antmicro/jetson-agx-thor-baseboard/SoM_ctrl.kicad_sch

## KiCad design SoM_ctrl.kicad_sch (2025-08-14)

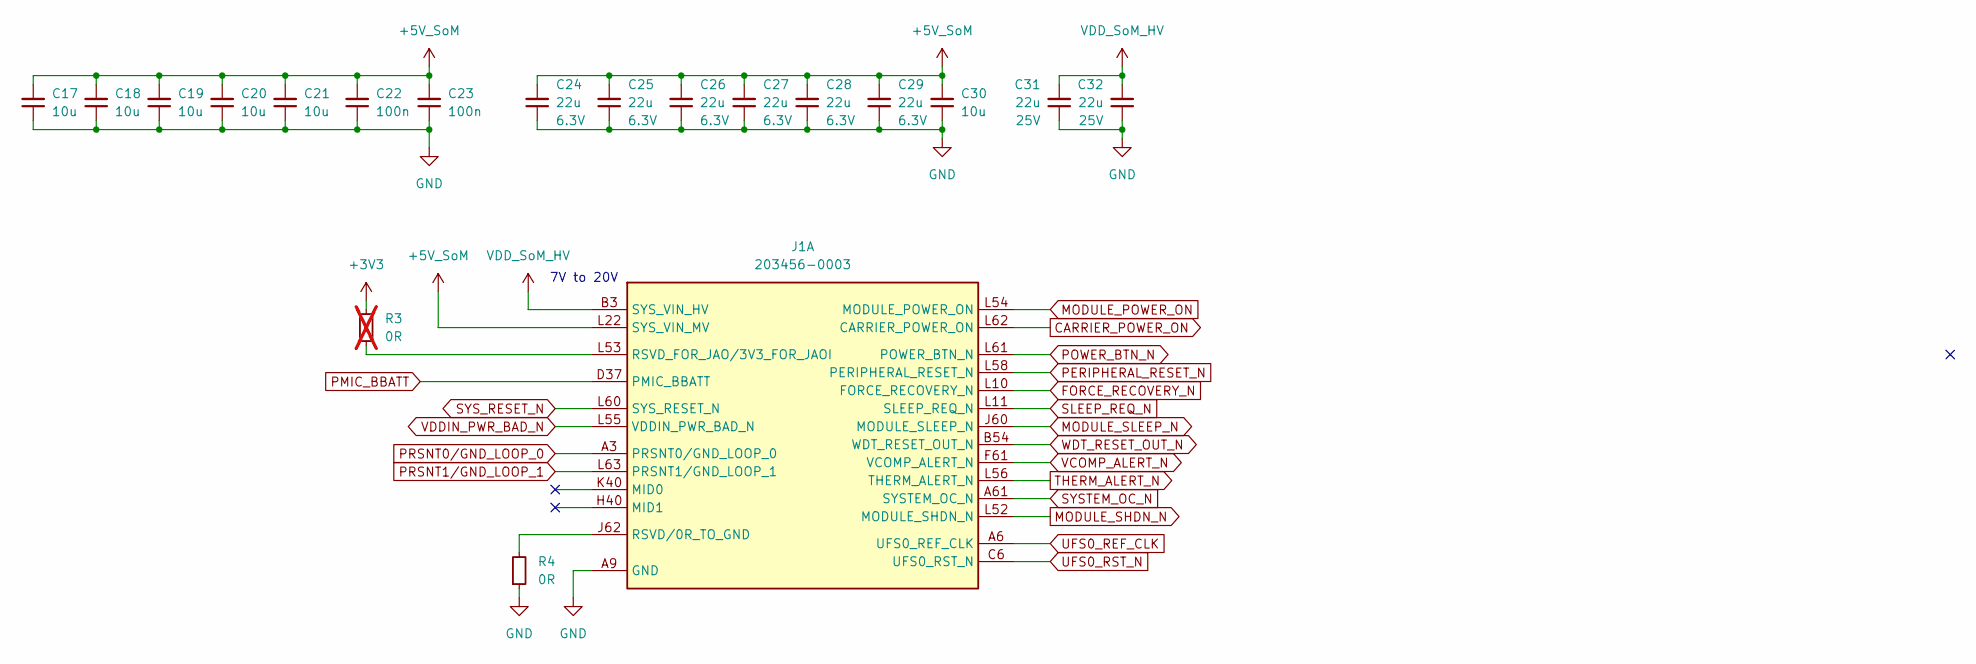
[picture p2: schematic SoM_ctrl.kicad_sch]

Parts:
C17, C18, C19, C20, C21, C30: C_10u_0603; C_0603_1608Metric; MPN GRM188R61A106KE69D
C22, C23: C_100n_16V_X7R_0402; C_0402_1005Metric; Voltage 16V; MPN C0402C104J4RAC7411
C24, C25, C26, C27, C28, C29: C_22u_6.3V_X7R_0805; C_0805_2012Metric; Voltage 6.3V; MPN GRM21BZ70J226ME44L
C31, C32: C_22u_25V_0805; C_0805_2012Metric; Voltage 25V; MPN CL21A226MAYNNNE
J1: Hermaphroditic_Molex_203456-0003_CUSTOM_Jetson_Or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; Conn_Hermaphroditic_Molex_203456-0003_mirrored; MPN 203456-0003
R3: R_0R_0603; R_0603_1608Metric; MPN CR0603-J/-000ELF; not fitted
R4: R_0R_0402; R_0402_1005Metric; MPN ERJ2GE0R00X

Connections:
+3V3: R3.2
+5V_SoM: C17.2, C18.2, C19.2, C20.2, C21.2, C22.2, C23.2, C24.2, C25.2, C26.2, C27.2, C28.2, C29.2, C30.2, J1.L22 (SYS_VIN_MV), J1.L23 (SYS_VIN_MV), J1.L26 (SYS_VIN_MV), J1.L27 (SYS_VIN_MV), J1.L30 (SYS_VIN_MV), J1.L31 (SYS_VIN_MV), J1.L34 (SYS_VIN_MV), J1.L35 (SYS_VIN_MV), J1.L38 (SYS_VIN_MV), J1.L39 (SYS_VIN_MV)
CARRIER_POWER_ON: J1.L62 (CARRIER_POWER_ON)
FORCE_RECOVERY_N: J1.L10 (FORCE_RECOVERY_N)
GND: C17.1, C18.1, C19.1, C20.1, C21.1, C22.1, C23.1, C24.1, C25.1, C26.1, C27.1, C28.1, C29.1, C30.1, C31.1, C32.1, J1.A9 (GND), J1.A12 (GND), J1.A13 (GND), J1.A16 (GND), J1.A17 (GND), J1.A20 (GND), J1.A21 (GND), J1.A24 (GND), J1.A25 (GND), J1.A28 (GND), J1.A29 (GND), J1.A32 (GND), J1.A33 (GND), J1.A36 (GND), J1.A37 (GND), J1.A40 (GND), J1.A43 (GND), J1.A46 (GND), J1.A49 (GND), J1.A52 (GND), J1.A63 (GND), J1.B4 (GND), J1.B7 (GND), J1.B11 (GND), J1.B14 (GND), J1.B15 (GND), J1.B18 (GND), J1.B19 (GND), J1.B22 (GND), J1.B23 (GND), J1.B26 (GND), J1.B27 (GND), J1.B30 (GND), J1.B31 (GND), J1.B34 (GND), J1.B35 (GND), J1.B38 (GND), J1.B39 (GND), J1.B41 (GND), J1.B44 (GND), J1.B47 (GND), J1.B50 (GND), J1.B53 (GND), J1.B57 (GND), J1.C3 (GND), J1.C9 (GND), J1.C12 (GND), J1.C13 (GND), J1.C16 (GND), J1.C17 (GND), J1.C20 (GND), J1.C21 (GND), J1.C24 (GND), J1.C25 (GND), J1.C28 (GND), J1.C29 (GND), J1.C32 (GND), J1.C33 (GND), J1.C36 (GND), J1.C37 (GND), J1.C40 (GND), J1.C43 (GND), J1.C46 (GND), J1.C49 (GND), J1.C52 (GND), J1.C62 (GND), J1.D4 (GND), J1.D7 (GND), J1.D11 (GND), J1.D14 (GND), J1.D15 (GND), J1.D18 (GND), J1.D19 (GND), J1.D22 (GND), J1.D23 (GND), J1.D26 (GND), J1.D27 (GND), J1.D30 (GND), J1.D31 (GND), J1.D34 (GND), J1.D35 (GND), J1.D38 (GND), J1.D39 (GND), J1.D41 (GND), J1.D44 (GND), J1.D47 (GND), J1.D50 (GND), J1.D53 (GND), J1.D57 (GND), J1.D63 (GND), J1.E3 (GND), J1.E9 (GND), J1.E12 (GND), J1.E13 (GND), J1.E16 (GND), J1.E17 (GND), J1.E20 (GND), J1.E21 (GND), J1.E24 (GND), J1.E25 (GND), J1.E28 (GND), J1.E29 (GND), J1.E32 (GND), J1.E33 (GND), J1.E36 (GND), J1.E37 (GND), J1.E40 (GND), J1.E43 (GND), J1.E46 (GND), J1.E49 (GND), J1.E52 (GND), J1.E57 (GND), J1.E62 (GND), J1.F4 (GND), J1.F7 (GND), J1.F11 (GND), J1.F14 (GND), J1.F15 (GND), J1.F18 (GND), J1.F19 (GND), J1.F22 (GND), J1.F23 (GND), J1.F26 (GND), J1.F27 (GND), J1.F30 (GND), J1.F31 (GND), J1.F34 (GND), J1.F35 (GND), J1.F38 (GND), J1.F39 (GND), J1.F41 (GND), J1.F44 (GND), J1.F47 (GND), J1.F50 (GND), J1.F57 (GND), J1.F62 (GND), J1.G3 (GND), J1.G9 (GND), J1.G12 (GND), J1.G13 (GND), J1.G16 (GND), J1.G17 (GND), J1.G20 (GND), J1.G21 (GND), J1.G24 (GND), J1.G25 (GND), J1.G28 (GND), J1.G29 (GND), J1.G32 (GND), J1.G33 (GND), J1.G36 (GND), J1.G37 (GND), J1.G40 (GND), J1.G43 (GND), J1.G46 (GND), J1.G49 (GND), J1.G52 (GND), J1.G57 (GND), J1.G62 (GND), J1.H4 (GND), J1.H7 (GND), J1.H11 (GND), J1.H14 (GND), J1.H15 (GND), J1.H18 (GND), J1.H19 (GND), J1.H22 (GND), J1.H23 (GND), J1.H26 (GND), J1.H27 (GND), J1.H30 (GND), J1.H31 (GND), J1.H34 (GND), J1.H35 (GND), J1.H38 (GND), J1.H39 (GND), J1.H41 (GND), J1.H44 (GND), J1.H47 (GND), J1.H50 (GND), J1.H56 (GND), J1.H63 (GND), J1.J3 (GND), J1.J8 (GND), J1.J12 (GND), J1.J13 (GND), J1.J16 (GND), J1.J17 (GND), J1.J20 (GND), J1.J21 (GND), J1.J24 (GND), J1.J25 (GND), J1.J28 (GND), J1.J29 (GND), J1.J32 (GND), J1.J33 (GND), J1.J36 (GND), J1.J37 (GND), J1.J40 (GND), J1.J43 (GND), J1.J46 (GND), J1.J49 (GND), J1.J56 (GND), J1.K4 (GND), J1.K8 (GND), J1.K11 (GND), J1.K14 (GND), J1.K15 (GND), J1.K18 (GND), J1.K19 (GND), J1.K22 (GND), J1.K23 (GND), J1.K26 (GND), J1.K27 (GND), J1.K30 (GND), J1.K31 (GND), J1.K34 (GND), J1.K35 (GND), J1.K38 (GND), J1.K39 (GND), J1.K41 (GND), J1.K42 (GND), J1.K45 (GND), J1.K48 (GND), J1.K55 (GND), J1.K63 (GND), J1.L3 (GND), J1.L7 (GND), J1.L12 (GND), J1.L13 (GND), J1.L16 (GND), J1.L17 (GND), J1.L20 (GND), J1.L21 (GND), J1.L24 (GND), J1.L25 (GND), J1.L28 (GND), J1.L29 (GND), J1.L32 (GND), J1.L33 (GND), J1.L36 (GND), J1.L37 (GND), J1.L40 (GND), J1.L43 (GND), J1.L46 (GND), R4.1
MODULE_POWER_ON: J1.L54 (MODULE_POWER_ON)
MODULE_SHDN_N: J1.L52 (MODULE_SHDN_N)
MODULE_SLEEP_N: J1.J60 (MODULE_SLEEP_N)
unnamed: J1.J62 (RSVD/0R_TO_GND), R4.2
unnamed: J1.L53 (RSVD_FOR_JAO/3V3_FOR_JAOI), R3.1
PERIPHERAL_RESET_N: J1.L58 (PERIPHERAL_RESET_N)
PMIC_BBATT: J1.D37 (PMIC_BBATT)
POWER_BTN_N: J1.L61 (POWER_BTN_N)
PRSNT0/GND_LOOP_0: J1.A3 (PRSNT0/GND_LOOP_0)
PRSNT1/GND_LOOP_1: J1.L63 (PRSNT1/GND_LOOP_1)
SLEEP_REQ_N: J1.L11 (SLEEP_REQ_N)
SYSTEM_OC_N: J1.A61 (SYSTEM_OC_N)
SYS_RESET_N: J1.L60 (SYS_RESET_N)
THERM_ALERT_N: J1.L56 (THERM_ALERT_N)
UFS0_REF_CLK: J1.A6 (UFS0_REF_CLK)
UFS0_RST_N: J1.C6 (UFS0_RST_N)
VCOMP_ALERT_N: J1.F61 (VCOMP_ALERT_N)
VDDIN_PWR_BAD_N: J1.L55 (VDDIN_PWR_BAD_N)
VDD_SoM_HV: C31.2, C32.2, J1.B3 (SYS_VIN_HV), J1.B63 (SYS_VIN_HV), J1.C1 (SYS_VIN_HV), J1.C2 (SYS_VIN_HV), J1.C63 (SYS_VIN_HV), J1.C64 (SYS_VIN_HV), J1.C65 (SYS_VIN_HV), J1.D1 (SYS_VIN_HV), J1.D2 (SYS_VIN_HV), J1.D3 (SYS_VIN_HV), J1.D64 (SYS_VIN_HV), J1.D65 (SYS_VIN_HV), J1.E1 (SYS_VIN_HV), J1.E2 (SYS_VIN_HV), J1.E63 (SYS_VIN_HV), J1.E64 (SYS_VIN_HV), J1.E65 (SYS_VIN_HV), J1.F1 (SYS_VIN_HV), J1.F2 (SYS_VIN_HV), J1.F3 (SYS_VIN_HV), J1.F63 (SYS_VIN_HV), J1.F64 (SYS_VIN_HV), J1.F65 (SYS_VIN_HV), J1.G1 (SYS_VIN_HV), J1.G2 (SYS_VIN_HV), J1.G63 (SYS_VIN_HV), J1.G64 (SYS_VIN_HV), J1.G65 (SYS_VIN_HV), J1.H1 (SYS_VIN_HV), J1.H2 (SYS_VIN_HV), J1.H3 (SYS_VIN_HV), J1.H64 (SYS_VIN_HV), J1.H65 (SYS_VIN_HV), J1.J1 (SYS_VIN_HV), J1.J2 (SYS_VIN_HV), J1.J63 (SYS_VIN_HV), J1.J64 (SYS_VIN_HV), J1.J65 (SYS_VIN_HV), J1.K3 (SYS_VIN_HV)
WDT_RESET_OUT_N: J1.B54 (WDT_RESET_OUT_N)

Notes on the sheet:
7V to 20V
