antmicro/jetson-agx-thor-baseboard/csi.kicad_sch

## KiCad design csi.kicad_sch (2026-02-19, an earlier design)

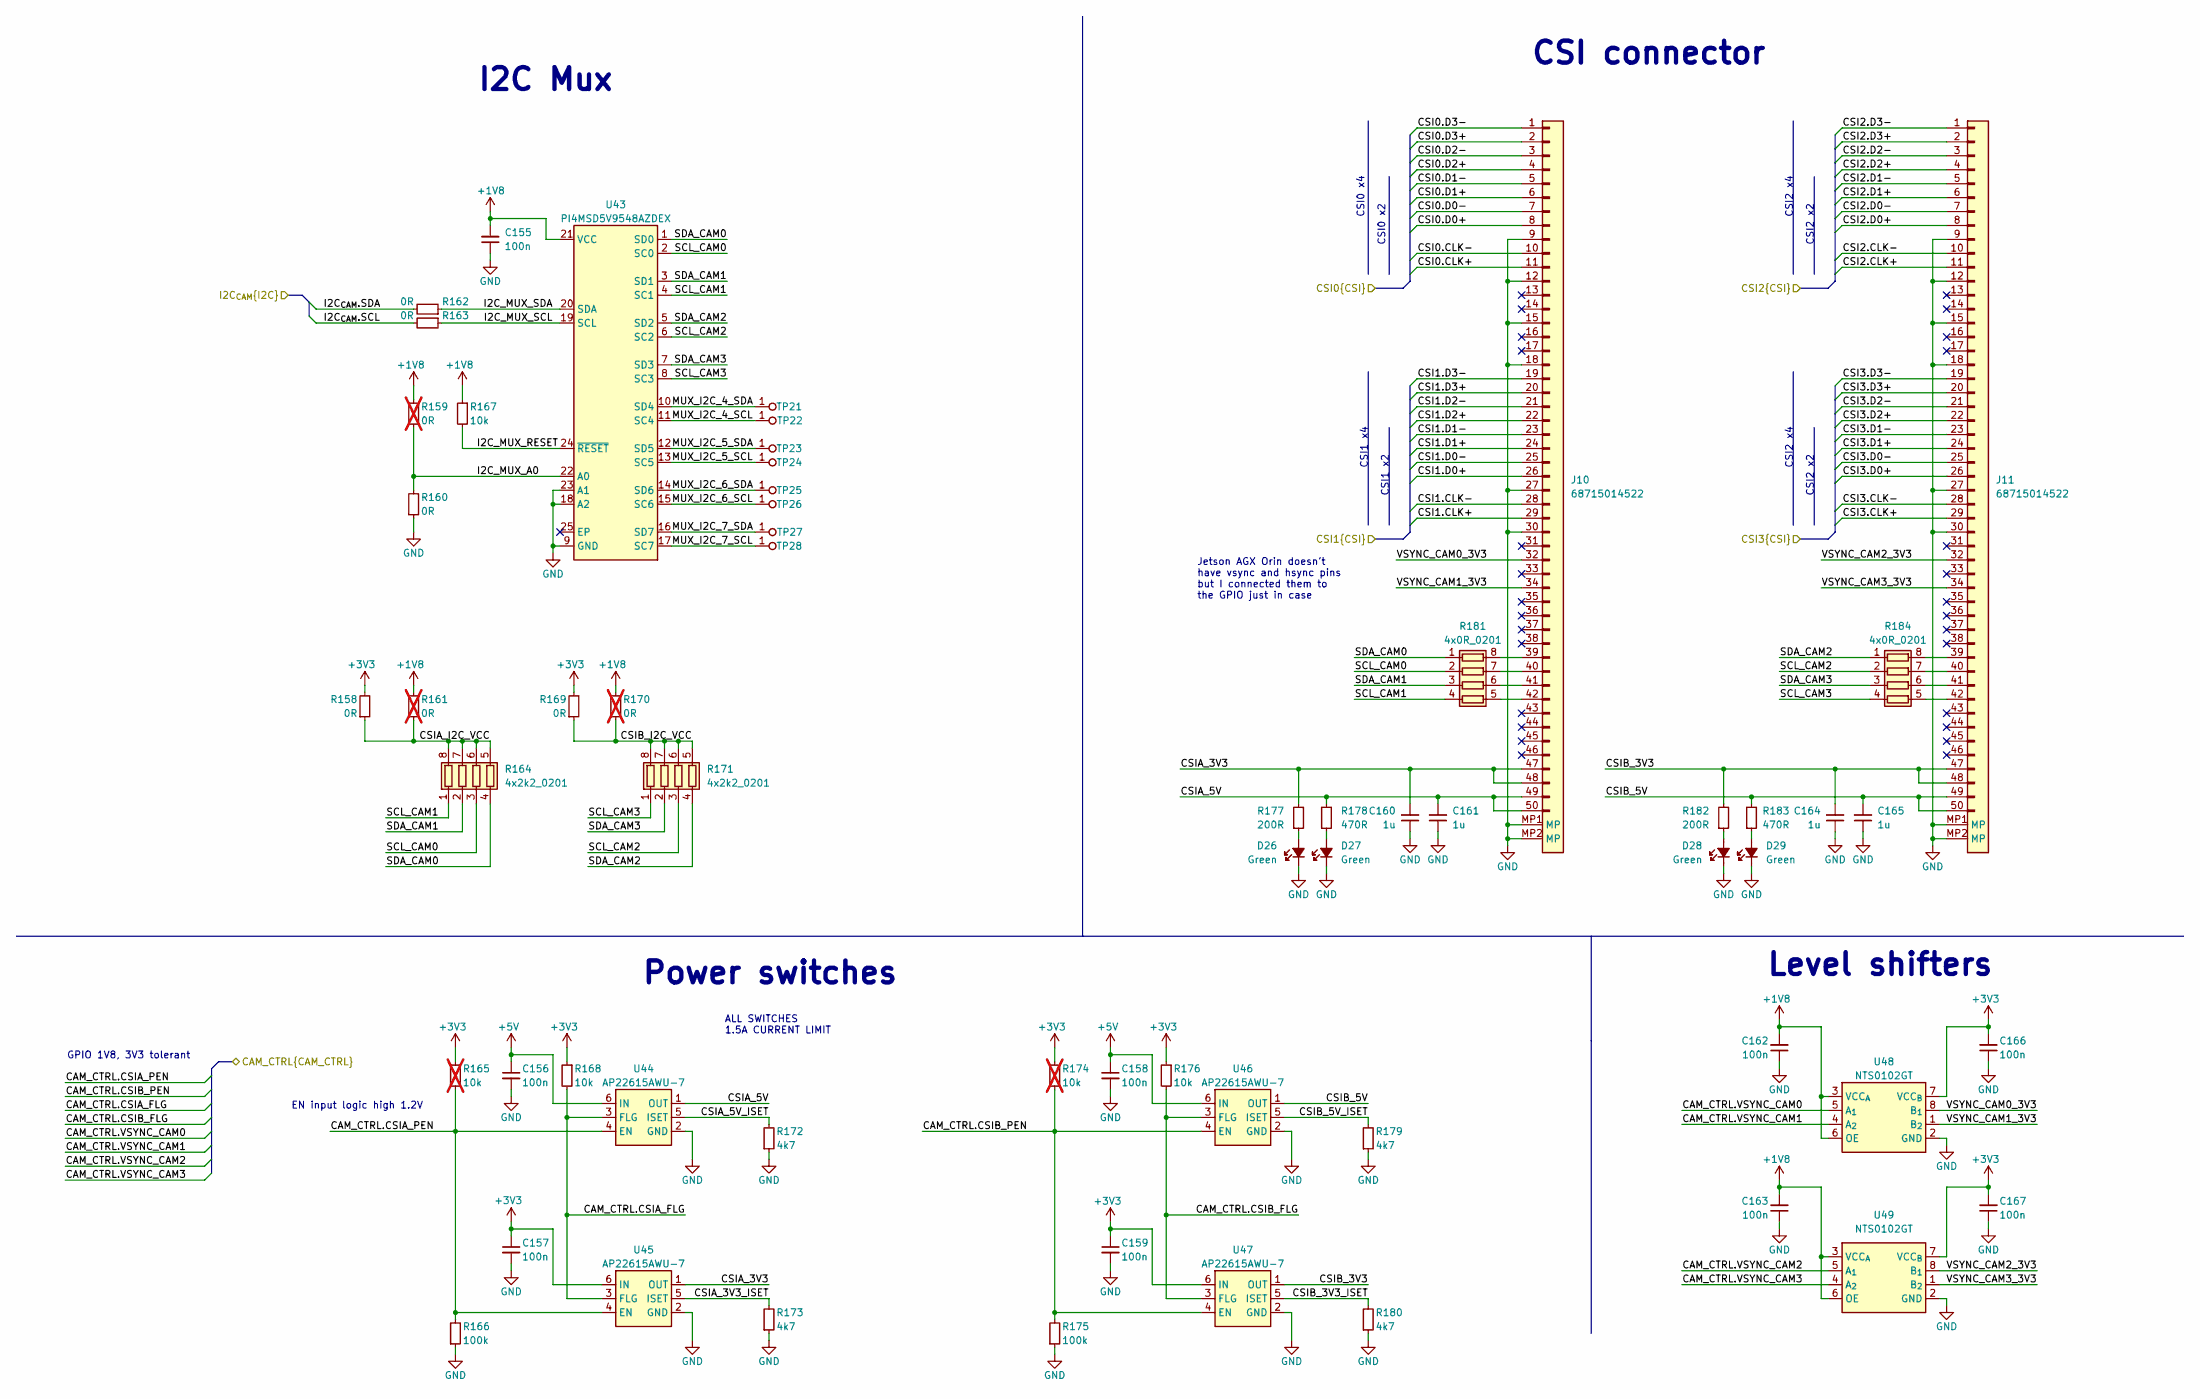
[picture p3: schematic csi.kicad_sch]

Parts:
C155, C156, C157, C158, C159, C162, C163, C166, C167: C_100n_0402; C_0402_1005Metric; Voltage 50V; MPN GRM155R61H104KE14D
C160, C161, C164, C165: C_1u_0402; C_0402_1005Metric; MPN C1005X6S1A105K050BC
D26, D27, D28, D29: LED_G_0603_LTST-C190GKT; LED_0603_1608Metric_G; MPN LTST-C190GKT
J10, J11: Conn_FFC_WE_68715014522; Conn_FFC_WE_68715014x22; MPN 68715014522
R158, R160, R162, R163, R169: R_0R_0402; R_0402_1005Metric; MPN ERJ2GE0R00X
R159, R161, R170: R_0R_0402; R_0402_1005Metric; MPN ERJ2GE0R00X; not fitted
R164, R171: R_4x2k2_0201_array; R_Array_4x0201_Panasonic_EXB18V; MPN EXB-18V222JX
R165, R174: R_10k_0402; R_0402_1005Metric; Tolerance 1%; MPN CR0402-FX-1002GLF; not fitted
R166, R175: R_100k_0402; R_0402_1005Metric; Tolerance 1%; MPN CR0402-FX-1003GLF
R167, R168, R176: R_10k_0402; R_0402_1005Metric; Tolerance 1%; MPN CR0402-FX-1002GLF
R172, R173, R179, R180: R_4k7_0402; R_0402_1005Metric; Tolerance 1%; MPN CR0402-FX-4701GLF
R177, R182: R_200R_0402; R_0402_1005Metric; Tolerance 1%; MPN CR0402-FX-2000GLF
R178, R183: R_470R_0402; R_0402_1005Metric; Tolerance 1%; MPN CR0402-FX-4700GLF
R181, R184: R_4x0R_0201_array; R_Array_4x0201_Panasonic_EXB18V; MPN EXB-18VR000X
TP21, TP22, TP23, TP24, TP25, TP26, TP27, TP28: TP_0.75mm_SMD; TP_SMD_0.75mm
U43: PI4MSD5V9548AZDEX; VQFN-24-1EP_3.8x3.8x1.0mm_P0.5mm; MPN PI4MSD5V9548AZDEX
U44, U45, U46, U47: AP22615A_TSOT26; TSOT23-6; MPN AP22615AWU-7
U48, U49: NTS0102_XSON; XSON-8_1x1.95mm_P0.5mm; MPN NTS0102GT

Connections:
+1V8: C155.2, C162.2, C163.2, R159.2, R161.2, R167.1, R170.2, U43.21 (VCC), U48.3 (VCC_{A}), U48.6 (OE), U49.3 (VCC_{A}), U49.6 (OE)
+3V3: C157.1, C159.1, C166.2, C167.2, R158.2, R165.2, R168.1, R169.2, R174.2, R176.1, U45.6 (IN), U47.6 (IN), U48.7 (VCC_{B}), U49.7 (VCC_{B})
+5V: C156.1, C158.1, U44.6 (IN), U46.6 (IN)
CAM_CTRL.CSIA_FLG: R168.2, U44.3 (FLG), U45.3 (FLG)
CAM_CTRL.CSIA_PEN: R165.1, R166.2, U44.4 (EN), U45.4 (EN)
CAM_CTRL.CSIB_FLG: R176.2, U46.3 (FLG), U47.3 (FLG)
CAM_CTRL.CSIB_PEN: R174.1, R175.2, U46.4 (EN), U47.4 (EN)
CAM_CTRL.VSYNC_CAM0: U48.5 (A_{1})
CAM_CTRL.VSYNC_CAM1: U48.4 (A_{2})
CAM_CTRL.VSYNC_CAM2: U49.5 (A_{1})
CAM_CTRL.VSYNC_CAM3: U49.4 (A_{2})
CSI0.CLK+: J10.11
CSI0.CLK-: J10.10
CSI0.D0+: J10.8
CSI0.D0-: J10.7
CSI0.D1+: J10.6
CSI0.D1-: J10.5
CSI0.D2+: J10.4
CSI0.D2-: J10.3
CSI0.D3+: J10.2
CSI0.D3-: J10.1
CSI1.CLK+: J10.29
CSI1.CLK-: J10.28
CSI1.D0+: J10.26
CSI1.D0-: J10.25
CSI1.D1+: J10.24
CSI1.D1-: J10.23
CSI1.D2+: J10.22
CSI1.D2-: J10.21
CSI1.D3+: J10.20
CSI1.D3-: J10.19
CSI2.CLK+: J11.11
CSI2.CLK-: J11.10
CSI2.D0+: J11.8
CSI2.D0-: J11.7
CSI2.D1+: J11.6
CSI2.D1-: J11.5
CSI2.D2+: J11.4
CSI2.D2-: J11.3
CSI2.D3+: J11.2
CSI2.D3-: J11.1
CSI3.CLK+: J11.29
CSI3.CLK-: J11.28
CSI3.D0+: J11.26
CSI3.D0-: J11.25
CSI3.D1+: J11.24
CSI3.D1-: J11.23
CSI3.D2+: J11.22
CSI3.D2-: J11.21
CSI3.D3+: J11.20
CSI3.D3-: J11.19
CSIA_3V3: C160.2, J10.47, J10.48, R177.2, U45.1 (OUT)
CSIA_3V3_ISET: R173.2, U45.5 (ISET)
CSIA_5V: C161.2, J10.49, J10.50, R178.2, U44.1 (OUT)
CSIA_5V_ISET: R172.2, U44.5 (ISET)
CSIA_I2C_VCC: R158.1, R161.1, R164.5 (R4.2), R164.6 (R3.2), R164.7 (R2.2), R164.8 (R1.2)
CSIB_3V3: C164.2, J11.47, J11.48, R182.2, U47.1 (OUT)
CSIB_3V3_ISET: R180.2, U47.5 (ISET)
CSIB_5V: C165.2, J11.49, J11.50, R183.2, U46.1 (OUT)
CSIB_5V_ISET: R179.2, U46.5 (ISET)
CSIB_I2C_VCC: R169.1, R170.1, R171.5 (R4.2), R171.6 (R3.2), R171.7 (R2.2), R171.8 (R1.2)
GND: C155.1, C156.2, C157.2, C158.2, C159.2, C160.1, C161.1, C162.1, C163.1, C164.1, C165.1, C166.1, C167.1, D26.1 (C), D27.1 (C), D28.1 (C), D29.1 (C), J10.9, J10.12, J10.15, J10.18, J10.27, J10.30, J10.MP1 (MP), J10.MP2 (MP), J11.9, J11.12, J11.15, J11.18, J11.27, J11.30, J11.MP1 (MP), J11.MP2 (MP), R160.1, R166.1, R172.1, R173.1, R175.1, R179.1, R180.1, U43.9 (GND), U43.18 (A2), U43.23 (A1), U44.2 (GND), U45.2 (GND), U46.2 (GND), U47.2 (GND), U48.2 (GND), U49.2 (GND)
I2C_MUX_A0: R159.1, R160.2, U43.22 (A0)
I2C_MUX_RESET: R167.2, U43.24 (~RESET)
I2C_MUX_SCL: R163.1, U43.19 (SCL)
I2C_MUX_SDA: R162.1, U43.20 (SDA)
I2C_{CAM}.SCL: R163.2
I2C_{CAM}.SDA: R162.2
MUX_I2C_4_SCL: TP22.1, U43.11 (SC4)
MUX_I2C_4_SDA: TP21.1, U43.10 (SD4)
MUX_I2C_5_SCL: TP24.1, U43.13 (SC5)
MUX_I2C_5_SDA: TP23.1, U43.12 (SD5)
MUX_I2C_6_SCL: TP26.1, U43.15 (SC6)
MUX_I2C_6_SDA: TP25.1, U43.14 (SD6)
MUX_I2C_7_SCL: TP28.1, U43.17 (SC7)
MUX_I2C_7_SDA: TP27.1, U43.16 (SD7)
unnamed: D26.2 (A), R177.1
unnamed: D27.2 (A), R178.1
unnamed: D28.2 (A), R182.1
unnamed: D29.2 (A), R183.1
unnamed: J10.39, R181.8 (R1.2)
unnamed: J10.40, R181.7 (R2.2)
unnamed: J10.41, R181.6 (R3.2)
unnamed: J10.42, R181.5 (R4.2)
unnamed: J11.39, R184.8 (R1.2)
unnamed: J11.40, R184.7 (R2.2)
unnamed: J11.41, R184.6 (R3.2)
unnamed: J11.42, R184.5 (R4.2)
SCL_CAM0: R164.3 (R3.1), R181.2 (R2.1), U43.2 (SC0)
SCL_CAM1: R164.1 (R1.1), R181.4 (R4.1), U43.4 (SC1)
SCL_CAM2: R171.3 (R3.1), R184.2 (R2.1), U43.6 (SC2)
SCL_CAM3: R171.1 (R1.1), R184.4 (R4.1), U43.8 (SC3)
SDA_CAM0: R164.4 (R4.1), R181.1 (R1.1), U43.1 (SD0)
SDA_CAM1: R164.2 (R2.1), R181.3 (R3.1), U43.3 (SD1)
SDA_CAM2: R171.4 (R4.1), R184.1 (R1.1), U43.5 (SD2)
SDA_CAM3: R171.2 (R2.1), R184.3 (R3.1), U43.7 (SD3)
VSYNC_CAM0_3V3: J10.32, U48.8 (B_{1})
VSYNC_CAM1_3V3: J10.34, U48.1 (B_{2})
VSYNC_CAM2_3V3: J11.32, U49.8 (B_{1})
VSYNC_CAM3_3V3: J11.34, U49.1 (B_{2})

Notes on the sheet:
EN input logic high 1.2V
CSI1 x4
CSI0 x2
CSI0 x4
CSI2 x4
Power switches
Level shifters
GPIO 1V8, 3V3 tolerant
CSI2 x2
ALL SWITCHES 1.5A CURRENT LIMIT
I2C Mux
CSI connector
Jetson AGX Orin doesn't have vsync and hsync pins but I connected them to the GPIO just in case
CSI1 x2
