antmicro/jetson-agx-thor-baseboard/dcdc.kicad_sch

## KiCad design dcdc.kicad_sch (2026-03-19, an earlier design)

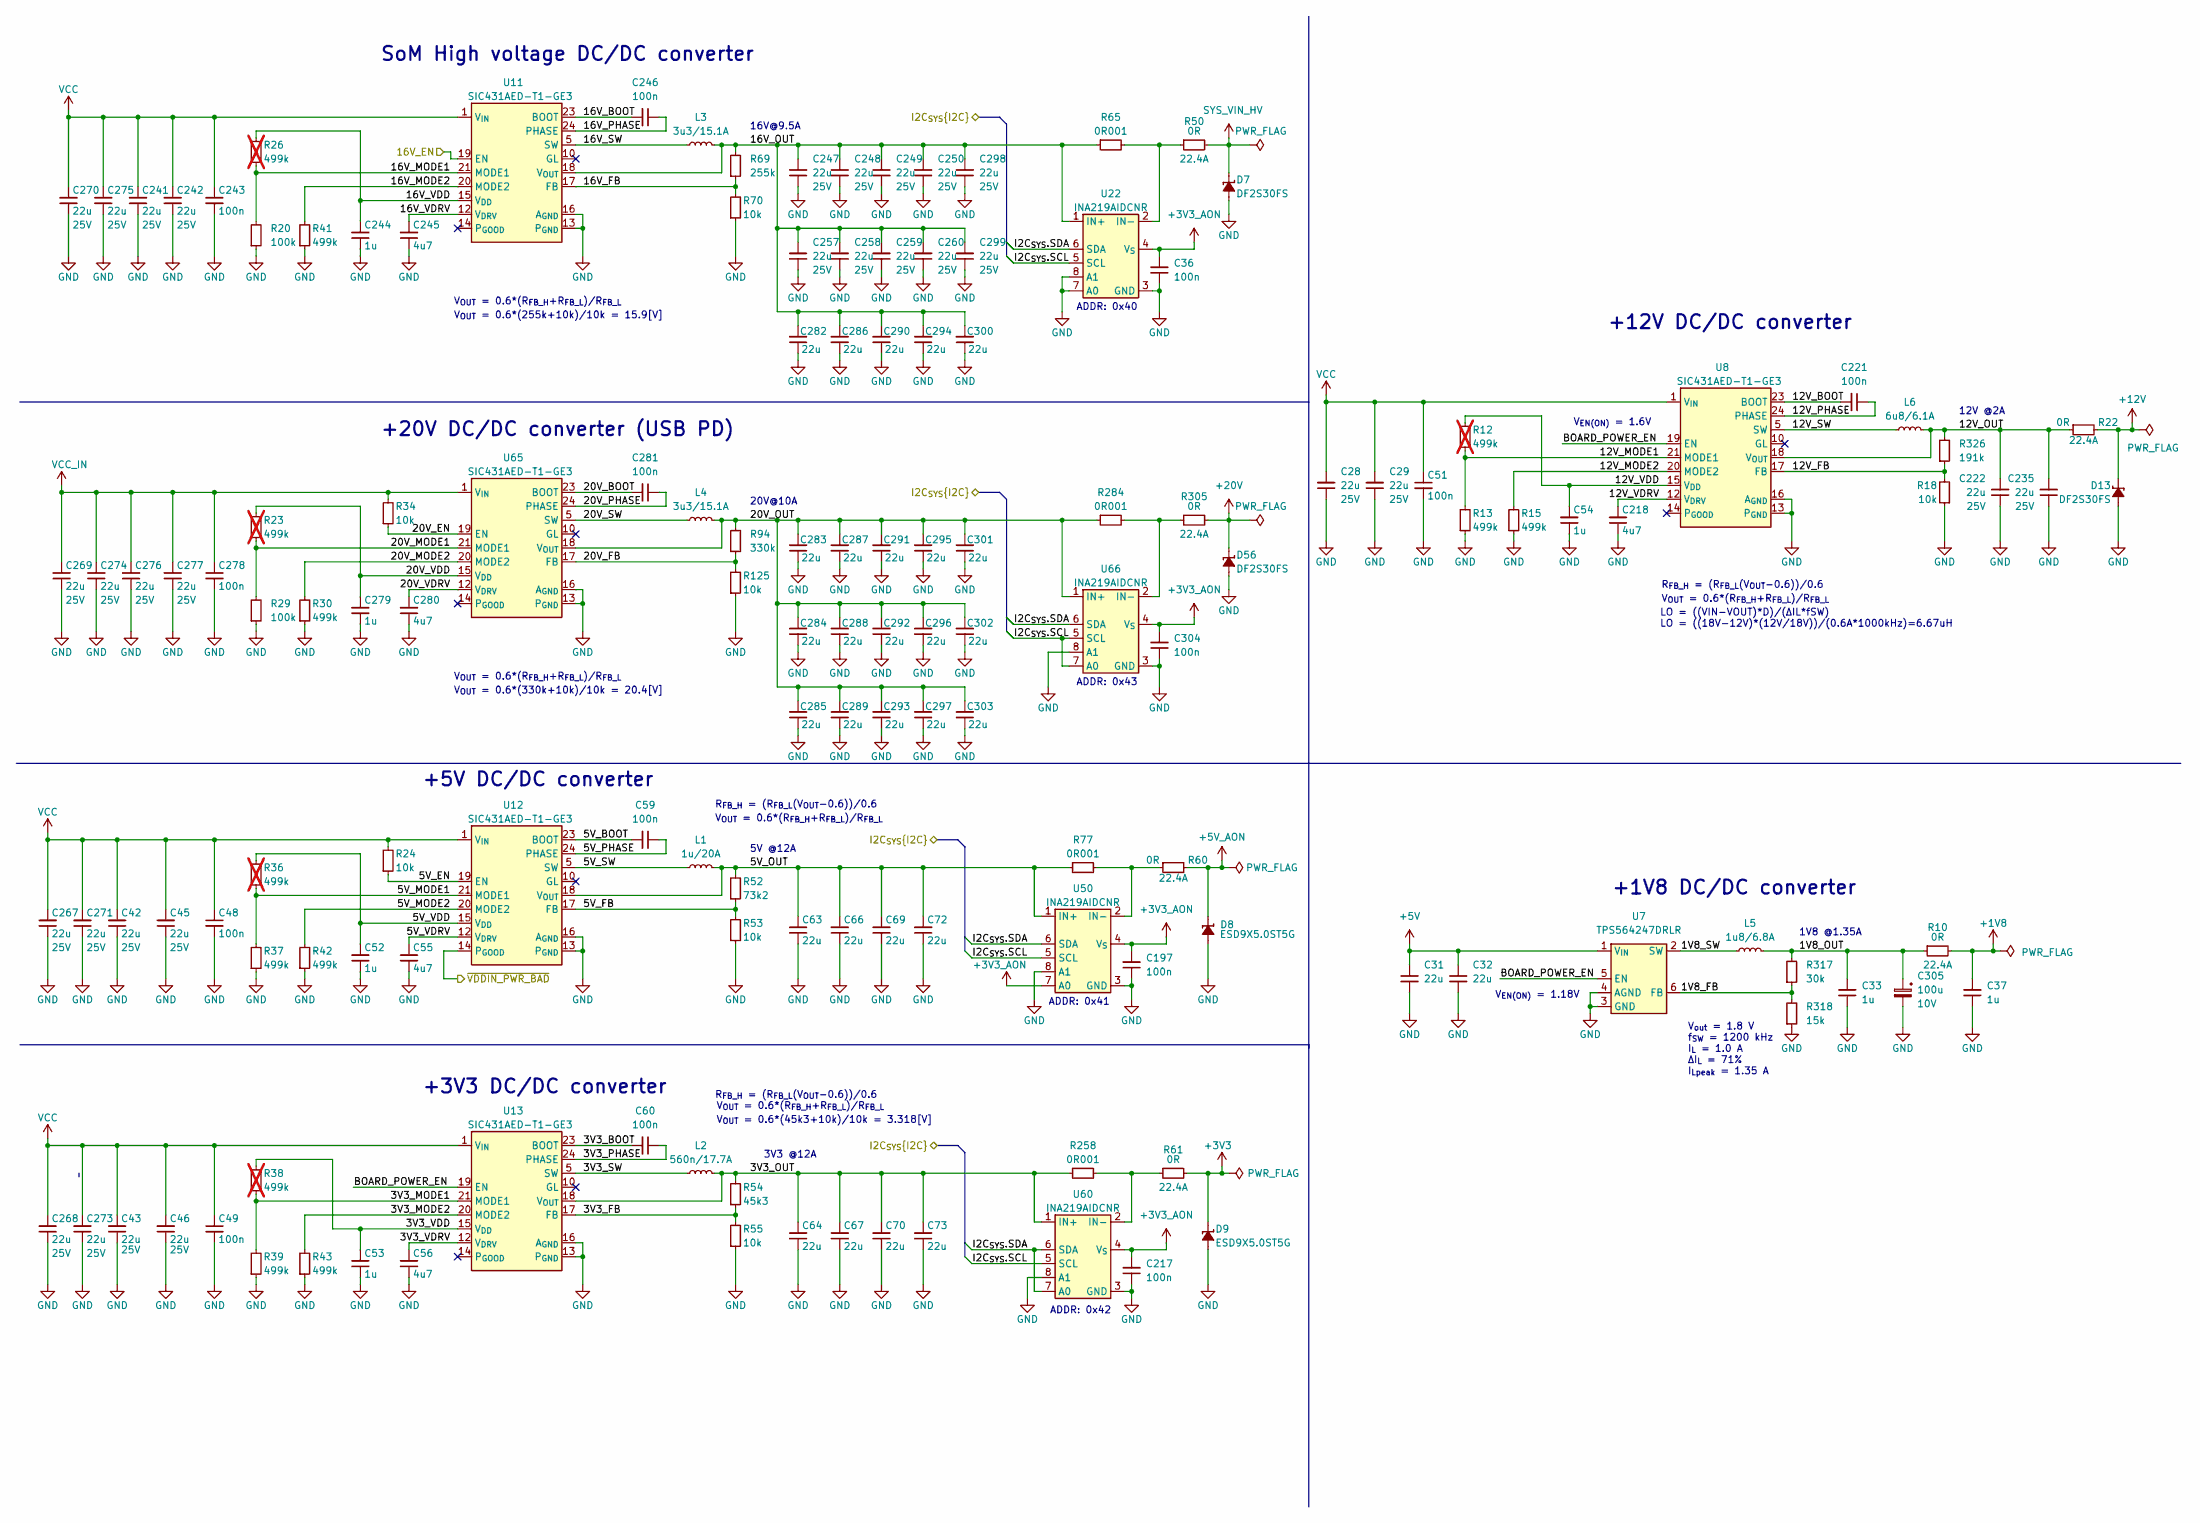
[picture p4: schematic dcdc.kicad_sch]

Parts:
C28, C29, C42, C43, C45, C46, C222, C235, C241, C242, C247, C248, C249, C250, C257, C258, C259, C260, C267, C268, C269, C270, C271, C273, C274, C275, C276, C277, C298, C299: C_22u_25V_0805; C_0805_2012Metric; Voltage 25V; MPN CL21A226MAYNNNE
C31, C32, C63, C64, C66, C67, C69, C70, C72, C73: C_22u_16V_0603; C_0603_1608Metric_EIA; Voltage 16V; MPN CL10A226MO7JZNC
C33, C37, C52, C53, C54, C244, C279: C_1u_0402; C_0402_1005Metric; MPN C1005X6S1A105K050BC
C36, C48, C49, C51, C59, C60, C197, C217, C221, C243, C246, C278, C281, C304: C_100n_0402; C_0402_1005Metric; Voltage 50V; MPN GRM155R61H104KE14D
C55, C56, C218, C245, C280: C_4u7_25V_0402; C_0402_1005Metric; Voltage 25V; MPN GRM155C61E475ME15J
C282, C283, C284, C285, C286, C287, C288, C289, C290, C291, C292, C293, C294, C295, C296, C297, C300, C301, C302, C303: C_22u_1206_35V; C_1206_3216Metric; Voltage 35V; MPN 3216X5R1V226M160AC
C305: C_Pol_100u_10V_KEMET-T520-B; C_Pol_EIA-B; Voltage 10V; MPN T520B107M010ATE070
D7, D13, D56: DF2S30FS_SOD; SOD-923; MPN DF2S30FS
D8, D9: ESD9X5.0ST5G; SOD-923; MPN ESD9X5.0ST5G
L1: L_1u_20A_Bourns-SRP6050CA; L_Bourns-SRP6050CA; MPN SRP6050CA-1R0M
L2: L_560n_17.7A_Bourns-SRP5030CA; L_Bourns-SRP5030CA; MPN SRP5030CA-R56M
L3, L4: L_3u3_15.1A_Coilcraft-XAL7070; L_Coilcraft-XAL7070; MPN XAL7070-332MEB
L5: L_1u8_6.8A_WE-MAPI-4020; L_WE-MAPI-4020; MPN 74438356018
L6: L_6u8_6.1A_MPS-MPL-AL5050; L_MPS-MPL-AL5050; MPN MPL-AL5050-6R8
R10, R22, R50, R60, R61, R305: R_0R_22.4A_0603; R_0603_1608Metric; Tolerance template_tolerance; MPN PMR03EZPJ000
R12, R23, R26, R36, R38: R_499k_0402; R_0402_1005Metric; Tolerance 1%; MPN CR0402-FX-4993GLF; not fitted
R13, R15, R30, R37, R39, R41, R42, R43: R_499k_0402; R_0402_1005Metric; Tolerance 1%; MPN CR0402-FX-4993GLF
R18, R24, R34, R53, R55, R70, R125: R_10k_0402; R_0402_1005Metric; Tolerance 1%; MPN CR0402-FX-1002GLF
R20, R29: R_100k_0402; R_0402_1005Metric; Tolerance 1%; MPN CR0402-FX-1003GLF
R52: R_73k2_0402; R_0402_1005Metric; Tolerance 1%; MPN CR0402-FX-7322GLF
R54: R_45k3_0402; R_0402_1005Metric; Tolerance 1%; MPN CR0402-FX-4532GLF
R65, R77, R258, R284: R_0R001_0805; R_0805_2012Metric; Tolerance 1%; MPN MSMA0805R0010FSM
R69: R_255k_0402; R_0402_1005Metric; Tolerance 1%; MPN CR0402-FX-2553GLF
R94: R_330k_0402; R_0402_1005Metric; Tolerance 1%; MPN CR0402-FX-3303GLF
R317: R_30k_0402; R_0402_1005Metric; Tolerance 1%; MPN CR0402-FX-3002GLF
R318: R_15k_0402; R_0402_1005Metric; Tolerance 1%; MPN CR0402-FX-1502GLF
R326: R_191k_0402; R_0402_1005Metric; Tolerance 1%; MPN CR0402-FX-1913GLF
U7: TPS564247DRLR; SOT-563; MPN TPS564247DRLR
U8, U11, U12, U13, U65: SIC431AED-T1-GE3; MLP44-24L_4x4x0.75mm; MPN SIC431AED-T1-GE3
U22, U50, U60, U66: INA219AIDCNR; SOT-23-8; MPN INA219AIDCNR

Connections:
1V8_FB: R317.1, R318.2, U7.6 (FB)
1V8_OUT: C33.2, C305.1, L5.2, R10.1, R317.2
1V8_SW: L5.1, U7.2 (SW)
3V3_BOOT: C60.2, U13.23 (BOOT)
3V3_FB: R54.1, R55.2, U13.17 (FB)
3V3_MODE1: R38.1, R39.2, U13.21 (MODE1)
3V3_MODE2: R43.2, U13.20 (MODE2)
3V3_OUT: C64.2, C67.2, C70.2, C73.2, L2.2, R54.2, R258.1, U13.18 (V_{OUT}), U60.1 (IN+)
3V3_PHASE: C60.1, U13.24 (PHASE)
3V3_SW: L2.1, U13.5 (SW), U13.6 (SW), U13.7 (SW), U13.8 (SW), U13.9 (SW)
3V3_VDD: C53.2, R38.2, U13.15 (V_{DD})
3V3_VDRV: C56.2, U13.12 (V_{DRV})
5V_BOOT: C59.2, U12.23 (BOOT)
5V_EN: R24.1, U12.19 (EN)
5V_FB: R52.1, R53.2, U12.17 (FB)
5V_MODE1: R36.1, R37.2, U12.21 (MODE1)
5V_MODE2: R42.2, U12.20 (MODE2)
5V_OUT: C63.2, C66.2, C69.2, C72.2, L1.2, R52.2, R77.1, U12.18 (V_{OUT}), U50.1 (IN+)
5V_PHASE: C59.1, U12.24 (PHASE)
5V_SW: L1.1, U12.5 (SW), U12.6 (SW), U12.7 (SW), U12.8 (SW), U12.9 (SW)
5V_VDD: C52.2, R36.2, U12.15 (V_{DD})
5V_VDRV: C55.2, U12.12 (V_{DRV})
12V_BOOT: C221.2, U8.23 (BOOT)
12V_FB: R18.2, R326.1, U8.17 (FB)
12V_MODE1: R12.1, R13.2, U8.21 (MODE1)
12V_MODE2: R15.2, U8.20 (MODE2)
12V_OUT: C222.2, C235.2, L6.2, R22.1, R326.2, U8.18 (V_{OUT})
12V_PHASE: C221.1, U8.24 (PHASE)
12V_SW: L6.1, U8.5 (SW), U8.6 (SW), U8.7 (SW), U8.8 (SW), U8.9 (SW)
12V_VDD: C54.2, R12.2, U8.15 (V_{DD})
12V_VDRV: C218.2, U8.12 (V_{DRV})
16V_BOOT: C246.2, U11.23 (BOOT)
16V_EN: U11.19 (EN)
16V_FB: R69.1, R70.2, U11.17 (FB)
16V_MODE1: R20.2, R26.1, U11.21 (MODE1)
16V_MODE2: R41.2, U11.20 (MODE2)
16V_OUT: C247.2, C248.2, C249.2, C250.2, C257.2, C258.2, C259.2, C260.2, C282.2, C286.2, C290.2, C294.2, C298.2, C299.2, C300.2, L3.2, R65.1, R69.2, U11.18 (V_{OUT}), U22.1 (IN+)
16V_PHASE: C246.1, U11.24 (PHASE)
16V_SW: L3.1, U11.5 (SW), U11.6 (SW), U11.7 (SW), U11.8 (SW), U11.9 (SW)
16V_VDD: C244.2, R26.2, U11.15 (V_{DD})
16V_VDRV: C245.2, U11.12 (V_{DRV})
20V_BOOT: C281.2, U65.23 (BOOT)
20V_EN: R34.1, U65.19 (EN)
20V_FB: R94.1, R125.2, U65.17 (FB)
20V_MODE1: R23.1, R29.2, U65.21 (MODE1)
20V_MODE2: R30.2, U65.20 (MODE2)
20V_OUT: C283.2, C284.2, C285.2, C287.2, C288.2, C289.2, C291.2, C292.2, C293.2, C295.2, C296.2, C297.2, C301.2, C302.2, C303.2, L4.2, R94.2, R284.1, U65.18 (V_{OUT}), U66.1 (IN+)
20V_PHASE: C281.1, U65.24 (PHASE)
20V_SW: L4.1, U65.5 (SW), U65.6 (SW), U65.7 (SW), U65.8 (SW), U65.9 (SW)
20V_VDD: C279.2, R23.2, U65.15 (V_{DD})
20V_VDRV: C280.2, U65.12 (V_{DRV})
+1V8: C37.2, R10.2
+3V3: D9.1 (C), R61.2
+3V3_AON: C36.2, C197.2, C217.2, C304.2, U22.4 (V_{S}), U50.4 (V_{S}), U50.7 (A0), U60.4 (V_{S}), U66.4 (V_{S})
+5V: C31.2, C32.2, U7.1 (V_{IN})
+5V_AON: D8.1 (C), R60.2
+12V: D13.1 (C), R22.2
+20V: D56.1 (C), R305.2
BOARD_POWER_EN: U7.5 (EN), U8.19 (EN), U13.19 (EN)
GND: C28.1, C29.1, C31.1, C32.1, C33.1, C36.1, C37.1, C42.1, C43.1, C45.1, C46.1, C48.2, C49.2, C51.2, C52.1, C53.1, C54.1, C55.1, C56.1, C63.1, C64.1, C66.1, C67.1, C69.1, C70.1, C72.1, C73.1, C197.1, C217.1, C218.1, C222.1, C235.1, C241.1, C242.1, C243.2, C244.1, C245.1, C247.1, C248.1, C249.1, C250.1, C257.1, C258.1, C259.1, C260.1, C267.1, C268.1, C269.1, C270.1, C271.1, C273.1, C274.1, C275.1, C276.1, C277.1, C278.2, C279.1, C280.1, C282.1, C283.1, C284.1, C285.1, C286.1, C287.1, C288.1, C289.1, C290.1, C291.1, C292.1, C293.1, C294.1, C295.1, C296.1, C297.1, C298.1, C299.1, C300.1, C301.1, C302.1, C303.1, C304.1, C305.2, D7.2 (A), D8.2 (A), D9.2 (A), D13.2 (A), D56.2 (A), R13.1, R15.1, R18.1, R20.1, R29.1, R30.1, R37.1, R39.1, R41.1, R42.1, R43.1, R53.1, R55.1, R70.1, R125.1, R318.1, U7.3 (GND), U7.4 (AGND), U8.3 (P_{GND}), U8.4 (P_{GND}), U8.13 (P_{GND}), U8.16 (A_{GND}), U8.25 (A_{GND}), U8.27 (P_{GND}), U11.3 (P_{GND}), U11.4 (P_{GND}), U11.13 (P_{GND}), U11.16 (A_{GND}), U11.25 (A_{GND}), U11.27 (P_{GND}), U12.3 (P_{GND}), U12.4 (P_{GND}), U12.13 (P_{GND}), U12.16 (A_{GND}), U12.25 (A_{GND}), U12.27 (P_{GND}), U13.3 (P_{GND}), U13.4 (P_{GND}), U13.13 (P_{GND}), U13.16 (A_{GND}), U13.25 (A_{GND}), U13.27 (P_{GND}), U22.3 (GND), U22.7 (A0), U22.8 (A1), U50.3 (GND), U50.8 (A1), U60.3 (GND), U60.8 (A1), U65.3 (P_{GND}), U65.4 (P_{GND}), U65.13 (P_{GND}), U65.16 (A_{GND}), U65.25 (A_{GND}), U65.27 (P_{GND}), U66.3 (GND), U66.8 (A1)
I2C_{SYS}.SCL: U22.5 (SCL), U50.5 (SCL), U60.5 (SCL), U66.5 (SCL), U66.7 (A0)
I2C_{SYS}.SDA: U22.6 (SDA), U50.6 (SDA), U60.6 (SDA), U60.7 (A0), U66.6 (SDA)
unnamed: R50.1, R65.2, U22.2 (IN-)
unnamed: R60.1, R77.2, U50.2 (IN-)
unnamed: R61.1, R258.2, U60.2 (IN-)
unnamed: R284.2, R305.1, U66.2 (IN-)
unnamed: U8.10 (GL), U8.11 (GL), U8.28 (GL)
unnamed: U11.10 (GL), U11.11 (GL), U11.28 (GL)
unnamed: U12.10 (GL), U12.11 (GL), U12.28 (GL)
unnamed: U13.10 (GL), U13.11 (GL), U13.28 (GL)
unnamed: U65.10 (GL), U65.11 (GL), U65.28 (GL)
SYS_VIN_HV: D7.1 (C), R50.2
VCC: C28.2, C29.2, C42.2, C43.2, C45.2, C46.2, C48.1, C49.1, C51.1, C241.2, C242.2, C243.1, C267.2, C268.2, C270.2, C271.2, C273.2, C275.2, R24.2, U8.1 (V_{IN}), U8.2 (V_{IN}), U8.22 (V_{IN}), U8.26 (V_{IN}), U11.1 (V_{IN}), U11.2 (V_{IN}), U11.22 (V_{IN}), U11.26 (V_{IN}), U12.1 (V_{IN}), U12.2 (V_{IN}), U12.22 (V_{IN}), U12.26 (V_{IN}), U13.1 (V_{IN}), U13.2 (V_{IN}), U13.22 (V_{IN}), U13.26 (V_{IN})
VCC_IN: C269.2, C274.2, C276.2, C277.2, C278.1, R34.2, U65.1 (V_{IN}), U65.2 (V_{IN}), U65.22 (V_{IN}), U65.26 (V_{IN})
~VDDIN_PWR_BAD: U12.14 (P_{GOOD})

Notes on the sheet:
ADDR: 0x43
V_{OUT} = 0.6*(330k+10k)/10k = 20.4[V]
V_{EN(ON)} = 1.18V
+5V DC/DC converter
R_{FB_H} = (R_{FB_L}(V_{OUT}-0.6))/0.6
V_{OUT} = 0.6*(R_{FB_H}+R_{FB_L})/R_{FB_L}
ADDR: 0x41
+3V3 DC/DC converter
SoM High voltage DC/DC converter
1V8 @1.35A
V_{EN(ON)} = 1.6V
V_{OUT} = 0.6*(255k+10k)/10k = 15.9[V]
ADDR: 0x40
12V @2A
V_{OUT} = 0.6*(45k3+10k)/10k = 3.318[V]
ADDR: 0x42
3V3 @12A
V_{out} = 1.8 V f_{SW} = 1200 kHz I_{L} = 1.0 A ΔI_{L} = 71% I_{Lpeak} = 1.35 A
20V@10A
5V @12A
LO = ((VIN-VOUT)*D)/(ΔIL*fSW) LO = ((18V-12V)*(12V/18V))/(0.6A*1000kHz)=6.67uH
+20V DC/DC converter (USB PD)
16V@9.5A
+1V8 DC/DC converter
+12V DC/DC converter
