antmicro/jetson-agx-thor-baseboard/expansion_connector.kicad_sch

## KiCad design expansion_connector.kicad_sch (2026-03-19, an earlier design)

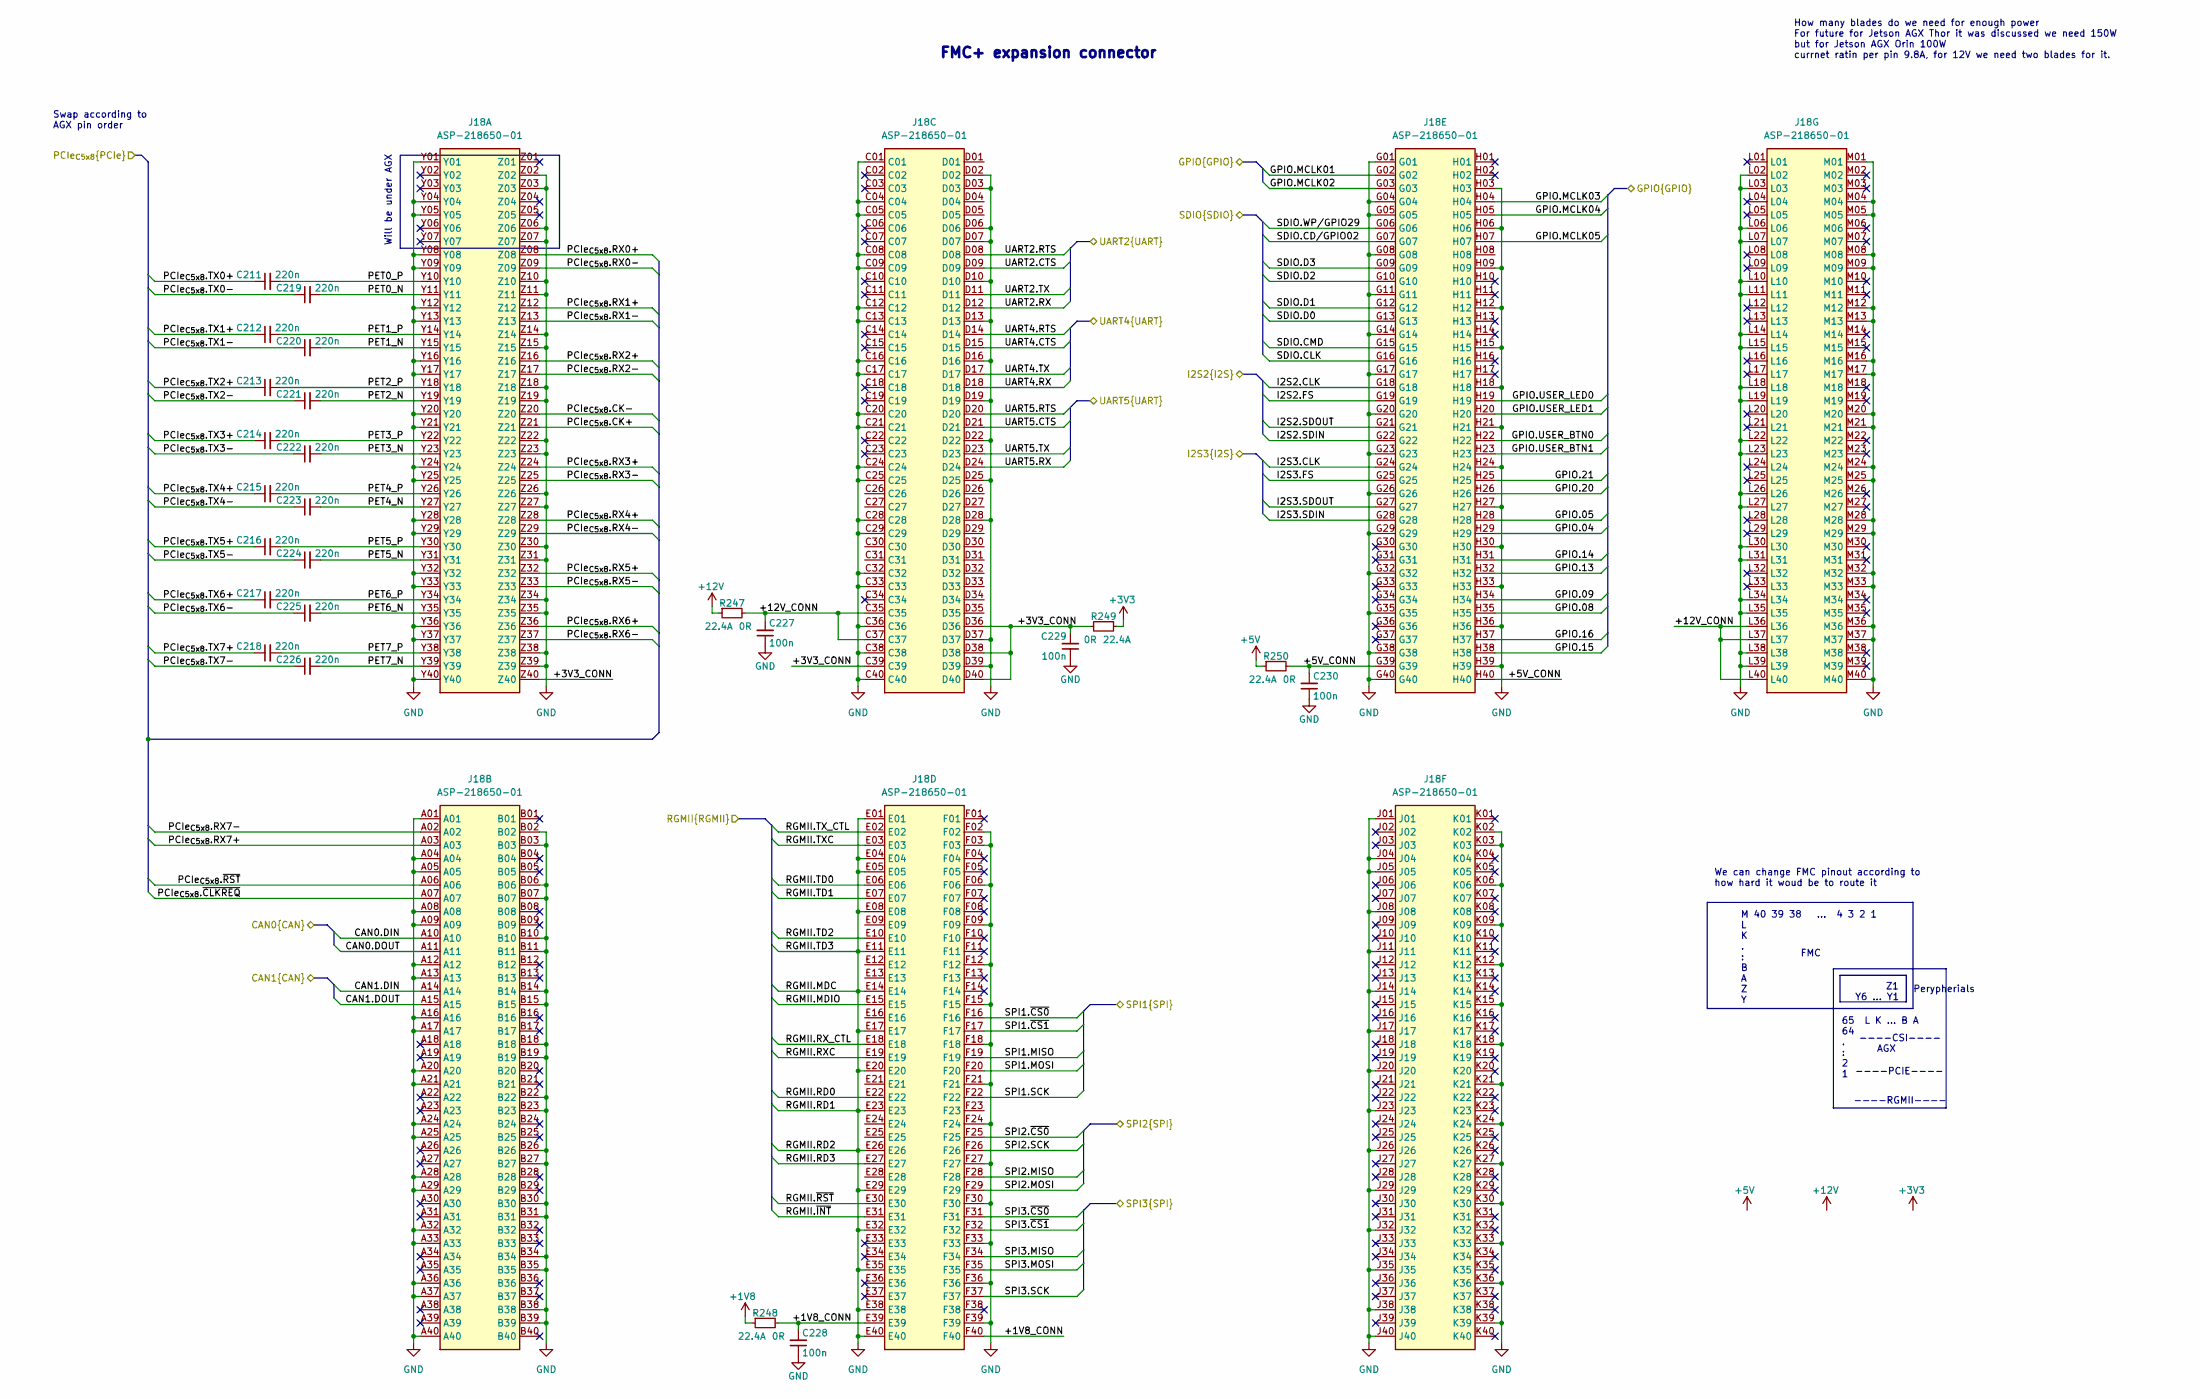
[picture p5: schematic expansion_connector.kicad_sch]

Parts:
C211, C212, C213, C214, C215, C216, C217, C218, C219, C220, C221, C222, C223, C224, C225, C226: C_220n_6V3_X7R_0402; C_0402_1005Metric; Voltage 6.3V; MPN C0402C224M9RACTU
C227, C228, C229, C230: C_100n_50V_X8L_0402; C_0402_1005Metric; Voltage 50V; MPN GCM155L8EH104KE07D
J18: ASP-218650-01_mounting_holes; MPN ASP-218650-01
R247, R248, R249, R250: R_0R_22.4A_0603; R_0603_1608Metric; Tolerance template_tolerance; MPN PMR03EZPJ000

Connections:
+1V8: R248.1
+1V8_CONN: C228.2, J18.E39, J18.F40, R248.2
+3V3: R249.1
+3V3_CONN: C229.2, J18.C39, J18.D36, J18.D38, J18.D40, J18.Z40, R249.2
+5V: R250.1
+5V_CONN: C230.2, J18.G39, J18.H40, R250.2
+12V: R247.1
+12V_CONN: C227.2, J18.C35, J18.C37, J18.L36, J18.L37, J18.L40, R247.2
CAN0.DIN: J18.A10
CAN0.DOUT: J18.A11
CAN1.DIN: J18.A14
CAN1.DOUT: J18.A15
GND: C227.1, C228.1, C229.1, C230.1, J18.A01, J18.A04, J18.A05, J18.A08, J18.A09, J18.A12, J18.A13, J18.A16, J18.A17, J18.A20, J18.A21, J18.A24, J18.A25, J18.A28, J18.A29, J18.A32, J18.A33, J18.A36, J18.A37, J18.A40, J18.B02, J18.B03, J18.B06, J18.B07, J18.B10, J18.B11, J18.B14, J18.B15, J18.B18, J18.B19, J18.B22, J18.B23, J18.B26, J18.B27, J18.B30, J18.B31, J18.B34, J18.B35, J18.B38, J18.B39, J18.C01, J18.C04, J18.C05, J18.C08, J18.C09, J18.C12, J18.C13, J18.C16, J18.C17, J18.C20, J18.C21, J18.C24, J18.C25, J18.C28, J18.C29, J18.C32, J18.C33, J18.C36, J18.C38, J18.C40, J18.D02, J18.D03, J18.D06, J18.D07, J18.D10, J18.D13, J18.D16, J18.D19, J18.D22, J18.D25, J18.D28, J18.D37, J18.D39, J18.E01, J18.E04, J18.E05, J18.E08, J18.E11, J18.E14, J18.E17, J18.E20, J18.E23, J18.E26, J18.E29, J18.E32, J18.E35, J18.E38, J18.E40, J18.F02, J18.F03, J18.F06, J18.F09, J18.F12, J18.F15, J18.F18, J18.F21, J18.F24, J18.F27, J18.F30, J18.F33, J18.F36, J18.F39, J18.G01, J18.G04, J18.G05, J18.G08, J18.G11, J18.G14, J18.G17, J18.G20, J18.G23, J18.G26, J18.G29, J18.G32, J18.G35, J18.G38, J18.G40, J18.H03, J18.H06, J18.H09, J18.H12, J18.H15, J18.H18, J18.H21, J18.H24, J18.H27, J18.H30, J18.H33, J18.H36, J18.H39, J18.J01, J18.J04, J18.J05, J18.J08, J18.J11, J18.J14, J18.J17, J18.J20, J18.J23, J18.J26, J18.J29, J18.J32, J18.J35, J18.J38, J18.J40, J18.K02, J18.K03, J18.K06, J18.K09, J18.K12, J18.K15, J18.K18, J18.K21, J18.K24, J18.K27, J18.K30, J18.K33, J18.K36, J18.K39, J18.L02, J18.L03, J18.L06, J18.L07, J18.L10, J18.L11, J18.L14, J18.L15, J18.L18, J18.L19, J18.L22, J18.L23, J18.L26, J18.L27, J18.L30, J18.L31, J18.L34, J18.L35, J18.L38, J18.L39, J18.M01, J18.M04, J18.M05, J18.M08, J18.M09, J18.M12, J18.M13, J18.M16, J18.M17, J18.M20, J18.M21, J18.M24, J18.M25, J18.M28, J18.M29, J18.M32, J18.M33, J18.M36, J18.M37, J18.M40, J18.Y01, J18.Y04, J18.Y05, J18.Y08, J18.Y09, J18.Y12, J18.Y13, J18.Y16, J18.Y17, J18.Y20, J18.Y21, J18.Y24, J18.Y25, J18.Y28, J18.Y29, J18.Y32, J18.Y33, J18.Y36, J18.Y37, J18.Y40, J18.Z02, J18.Z03, J18.Z06, J18.Z07, J18.Z10, J18.Z11, J18.Z14, J18.Z15, J18.Z18, J18.Z19, J18.Z22, J18.Z23, J18.Z26, J18.Z27, J18.Z30, J18.Z31, J18.Z34, J18.Z35, J18.Z38, J18.Z39
GPIO.04: J18.H29
GPIO.05: J18.H28
GPIO.08: J18.H35
GPIO.09: J18.H34
GPIO.13: J18.H32
GPIO.14: J18.H31
GPIO.15: J18.H38
GPIO.16: J18.H37
GPIO.20: J18.H26
GPIO.21: J18.H25
GPIO.MCLK01: J18.G02
GPIO.MCLK02: J18.G03
GPIO.MCLK03: J18.H04
GPIO.MCLK04: J18.H05
GPIO.MCLK05: J18.H07
GPIO.USER_BTN0: J18.H22
GPIO.USER_BTN1: J18.H23
GPIO.USER_LED0: J18.H19
GPIO.USER_LED1: J18.H20
I2S2.CLK: J18.G18
I2S2.FS: J18.G19
I2S2.SDIN: J18.G22
I2S2.SDOUT: J18.G21
I2S3.CLK: J18.G24
I2S3.FS: J18.G25
I2S3.SDIN: J18.G28
I2S3.SDOUT: J18.G27
PCIe_{C5x8}.CK+: J18.Z21
PCIe_{C5x8}.CK-: J18.Z20
PCIe_{C5x8}.RX0+: J18.Z08
PCIe_{C5x8}.RX0-: J18.Z09
PCIe_{C5x8}.RX1+: J18.Z12
PCIe_{C5x8}.RX1-: J18.Z13
PCIe_{C5x8}.RX2+: J18.Z16
PCIe_{C5x8}.RX2-: J18.Z17
PCIe_{C5x8}.RX3+: J18.Z24
PCIe_{C5x8}.RX3-: J18.Z25
PCIe_{C5x8}.RX4+: J18.Z28
PCIe_{C5x8}.RX4-: J18.Z29
PCIe_{C5x8}.RX5+: J18.Z32
PCIe_{C5x8}.RX5-: J18.Z33
PCIe_{C5x8}.RX6+: J18.Z36
PCIe_{C5x8}.RX6-: J18.Z37
PCIe_{C5x8}.RX7+: J18.A03
PCIe_{C5x8}.RX7-: J18.A02
PCIe_{C5x8}.TX0+: C211.1
PCIe_{C5x8}.TX0-: C219.1
PCIe_{C5x8}.TX1+: C212.1
PCIe_{C5x8}.TX1-: C220.1
PCIe_{C5x8}.TX2+: C213.1
PCIe_{C5x8}.TX2-: C221.1
PCIe_{C5x8}.TX3+: C214.1
PCIe_{C5x8}.TX3-: C222.1
PCIe_{C5x8}.TX4+: C215.1
PCIe_{C5x8}.TX4-: C223.1
PCIe_{C5x8}.TX5+: C216.1
PCIe_{C5x8}.TX5-: C224.1
PCIe_{C5x8}.TX6+: C217.1
PCIe_{C5x8}.TX6-: C225.1
PCIe_{C5x8}.TX7+: C218.1
PCIe_{C5x8}.TX7-: C226.1
PCIe_{C5x8}.~CLKREQ: J18.A07
PCIe_{C5x8}.~RST: J18.A06
PET0_N: C219.2, J18.Y11
PET0_P: C211.2, J18.Y10
PET1_N: C220.2, J18.Y15
PET1_P: C212.2, J18.Y14
PET2_N: C221.2, J18.Y19
PET2_P: C213.2, J18.Y18
PET3_N: C222.2, J18.Y23
PET3_P: C214.2, J18.Y22
PET4_N: C223.2, J18.Y27
PET4_P: C215.2, J18.Y26
PET5_N: C224.2, J18.Y31
PET5_P: C216.2, J18.Y30
PET6_N: C225.2, J18.Y35
PET6_P: C217.2, J18.Y34
PET7_N: C226.2, J18.Y39
PET7_P: C218.2, J18.Y38
RGMII.MDIO: J18.E15
RGMII.RD0: J18.E22
RGMII.RD3: J18.E27
RGMII.RXC: J18.E19
RGMII.RX_CTL: J18.E18
RGMII.TD0: J18.E06
RGMII.TD1: J18.E07
RGMII.TD2: J18.E10
RGMII.TXC: J18.E03
RGMII.TX_CTL: J18.E02
RGMII.~INT: J18.E31
RGMII.~RST: J18.E30
SDIO.CD/GPIO02: J18.G07
SDIO.CLK: J18.G16
SDIO.CMD: J18.G15
SDIO.D0: J18.G13
SDIO.D1: J18.G12
SDIO.D2: J18.G10
SDIO.D3: J18.G09
SDIO.WP/GPIO29: J18.G06
SPI1.MISO: J18.F19
SPI1.MOSI: J18.F20
SPI1.SCK: J18.F22
SPI1.~CS0: J18.F16
SPI1.~CS1: J18.F17
SPI2.MISO: J18.F28
SPI2.MOSI: J18.F29
SPI2.SCK: J18.F26
SPI2.~CS0: J18.F25
SPI3.MISO: J18.F34
SPI3.MOSI: J18.F35
SPI3.SCK: J18.F37
SPI3.~CS0: J18.F31
SPI3.~CS1: J18.F32
UART2.CTS: J18.D09
UART2.RTS: J18.D08
UART2.RX: J18.D12
UART2.TX: J18.D11
UART4.CTS: J18.D15
UART4.RTS: J18.D14
UART4.RX: J18.D18
UART4.TX: J18.D17
UART5.CTS: J18.D21
UART5.RTS: J18.D20
UART5.RX: J18.D24
UART5.TX: J18.D23

Notes on the sheet:
Will be under AGX
----PCIE----
AGX
65 L K ... B A 64 . : 2 1
FMC
----RGMII----
Z1 Y6 ... Y1
FMC+ expansion connector
We can change FMC pinout according to how hard it woud be to route it
How many blades do we need for enough power For future for Jetson AGX Thor it was discussed we need 150W but for Jetson AGX Orin 100W currnet ratin per pin 9.8A, for 12V we need two blades for it.
Perypherials
----CSI----
Swap according to AGX pin order
M 40 39 38 ... 4 3 2 1 L K . : B A Z Y
