antmicro/jetson-agx-thor-baseboard/jetson-agx-thor-baseboard.kicad_sch

## KiCad design jetson-agx-thor-baseboard.kicad_sch (2026-03-19, an earlier design)

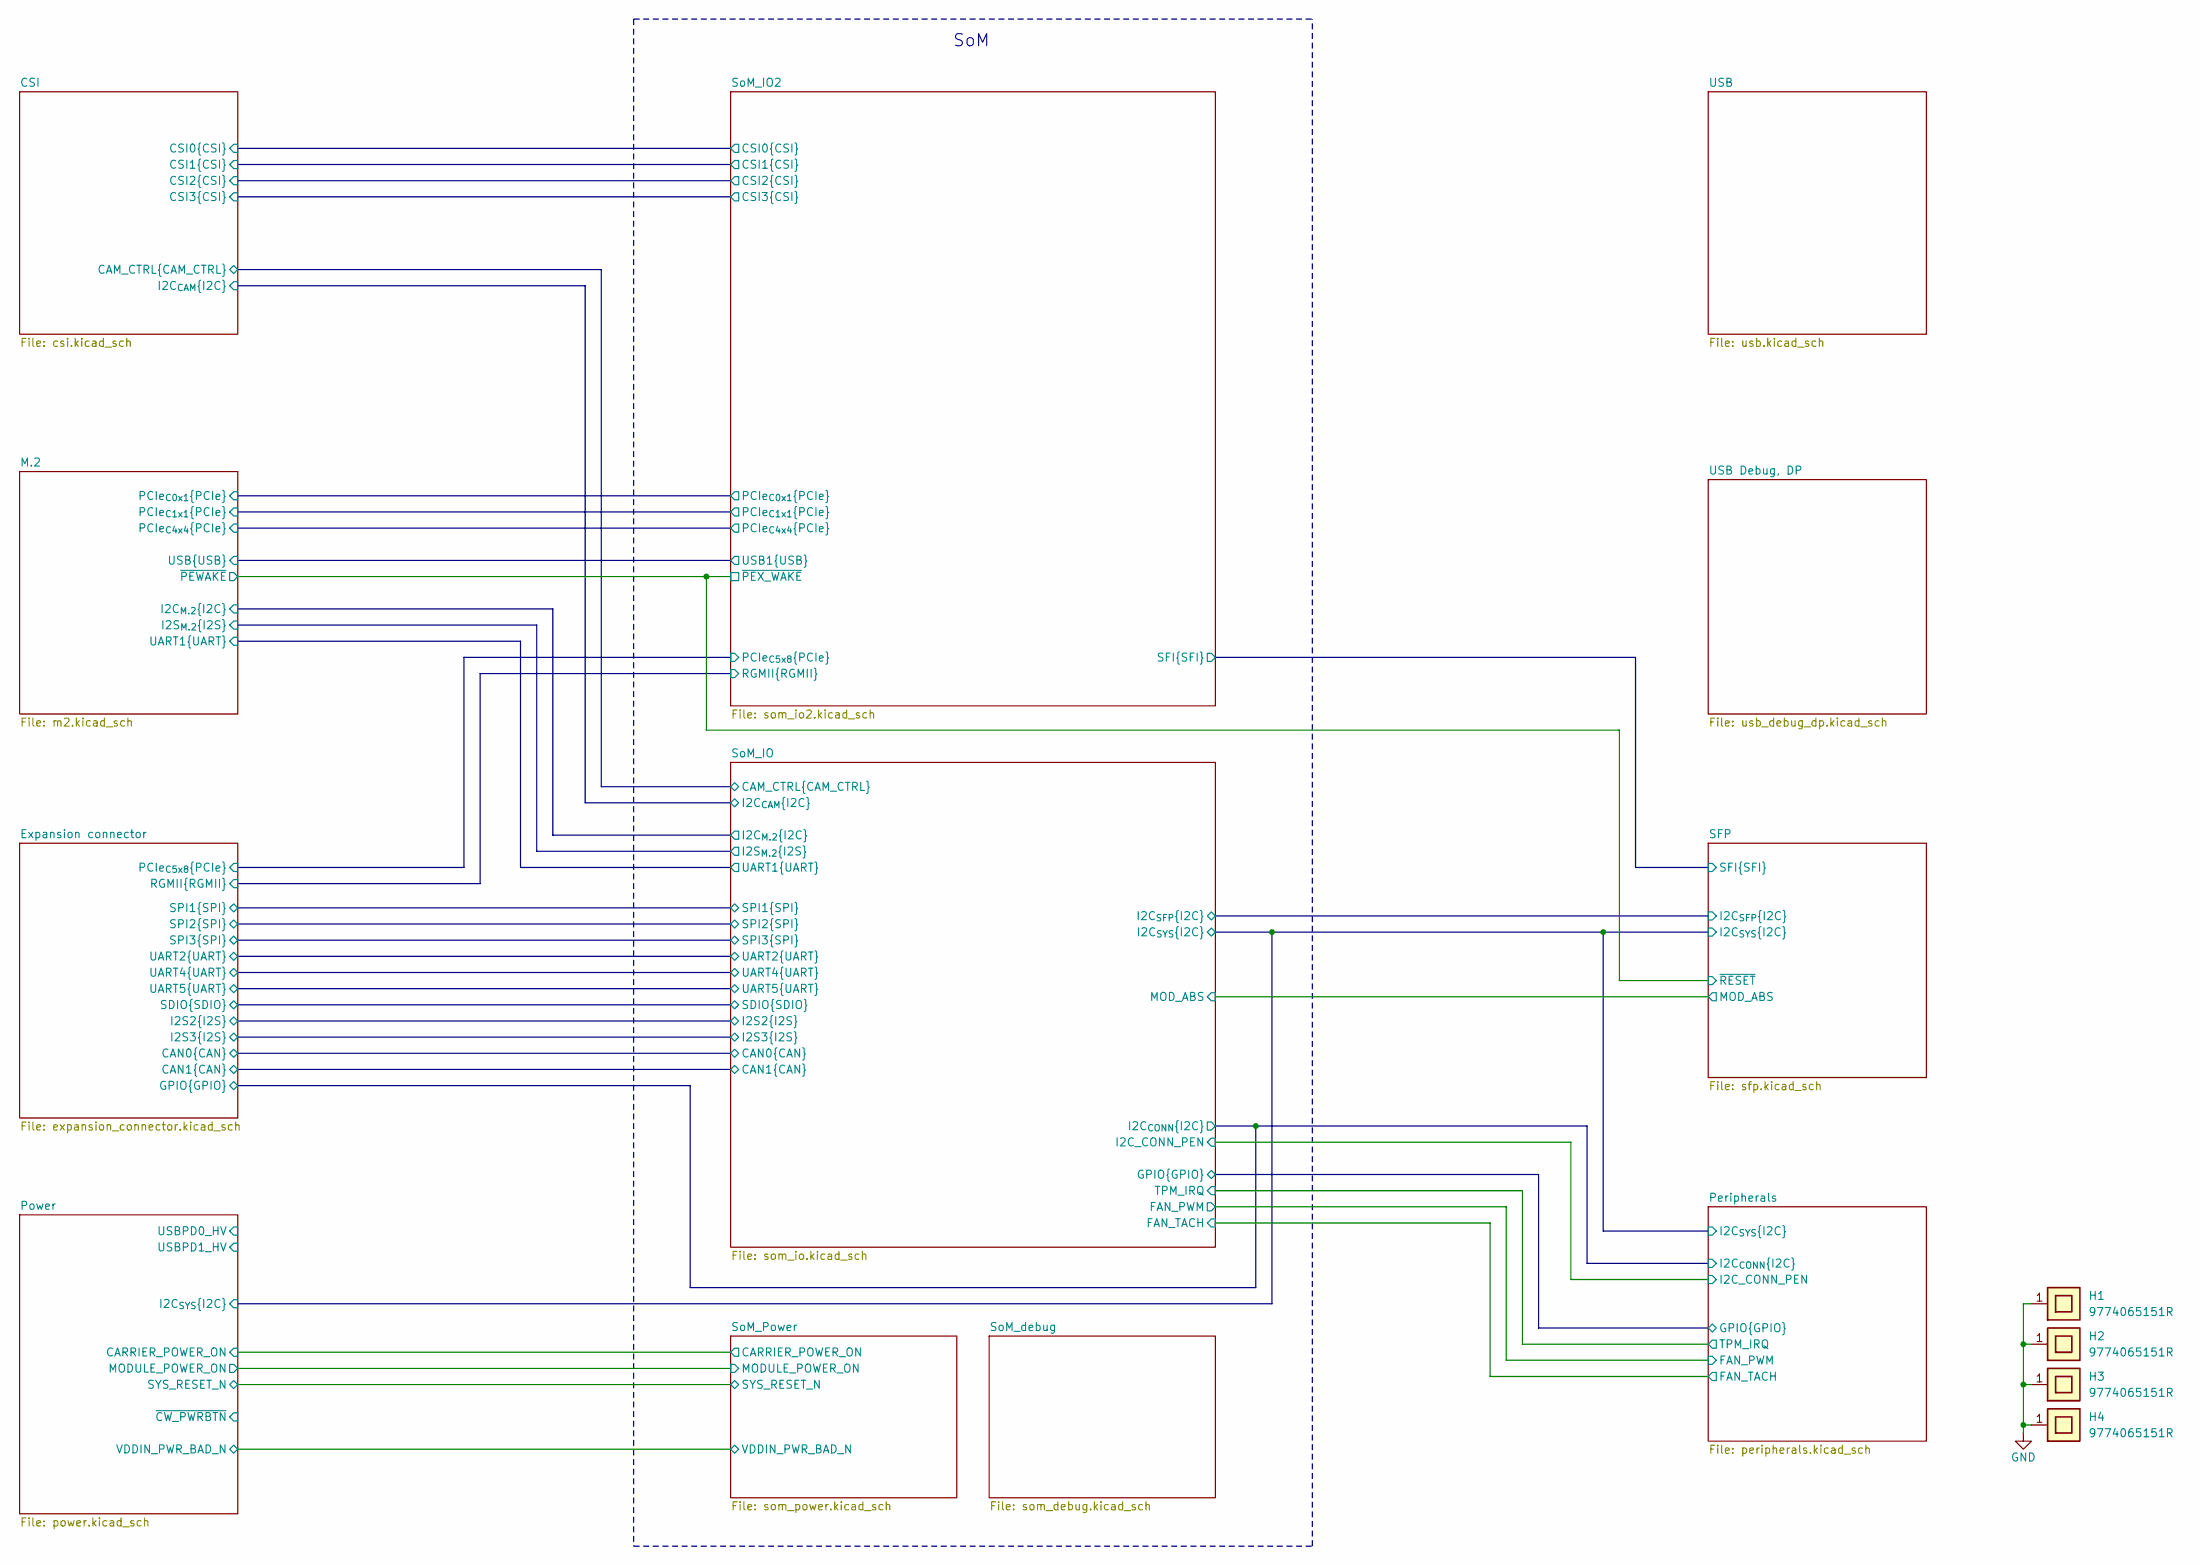
[picture p6: schematic jetson-agx-thor-baseboard.kicad_sch]

Parts:
H1, H2, H3, H4: Spacer_Drill3.7mm_H6.5mm_9774065151R; MPN 9774065151R

Connections:
GND: H1.1, H2.1, H3.1, H4.1

Notes on the sheet:
SoM
