antmicro/jetson-agx-thor-baseboard/m2.kicad_sch

## KiCad design m2.kicad_sch (2026-02-19, an earlier design)

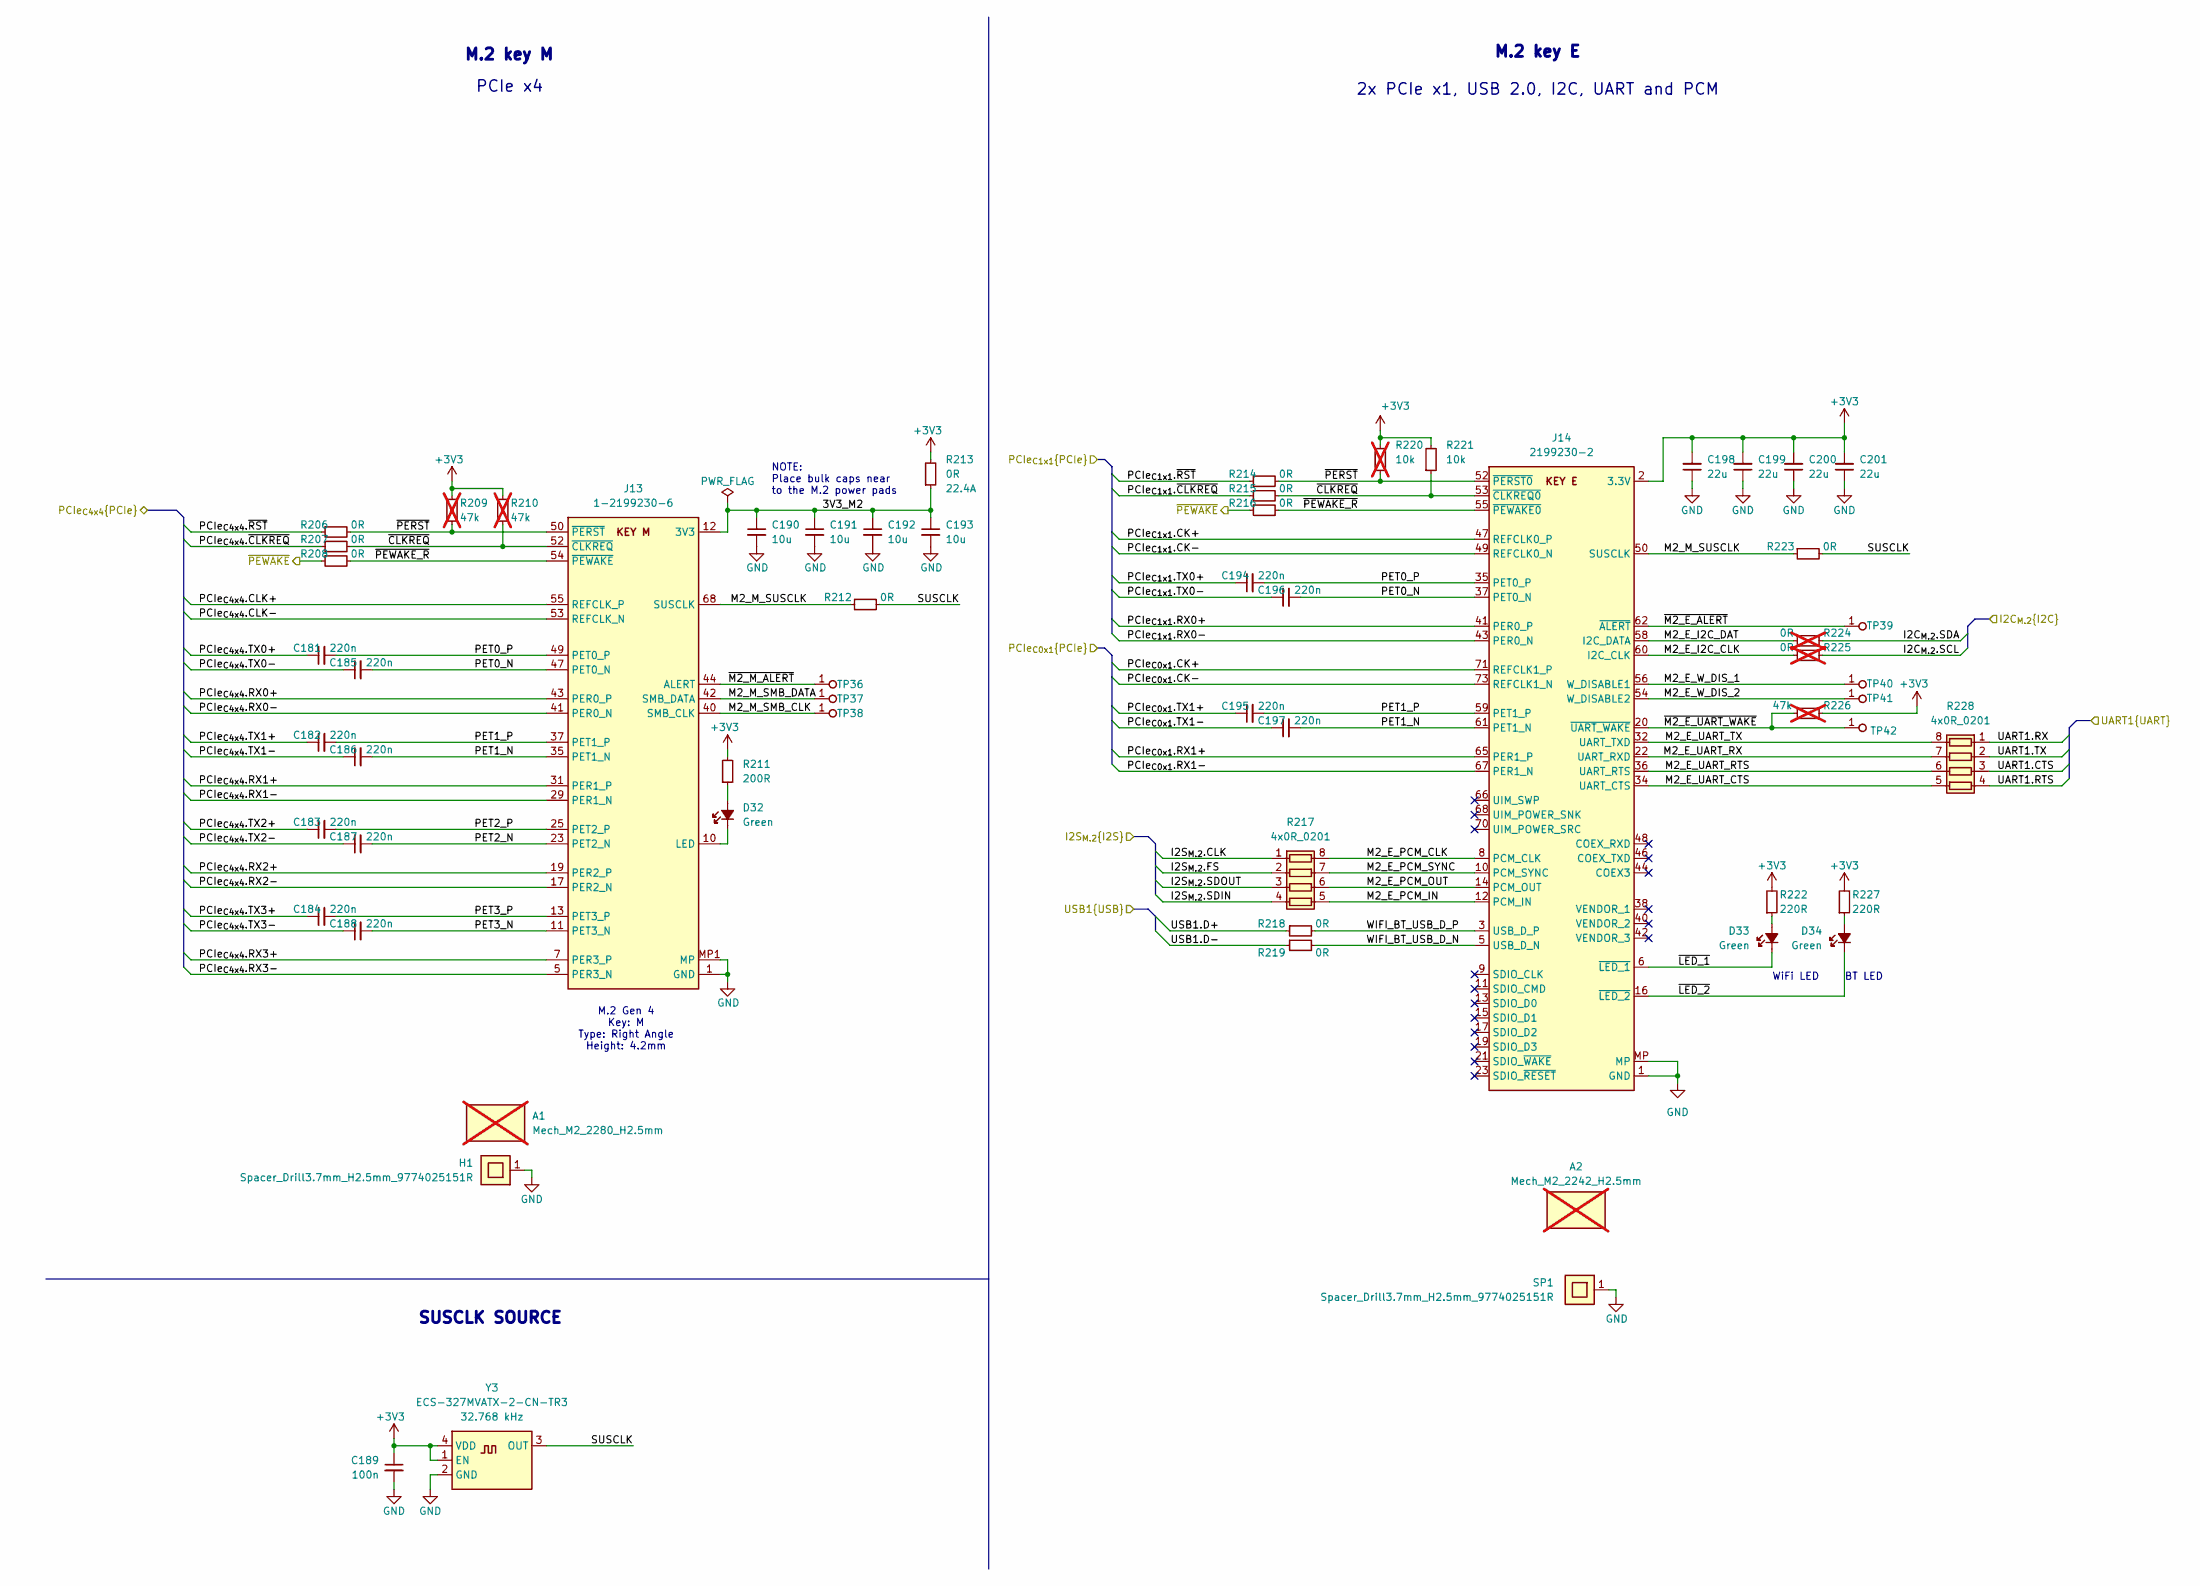
[picture p7: schematic m2.kicad_sch]

Parts:
A1: Mech_M2_2280_H2.5mm; not fitted
A2: Mech_M2_2242_H2.5mm; not fitted
C181, C182, C183, C184, C185, C186, C187, C188, C194, C195, C196, C197: C_220n_6V3_X7R_0402; C_0402_1005Metric; Voltage 6.3V; MPN C0402C224M9RACTU
C189: C_100n_0402; C_0402_1005Metric; Voltage 50V; MPN GRM155R61H104KE14D
C190, C191, C192, C193: C_10u_0603; C_0603_1608Metric; MPN GRM188R61A106KE69D
C198, C199, C200, C201: C_22u_16V_0603; C_0603_1608Metric; Voltage 16V; MPN CL10A226MO7JZNC
D32, D33, D34: LED_G_0603_LTST-C190GKT; LED_0603_1608Metric_G; MPN LTST-C190GKT
H1: Spacer_Drill3.7mm_H2.5mm_9774025151R; MPN 9774025151R
J13: Bus_M.2_1-2199230-6; Bus_M.2_Socket_Key_M_TE_1-2199230-6; MPN 1-2199230-6
J14: Bus_M.2_2199230-2; Bus_M.2_Socket_Key_E_TE_2199230-6; MPN 2199230-2
R206, R207, R208, R212, R214, R215, R216, R218, R219, R223: R_0R_0402; R_0402_1005Metric; MPN ERJ2GE0R00X
R209, R210, R226: R_47k_0402; R_0402_1005Metric; Tolerance 1%; MPN CR0402-FX-4702GLF; not fitted
R211: R_200R_0402; R_0402_1005Metric; Tolerance 1%; MPN CR0402-FX-2000GLF
R213: R_0R_22.4A_0603; R_0603_1608Metric; Tolerance template_tolerance; MPN PMR03EZPJ000
R217, R228: R_4x0R_0201_array; R_Array_4x0201_Panasonic_EXB18V; MPN EXB-18VR000X
R220: R_10k_0402; R_0402_1005Metric; Tolerance 1%; MPN CR0402-FX-1002GLF; not fitted
R221: R_10k_0402; R_0402_1005Metric; Tolerance 1%; MPN CR0402-FX-1002GLF
R222, R227: R_220R_0402; R_0402_1005Metric; Tolerance 1%; MPN CR0402-FX-2200GLF
R224, R225: R_0R_0402; R_0402_1005Metric; MPN ERJ2GE0R00X; not fitted
SP1: Spacer_Drill3.7mm_H2.5mm_9774025151R; MPN 9774025151R
TP36, TP37, TP38, TP39, TP40, TP41, TP42: TP_0.75mm_SMD; TP_SMD_0.75mm
Y3: Oscillator_32.768kHz_ECS_2520MV; Oscillator_SMD_ECS_2520MV_2.5x2mm; MPN ECS-327MVATX-2-CN-TR3

Connections:
3V3_M2: C190.1, C191.1, C192.1, C193.1, J13.2 (3V3), J13.4 (3V3), J13.12 (3V3), J13.14 (3V3), J13.16 (3V3), J13.18 (3V3), J13.70 (3V3), J13.72 (3V3), J13.74 (3V3), R213.1
+3V3: C189.1, C198.2, C199.2, C200.2, C201.2, J14.2 (3.3V), J14.4 (3.3V), J14.72 (3.3V), J14.74 (3.3V), R209.1, R210.1, R211.2, R213.2, R220.2, R221.2, R222.2, R226.2, R227.2, Y3.1 (EN), Y3.4 (VDD)
GND: C189.2, C190.2, C191.2, C192.2, C193.2, C198.1, C199.1, C200.1, C201.1, H1.1, J13.1 (GND), J13.3 (GND), J13.9 (GND), J13.15 (GND), J13.21 (GND), J13.27 (GND), J13.33 (GND), J13.39 (GND), J13.45 (GND), J13.51 (GND), J13.57 (GND), J13.71 (GND), J13.73 (GND), J13.75 (GND), J13.MP1 (MP), J13.MP2 (MP), J14.1 (GND), J14.7 (GND), J14.18 (GND), J14.33 (GND), J14.39 (GND), J14.45 (GND), J14.51 (GND), J14.57 (GND), J14.63 (GND), J14.69 (GND), J14.75 (GND), J14.MP, SP1.1, Y3.2 (GND)
I2C_{M.2}.SCL: R225.2
I2C_{M.2}.SDA: R224.2
I2S_{M.2}.CLK: R217.1 (R1.1)
I2S_{M.2}.FS: R217.2 (R2.1)
I2S_{M.2}.SDIN: R217.4 (R4.1)
I2S_{M.2}.SDOUT: R217.3 (R3.1)
M2_E_I2C_CLK: J14.60 (I2C_CLK), R225.1
M2_E_I2C_DAT: J14.58 (I2C_DATA), R224.1
M2_E_PCM_CLK: J14.8 (PCM_CLK), R217.8 (R1.2)
M2_E_PCM_IN: J14.12 (PCM_IN), R217.5 (R4.2)
M2_E_PCM_OUT: J14.14 (PCM_OUT), R217.6 (R3.2)
M2_E_PCM_SYNC: J14.10 (PCM_SYNC), R217.7 (R2.2)
M2_E_UART_CTS: J14.34 (UART_CTS), R228.5 (R4.2)
M2_E_UART_RTS: J14.36 (UART_RTS), R228.6 (R3.2)
M2_E_UART_RX: J14.22 (UART_RXD), R228.7 (R2.2)
M2_E_UART_TX: J14.32 (UART_TXD), R228.8 (R1.2)
M2_E_W_DIS_1: J14.56 (W_DISABLE1), TP40.1
M2_E_W_DIS_2: J14.54 (W_DISABLE2), TP41.1
M2_M_SMB_CLK: J13.40 (SMB_CLK), TP38.1
M2_M_SMB_DATA: J13.42 (SMB_DATA), TP37.1
M2_M_SUSCLK: J13.68 (SUSCLK), J14.50 (SUSCLK), R212.1, R223.1
unnamed: D32.1 (C), J13.10 (LED)
unnamed: D32.2 (A), R211.1
unnamed: D33.2 (A), R222.1
unnamed: D34.2 (A), R227.1
PCIe_{C0x1}.CK+: J14.71 (REFCLK1_P)
PCIe_{C0x1}.CK-: J14.73 (REFCLK1_N)
PCIe_{C0x1}.RX1+: J14.65 (PER1_P)
PCIe_{C0x1}.RX1-: J14.67 (PER1_N)
PCIe_{C0x1}.TX1+: C195.1
PCIe_{C0x1}.TX1-: C197.1
PCIe_{C1x1}.CK+: J14.47 (REFCLK0_P)
PCIe_{C1x1}.CK-: J14.49 (REFCLK0_N)
PCIe_{C1x1}.RX0+: J14.41 (PER0_P)
PCIe_{C1x1}.RX0-: J14.43 (PER0_N)
PCIe_{C1x1}.TX0+: C194.1
PCIe_{C1x1}.TX0-: C196.1
PCIe_{C1x1}.~CLKREQ: R215.1
PCIe_{C1x1}.~RST: R214.1
PCIe_{C4x4}.CLK+: J13.55 (REFCLK_P)
PCIe_{C4x4}.CLK-: J13.53 (REFCLK_N)
PCIe_{C4x4}.RX0+: J13.43 (PER0_P)
PCIe_{C4x4}.RX0-: J13.41 (PER0_N)
PCIe_{C4x4}.RX1+: J13.31 (PER1_P)
PCIe_{C4x4}.RX1-: J13.29 (PER1_N)
PCIe_{C4x4}.RX2+: J13.19 (PER2_P)
PCIe_{C4x4}.RX2-: J13.17 (PER2_N)
PCIe_{C4x4}.RX3+: J13.7 (PER3_P)
PCIe_{C4x4}.RX3-: J13.5 (PER3_N)
PCIe_{C4x4}.TX0+: C181.1
PCIe_{C4x4}.TX0-: C185.1
PCIe_{C4x4}.TX1+: C182.1
PCIe_{C4x4}.TX1-: C186.1
PCIe_{C4x4}.TX2+: C183.1
PCIe_{C4x4}.TX2-: C187.1
PCIe_{C4x4}.TX3+: C184.1
PCIe_{C4x4}.TX3-: C188.1
PCIe_{C4x4}.~CLKREQ: R207.1
PCIe_{C4x4}.~RST: R206.1
PET0_N: C185.2, C196.2, J13.47 (PET0_N), J14.37 (PET0_N)
PET0_P: C181.2, C194.2, J13.49 (PET0_P), J14.35 (PET0_P)
PET1_N: C186.2, C197.2, J13.35 (PET1_N), J14.61 (PET1_N)
PET1_P: C182.2, C195.2, J13.37 (PET1_P), J14.59 (PET1_P)
PET2_N: C187.2, J13.23 (PET2_N)
PET2_P: C183.2, J13.25 (PET2_P)
PET3_N: C188.2, J13.11 (PET3_N)
PET3_P: C184.2, J13.13 (PET3_P)
SUSCLK: R212.2, R223.2, Y3.3 (OUT)
UART1.CTS: R228.3 (R3.1)
UART1.RTS: R228.4 (R4.1)
UART1.RX: R228.1 (R1.1)
UART1.TX: R228.2 (R2.1)
USB1.D+: R218.1
USB1.D-: R219.1
WIFI_BT_USB_D_N: J14.5 (USB_D_N), R219.2
WIFI_BT_USB_D_P: J14.3 (USB_D_P), R218.2
~CLKREQ: J13.52 (~CLKREQ), J14.53 (~CLKREQ0), R207.2, R210.2, R215.2, R221.1
~LED_1: D33.1 (C), J14.6 (~LED_1)
~LED_2: D34.1 (C), J14.16 (~LED_2)
~M2_E_ALERT: J14.62 (~ALERT), TP39.1
~M2_E_UART_WAKE: J14.20 (~UART_WAKE), R226.1, TP42.1
~M2_M_ALERT: J13.44 (ALERT), TP36.1
~PERST: J13.50 (~PERST), J14.52 (~PERST0), R206.2, R209.2, R214.2, R220.1
~PEWAKE_R: J13.54 (~PEWAKE), J14.55 (~PEWAKE0), R208.2, R216.2
~PEWAKE: R208.1, R216.1

Notes on the sheet:
M.2 key E
M.2 key M
NOTE: Place bulk caps near to the M.2 power pads
2x PCIe x1, USB 2.0, I2C, UART and PCM
SUSCLK SOURCE
M.2 Gen 4 Key: M Type: Right Angle Height: 4.2mm
WiFi LED
BT LED
PCIe x4
