antmicro/jetson-agx-thor-baseboard/peripherals.kicad_sch

## KiCad design peripherals.kicad_sch (2026-03-19, an earlier design)

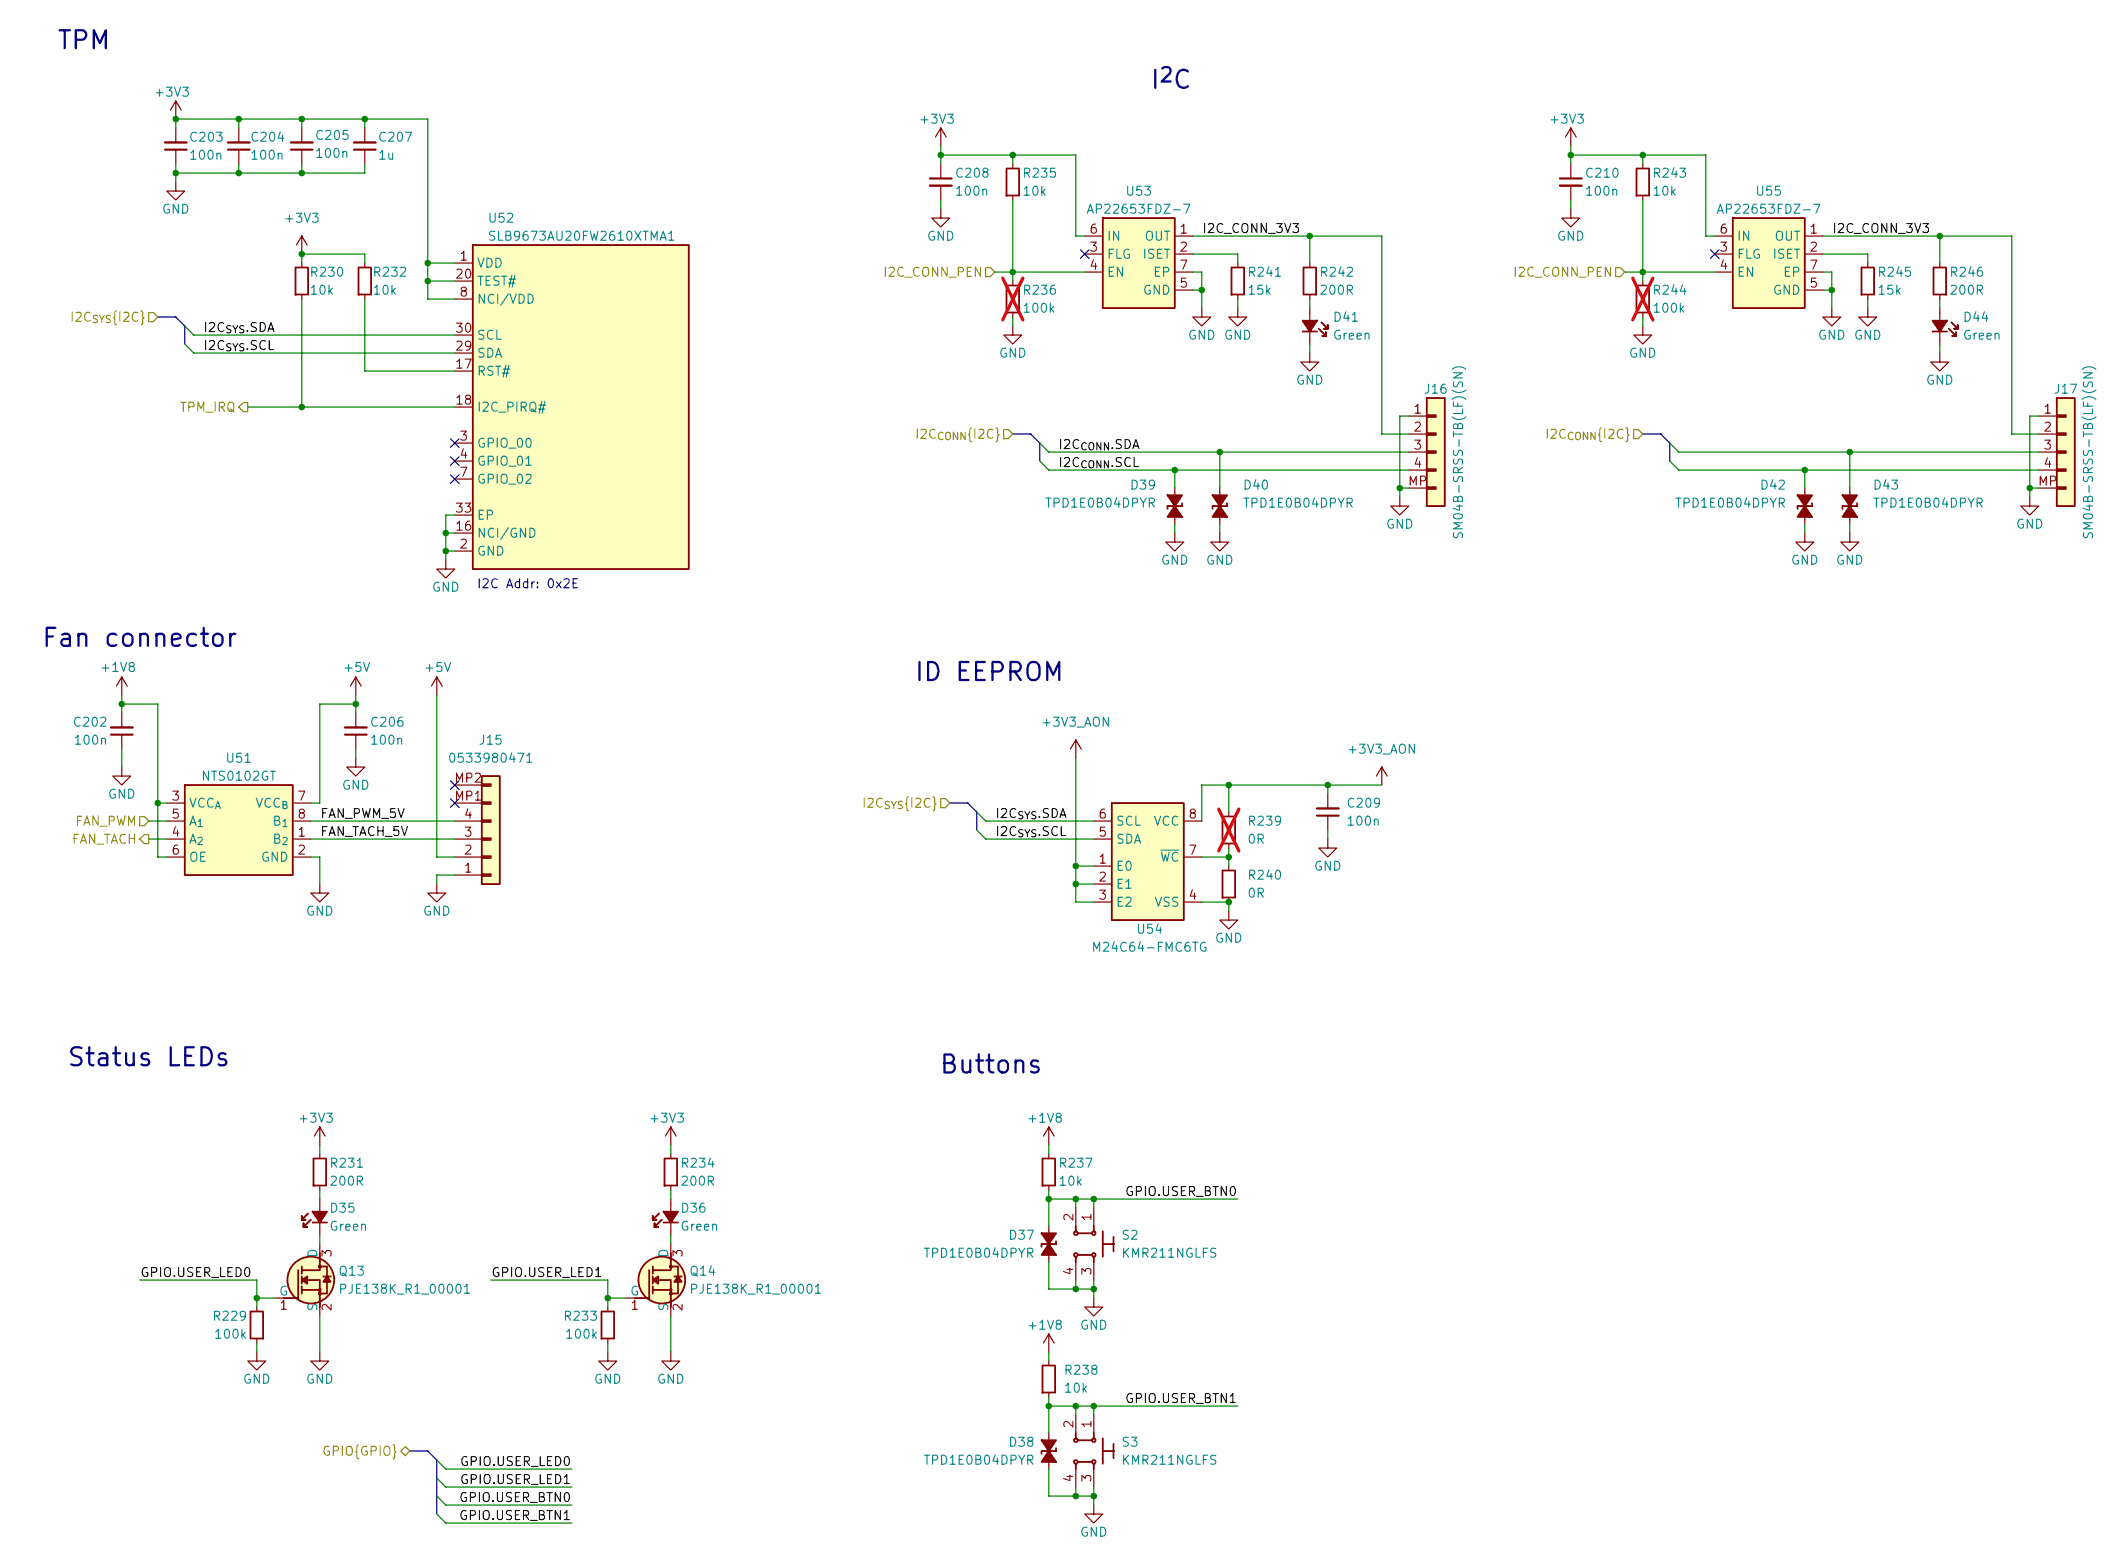
[picture p8: schematic peripherals.kicad_sch]

Parts:
C202, C206, C208, C209, C210: C_100n_0402; C_0402_1005Metric; Voltage 50V; MPN GRM155R61H104KE14D
C203, C204, C205: C_100n_16V_X7R_0402; C_0402_1005Metric; Voltage 16V; MPN C0402C104J4RAC7411
C207: C_1u_16V_0402; C_0402_1005Metric; Voltage 16V; MPN C0402C105M4PACTU
D35, D36, D41, D44: LED_G_0603_LTST-C190GKT; LED_0603_1608Metric_G; MPN LTST-C190GKT
D37, D38, D39, D40, D42, D43: TPD1E0B04_XDFN-2; XDFN-2_1x0.60mm; MPN TPD1E0B04DPYR
J15: Molex_PicoBlade_1x4_0533980471; Conn_Molex_PicoBlade_1x4_0533980471; MPN 0533980471
J16, J17: JST_SH_1x4_SM04B-SRSS-TB-LF-SN; Conn_JST_SH_1x4_SM04B-SRSS-TB-LF-SN; MPN SM04B-SRSS-TB(LF)(SN)
Q13, Q14: PJE138K; SOT-523; MPN PJE138K_R1_00001
R229, R233: R_100k_0402; R_0402_1005Metric; Tolerance 1%; MPN CR0402-FX-1003GLF
R230, R232, R235, R237, R238, R243: R_10k_0402; R_0402_1005Metric; Tolerance 1%; MPN CR0402-FX-1002GLF
R231, R234, R242, R246: R_200R_0402; R_0402_1005Metric; Tolerance 1%; MPN CR0402-FX-2000GLF
R236, R244: R_100k_0402; R_0402_1005Metric; Tolerance 1%; MPN CR0402-FX-1003GLF; not fitted
R239: R_0R_0402; R_0402_1005Metric; MPN ERJ2GE0R00X; not fitted
R240: R_0R_0402; R_0402_1005Metric; MPN ERJ2GE0R00X
R241, R245: R_15k_0402; R_0402_1005Metric; Tolerance 1%; MPN CR0402-FX-1502GLF
S2, S3: SW_KMR211NGLFS_SMD; MPN KMR211NGLFS
U51: NTS0102_XSON; XSON-8_1x1.95mm_P0.5mm; MPN NTS0102GT
U52: SLB9673AU20FW2610XTMA1; QFN-32-1EP_5x5mm; MPN SLB9673AU20FW2610XTMA1
U53, U55: AP22653_DFN; DFN-6-1EP_2x2mm_P0.65mm_EP1x1.6mm; MPN AP22653FDZ-7
U54: M24C64-F_DFN8; DFN-8-1EP_3x2mm_P0.5mm_EP1.36x1.46mm; MPN M24C64-FMC6TG

Connections:
+1V8: C202.2, R237.2, R238.2, U51.3 (VCC_{A}), U51.6 (OE)
+3V3: C203.2, C204.2, C205.2, C207.2, C208.1, C210.1, R230.2, R231.2, R232.2, R234.2, R235.2, R243.2, U52.1 (VDD), U52.8 (NCI/VDD), U52.14 (VDD), U52.20 (TEST#), U52.22 (VDD), U53.6 (IN), U55.6 (IN)
+3V3_AON: C209.2, R239.2, U54.1 (E0), U54.2 (E1), U54.3 (E2), U54.8 (VCC)
+5V: C206.2, J15.2, U51.7 (VCC_{B})
FAN_PWM: U51.5 (A_{1})
FAN_PWM_5V: J15.4, U51.8 (B_{1})
FAN_TACH: U51.4 (A_{2})
FAN_TACH_5V: J15.3, U51.1 (B_{2})
GND: C202.1, C203.1, C204.1, C205.1, C206.1, C207.1, C208.2, C209.1, C210.2, D37.1 (C), D38.1 (C), D39.1 (C), D40.1 (C), D41.1 (C), D42.1 (C), D43.1 (C), D44.1 (C), J15.1, J16.1, J16.MP, J17.1, J17.MP, Q13.2 (S), Q14.2 (S), R229.1, R233.1, R236.1, R240.1, R241.1, R244.1, R245.1, S2.3, S2.4, S3.3, S3.4, U51.2 (GND), U52.2 (GND), U52.9 (GND), U52.16 (NCI/GND), U52.23 (GND), U52.32 (GND), U52.33 (EP), U53.5 (GND), U53.7 (EP), U54.4 (VSS), U54.9 (VSS), U55.5 (GND), U55.7 (EP)
GPIO.USER_BTN0: D37.2 (A), R237.1, S2.1, S2.2
GPIO.USER_BTN1: D38.2 (A), R238.1, S3.1, S3.2
GPIO.USER_LED0: Q13.1 (G), R229.2
GPIO.USER_LED1: Q14.1 (G), R233.2
I2C_CONN_3V3: J16.2, J17.2, R242.2, R246.2, U53.1 (OUT), U55.1 (OUT)
I2C_CONN_PEN: R235.1, R236.2, R243.1, R244.2, U53.4 (EN), U55.4 (EN)
I2C_{CONN}.SCL: D39.2 (A), J16.4
I2C_{CONN}.SDA: D40.2 (A), J16.3
I2C_{SYS}.SCL: U52.29 (SDA), U54.5 (SDA)
I2C_{SYS}.SDA: U52.30 (SCL), U54.6 (SCL)
unnamed: D35.1 (C), Q13.3 (D)
unnamed: D35.2 (A), R231.1
unnamed: D36.1 (C), Q14.3 (D)
unnamed: D36.2 (A), R234.1
unnamed: D41.2 (A), R242.1
unnamed: D42.2 (A), J17.4
unnamed: D43.2 (A), J17.3
unnamed: D44.2 (A), R246.1
unnamed: R232.1, U52.17 (RST#)
unnamed: R239.1, R240.2, U54.7 (~WC)
unnamed: R241.2, U53.2 (ISET)
unnamed: R245.2, U55.2 (ISET)
TPM_IRQ: R230.1, U52.18 (I2C_PIRQ#)

Notes on the sheet:
Buttons
I2C Addr: 0x2E
Fan connector
ID EEPROM
I^{2}C
TPM
Status LEDs
