antmicro/jetson-agx-thor-baseboard/power.kicad_sch

## KiCad design power.kicad_sch (2026-03-19, an earlier design)

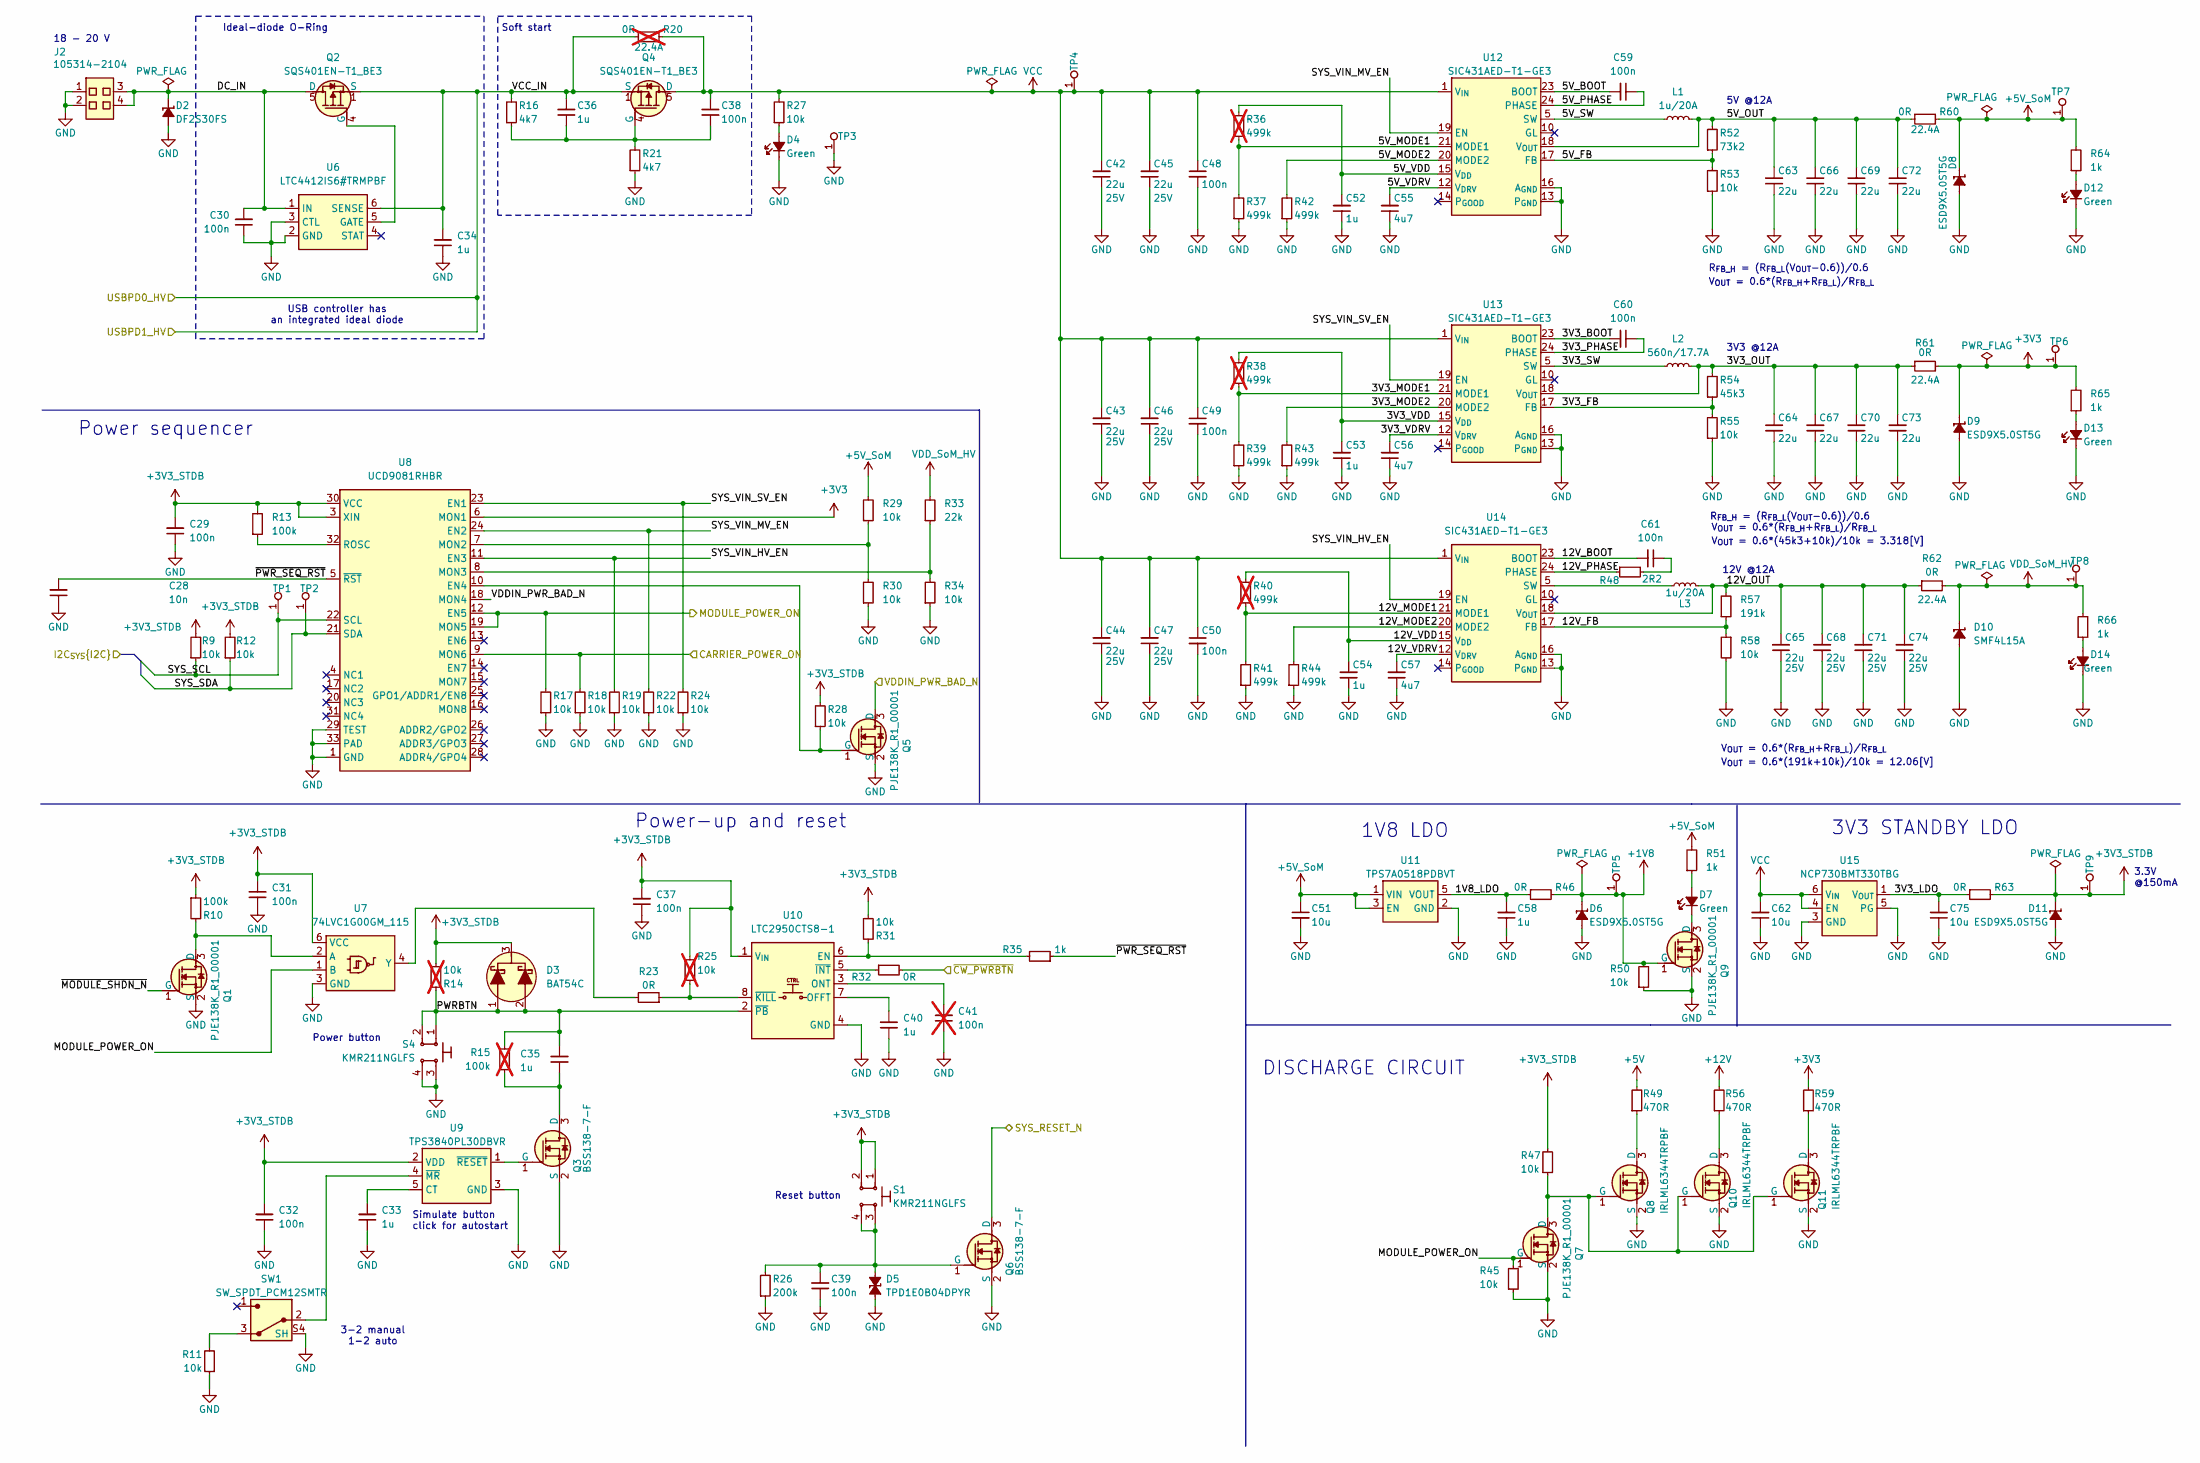
[picture p9: schematic power.kicad_sch]

Parts:
C28: C_10n_0603; C_0603_1608Metric; MPN 06031C103JAT2A
C29, C61: C_100n_16V_X7R_0402; C_0402_1005Metric; Voltage 16V; MPN C0402C104J4RAC7411
C30: C_100n_50V_X8L_0402; C_0402_1005Metric; Voltage 50V; MPN GCM155L8EH104KE07D
C31, C32, C37, C38, C39, C48, C49, C50, C59, C60: C_100n_0402; C_0402_1005Metric; Voltage 50V; MPN GRM155R61H104KE14D
C33, C34, C35, C36: C_1u_25V_0402; C_0402_1005Metric; Voltage 25V; MPN GRM155R61E105KE11J
C40, C52, C53, C54, C58: C_1u_0402; C_0402_1005Metric; MPN C1005X6S1A105K050BC
C41: C_100n_0402; C_0402_1005Metric; Voltage 50V; MPN GRM155R61H104KE14D; not fitted
C42, C43, C44, C45, C46, C47, C65, C68, C71, C74: C_22u_25V_0805; C_0805_2012Metric; Voltage 25V; MPN CL21A226MAYNNNE
C51, C75: C_10u_0402; C_0402_1005Metric; MPN CC0402MRX5R5BB106
C55, C56, C57: C_4u7_25V_0402; C_0402_1005Metric; Voltage 25V; MPN GRM155C61E475ME15J
C62: C_10u_25V_0603; C_0603_1608Metric; Voltage 25V; MPN C1608X5R1E106M080AC
C63, C64, C66, C67, C69, C70, C72, C73: C_22u_16V_0603; C_0603_1608Metric_EIA; Voltage 16V; MPN CL10A226MO7JZNC
D2: DF2S30FS_SOD; SOD-923; MPN DF2S30FS
D3: BAT54C; SOT-23-3; MPN BAT54C
D4, D7, D12, D13, D14: LED_G_0603_LTST-C190GKT; LED_0603_1608Metric_G; MPN LTST-C190GKT
D5: TPD1E0B04_XDFN-2; XDFN-2_1x0.60mm; MPN TPD1E0B04DPYR
D6, D8, D9, D11: ESD9X5.0ST5G; SOD-923; MPN ESD9X5.0ST5G
D10: SMF4L15A; SOD-123FL; MPN SMF4L15A
J2: Molex_Nano-Fit_2x2_105314-2104_Horizontal; Conn_Molex_Nano-Fit_2x2_105314-2104_Horizontal; MPN 105314-2104
L1, L3: L_1u_20A_Bourns-SRP6050CA; L_Bourns-SRP6050CA; MPN SRP6050CA-1R0M
L2: L_560n_17.7A_Bourns-SRP5030CA; L_Bourns-SRP5030CA; MPN SRP5030CA-R56M
Q1, Q5, Q7, Q9: PJE138K; SOT-523; MPN PJE138K_R1_00001
Q2, Q4: SQS401EN-T1_BE3; Vishay_PowerPAK_1212-8_Single; MPN SQS401EN-T1_BE3
Q3, Q6: BSS138-7-F; SOT-23-3; MPN BSS138-7-F
Q8, Q10, Q11: IRLML6344TRPBF; SOT-23-3; MPN IRLML6344TRPBF
R9, R10, R11, R12, R17, R18, R19, R22, R24, R27, R28, R29, R30, R31, R34, R45, R47, R50, R53, R55, R58: R_10k_0402; R_0402_1005Metric; Tolerance 1%; MPN CR0402-FX-1002GLF
R13: R_100k_0402; R_0402_1005Metric; Tolerance 1%; MPN CR0402-FX-1003GLF
R14, R25: R_10k_0402; R_0402_1005Metric; Tolerance 1%; MPN CR0402-FX-1002GLF; not fitted
R15: R_100k_0402; R_0402_1005Metric; Tolerance 1%; MPN CR0402-FX-1003GLF; not fitted
R16, R21: R_4k7_0402; R_0402_1005Metric; Tolerance 1%; MPN CR0402-FX-4701GLF
R20: R_0R_22.4A_0603; R_0603_1608Metric; Tolerance template_tolerance; MPN PMR03EZPJ000; not fitted
R23, R32: R_0R_0402; R_0402_1005Metric; MPN ERJ2GE0R00X
R26: R_200k_0402; R_0402_1005Metric; Tolerance 1%; MPN CR0402-FX-2003GLF
R33: R_22k_0402; R_0402_1005Metric; Tolerance 1%; MPN CR0402-FX-2202GLF
R35, R51, R64, R65, R66: R_1k_0402; R_0402_1005Metric; Tolerance 1%; MPN CR0402-FX-1001GLF
R36, R38, R40: R_499k_0402; R_0402_1005Metric; Tolerance 1%; MPN CR0402-FX-4993GLF; not fitted
R37, R39, R41, R42, R43, R44: R_499k_0402; R_0402_1005Metric; Tolerance 1%; MPN CR0402-FX-4993GLF
R46, R63: R_0R_0603; R_0603_1608Metric; MPN CR0603-J/-000ELF
R48: R_2R2_0402; R_0402_1005Metric; Tolerance 1%; MPN CR0402-FX-2R20GLF
R49, R56, R59: R_470R_0402; R_0402_1005Metric; Tolerance 1%; MPN CR0402-FX-4700GLF
R52: R_73k2_0402; R_0402_1005Metric; Tolerance 1%; MPN CR0402-FX-7322GLF
R54: R_45k3_0402; R_0402_1005Metric; Tolerance 1%; MPN CR0402-FX-4532GLF
R57: R_191k_0402; R_0402_1005Metric; Tolerance 1%; MPN CR0402-FX-1913GLF
R60, R61, R62: R_0R_22.4A_0603; R_0603_1608Metric; Tolerance template_tolerance; MPN PMR03EZPJ000
S1, S4: SW_KMR211NGLFS_SMD; MPN KMR211NGLFS
SW1: SW_SPDT_PCM12SMTR; PCM12SMTR; MPN PCM12SMTR
TP1, TP2, TP3, TP4, TP5, TP6, TP7, TP8, TP9: TP_0.75mm_SMD; TP_SMD_0.75mm
U6: LTC4412IS6; SOT-23-6; MPN LTC4412IS6#TRMPBF
U7: 74LVC1G00GM_115; XSON-6_1x1.45mm_P0.5mm; MPN 74LVC1G00GM_115
U8: UCD9081; HVQFN-32-1EP_5x5mm_P0.5mm_EP3.6x3.6mm; MPN UCD9081RHBR
U9: TPS3840PL30DBVR; SOT-23-5; MPN TPS3840PL30DBVR
U10: LTC2950CTS8-1; SOT-23-8; MPN LTC2950CTS8-1
U11: TPS7A0518P_SOT23-5; SOT-23-5; MPN TPS7A0518PDBVT
U12, U13, U14: SIC431AED-T1-GE3; MLP44-24L_4x4x0.75mm; MPN SIC431AED-T1-GE3
U15: NCP730BMT330_WSON; WSON-6-1EP_2x2mm_P0.65mm; MPN NCP730BMT330TBG

Connections:
1V8_LDO: C58.2, R46.1, U11.5 (VOUT)
3V3_BOOT: C60.2, U13.23 (BOOT)
3V3_FB: R54.1, R55.2, U13.17 (FB)
3V3_LDO: C75.2, R63.1, U15.1 (V_{OUT})
3V3_MODE1: R38.1, R39.2, U13.21 (MODE1)
3V3_MODE2: R43.2, U13.20 (MODE2)
3V3_OUT: C64.2, C67.2, C70.2, C73.2, L2.2, R54.2, R61.1, U13.18 (V_{OUT})
3V3_PHASE: C60.1, U13.24 (PHASE)
3V3_SW: L2.1, U13.5 (SW), U13.6 (SW), U13.7 (SW), U13.8 (SW), U13.9 (SW)
3V3_VDD: C53.2, R38.2, U13.15 (V_{DD})
3V3_VDRV: C56.2, U13.12 (V_{DRV})
5V_BOOT: C59.2, U12.23 (BOOT)
5V_FB: R52.1, R53.2, U12.17 (FB)
5V_MODE1: R36.1, R37.2, U12.21 (MODE1)
5V_MODE2: R42.2, U12.20 (MODE2)
5V_OUT: C63.2, C66.2, C69.2, C72.2, L1.2, R52.2, R60.1, U12.18 (V_{OUT})
5V_PHASE: C59.1, U12.24 (PHASE)
5V_SW: L1.1, U12.5 (SW), U12.6 (SW), U12.7 (SW), U12.8 (SW), U12.9 (SW)
5V_VDD: C52.2, R36.2, U12.15 (V_{DD})
5V_VDRV: C55.2, U12.12 (V_{DRV})
12V_BOOT: C61.2, U14.23 (BOOT)
12V_FB: R57.1, R58.1, U14.17 (FB)
12V_MODE1: R40.1, R41.2, U14.21 (MODE1)
12V_MODE2: R44.2, U14.20 (MODE2)
12V_OUT: C65.2, C68.2, C71.2, C74.2, L3.2, R57.2, R62.1, U14.18 (V_{OUT})
12V_PHASE: R48.1, U14.24 (PHASE)
12V_VDD: C54.2, R40.2, U14.15 (V_{DD})
12V_VDRV: C57.2, U14.12 (V_{DRV})
+1V8: D6.1 (C), Q9.1 (G), R46.2, R50.2, TP5.1
+3V3: D9.1 (C), R59.2, R61.2, R65.2, TP6.1, U8.6 (MON1)
+3V3_STDB: C29.2, C31.2, C32.2, C37.2, D3.3, D11.1 (C), R9.2, R10.1, R12.2, R13.2, R14.1, R25.2, R28.2, R31.1, R47.2, R63.2, S1.1, S1.2, TP9.1, U7.6 (VCC), U8.3 (XIN), U8.30 (VCC), U9.2 (VDD), U10.1 (V_{IN})
+5V: R49.2
+5V_SoM: C51.1, D8.1 (C), R29.2, R51.2, R60.2, R64.2, TP7.1, U11.1 (VIN), U11.3 (EN)
+12V: R56.2
CARRIER_POWER_ON: R18.2, U8.9 (MON6)
DC_IN: C30.2, D2.1 (C), J2.3, J2.4, Q2.5 (D), U6.1 (IN)
GND: C28.1, C29.1, C30.1, C31.1, C32.1, C33.1, C34.1, C37.1, C39.1, C40.1, C41.1, C42.1, C43.1, C44.1, C45.1, C46.1, C47.1, C48.2, C49.2, C50.2, C51.2, C52.1, C53.1, C54.1, C55.1, C56.1, C57.1, C58.1, C62.1, C63.1, C64.1, C65.1, C66.1, C67.1, C68.1, C69.1, C70.1, C71.1, C72.1, C73.1, C74.1, C75.1, D2.2 (A), D4.1 (C), D5.1 (C), D6.2 (A), D8.2 (A), D9.2 (A), D10.2 (A), D11.2 (A), D12.1 (C), D13.1 (C), D14.1 (C), J2.1, J2.2, Q1.2 (S), Q3.2 (S), Q5.2 (S), Q6.2 (S), Q7.2 (S), Q8.2 (S), Q9.2 (S), Q10.2 (S), Q11.2 (S), R11.1, R17.1, R18.1, R19.1, R21.1, R22.1, R24.1, R26.1, R30.1, R34.1, R37.1, R39.1, R41.1, R42.1, R43.1, R44.1, R45.1, R50.1, R53.1, R55.1, R58.2, S4.3, S4.4, SW1.S1 (SH), SW1.S2 (SH), SW1.S3 (SH), SW1.S4 (SH), TP3.1, U6.2 (GND), U6.3 (CTL), U7.3 (GND), U8.1 (GND), U8.29 (TEST), U8.33 (PAD), U9.3 (GND), U10.4 (GND), U11.2 (GND), U12.3 (P_{GND}), U12.4 (P_{GND}), U12.13 (P_{GND}), U12.16 (A_{GND}), U12.25 (A_{GND}), U12.27 (P_{GND}), U13.3 (P_{GND}), U13.4 (P_{GND}), U13.13 (P_{GND}), U13.16 (A_{GND}), U13.25 (A_{GND}), U13.27 (P_{GND}), U14.3 (P_{GND}), U14.4 (P_{GND}), U14.13 (P_{GND}), U14.16 (A_{GND}), U14.25 (A_{GND}), U14.27 (P_{GND}), U15.3 (GND), U15.5 (PG), U15.7 (GND)
MODULE_POWER_ON: Q7.1 (G), R17.2, R45.2, U7.1 (B), U8.12 (EN5), U8.19 (MON5)
unnamed: C33.2, U9.5 (CT)
unnamed: C35.1, Q3.3 (D), R15.1
unnamed: C36.1, C38.1, Q4.4 (G), R16.1, R21.2
unnamed: C39.2, D5.2 (A), Q6.1 (G), R26.2, S1.3, S1.4
unnamed: C40.2, U10.7 (OFFT)
unnamed: C41.2, U10.3 (ONT)
unnamed: C61.1, R48.2
unnamed: D4.2 (A), R27.1
unnamed: D7.1 (C), Q9.3 (D)
unnamed: D7.2 (A), R51.1
unnamed: D12.2 (A), R64.1
unnamed: D13.2 (A), R65.1
unnamed: D14.2 (A), R66.1
unnamed: L3.1, U14.5 (SW), U14.6 (SW), U14.7 (SW), U14.8 (SW), U14.9 (SW)
unnamed: Q1.3 (D), R10.2, U7.2 (A)
unnamed: Q2.4 (G), U6.5 (GATE)
unnamed: Q3.1 (G), U9.1 (~RESET)
unnamed: Q5.1 (G), R28.1, U8.10 (EN4)
unnamed: Q8.3 (D), R49.1
unnamed: Q7.3 (D), Q8.1 (G), Q10.1 (G), Q11.1 (G), R47.1
unnamed: Q10.3 (D), R56.1
unnamed: Q11.3 (D), R59.1
unnamed: R11.2, SW1.3
unnamed: R13.1, U8.32 (ROSC)
unnamed: R23.1, R25.1, U10.8 (~KILL)
unnamed: R23.2, U7.4 (Y)
unnamed: R29.1, R30.2, U8.7 (MON2)
unnamed: R31.2, R35.2, U10.6 (EN)
unnamed: R32.1, U10.5 (~INT)
unnamed: R33.1, R34.2, U8.8 (MON3)
unnamed: SW1.2, U9.4 (~MR)
unnamed: U12.10 (GL), U12.11 (GL), U12.28 (GL)
unnamed: U13.10 (GL), U13.11 (GL), U13.28 (GL)
unnamed: U14.10 (GL), U14.11 (GL), U14.28 (GL)
PWRBTN: C35.2, D3.1, D3.2, R14.2, R15.2, S4.1, S4.2, U10.2 (~PB)
SYS_RESET_N: Q6.3 (D)
SYS_SCL: R9.1, TP1.1, U8.22 (SCL)
SYS_SDA: R12.1, TP2.1, U8.21 (SDA)
SYS_VIN_HV_EN: R19.2, U8.11 (EN3), U14.19 (EN)
SYS_VIN_MV_EN: R22.2, U8.24 (EN2), U12.19 (EN)
SYS_VIN_SV_EN: R24.2, U8.23 (EN1), U13.19 (EN)
USBPD0_HV: C34.2, C36.2, Q2.1 (S), Q2.2 (S), Q2.3 (S), Q4.1 (S), Q4.2 (S), Q4.3 (S), R16.2, R20.1, U6.6 (SENSE)
VCC: C38.2, C42.2, C43.2, C44.2, C45.2, C46.2, C47.2, C48.1, C49.1, C50.1, C62.2, Q4.5 (D), R20.2, R27.2, TP4.1, U12.1 (V_{IN}), U12.2 (V_{IN}), U12.22 (V_{IN}), U12.26 (V_{IN}), U13.1 (V_{IN}), U13.2 (V_{IN}), U13.22 (V_{IN}), U13.26 (V_{IN}), U14.1 (V_{IN}), U14.2 (V_{IN}), U14.22 (V_{IN}), U14.26 (V_{IN}), U15.4 (EN), U15.6 (V_{IN})
VDDIN_PWR_BAD_N: Q5.3 (D), U8.18 (MON4)
VDD_SoM_HV: D10.1 (C), R33.2, R62.2, R66.2, TP8.1
~CW_PWRBTN: R32.2
~MODULE_SHDN_N: Q1.1 (G)
~PWR_SEQ_RST: C28.2, R35.1, U8.5 (~RST)

Notes on the sheet:
Power-up and reset
Power sequencer
3.3V @150mA
Power button
Simulate button click for autostart
3-2 manual 1-2 auto
3V3 STANDBY LDO
DISCHARGE CIRCUIT
R_{FB_H} = (R_{FB_L}(V_{OUT}-0.6))/0.6
V_{OUT} = 0.6*(R_{FB_H}+R_{FB_L})/R_{FB_L}
V_{OUT} = 0.6*(45k3+10k)/10k = 3.318[V]
12V @12A
Soft start
Ideal-diode O-Ring
3V3 @12A
USB controller has an integrated ideal diode
1V8 LDO
18 - 20 V
Reset button
5V @12A
V_{OUT} = 0.6*(191k+10k)/10k = 12.06[V]
