antmicro/jetson-agx-thor-baseboard/recovery_usb.kicad_sch

## KiCad design recovery_usb.kicad_sch (2026-03-19, an earlier design)

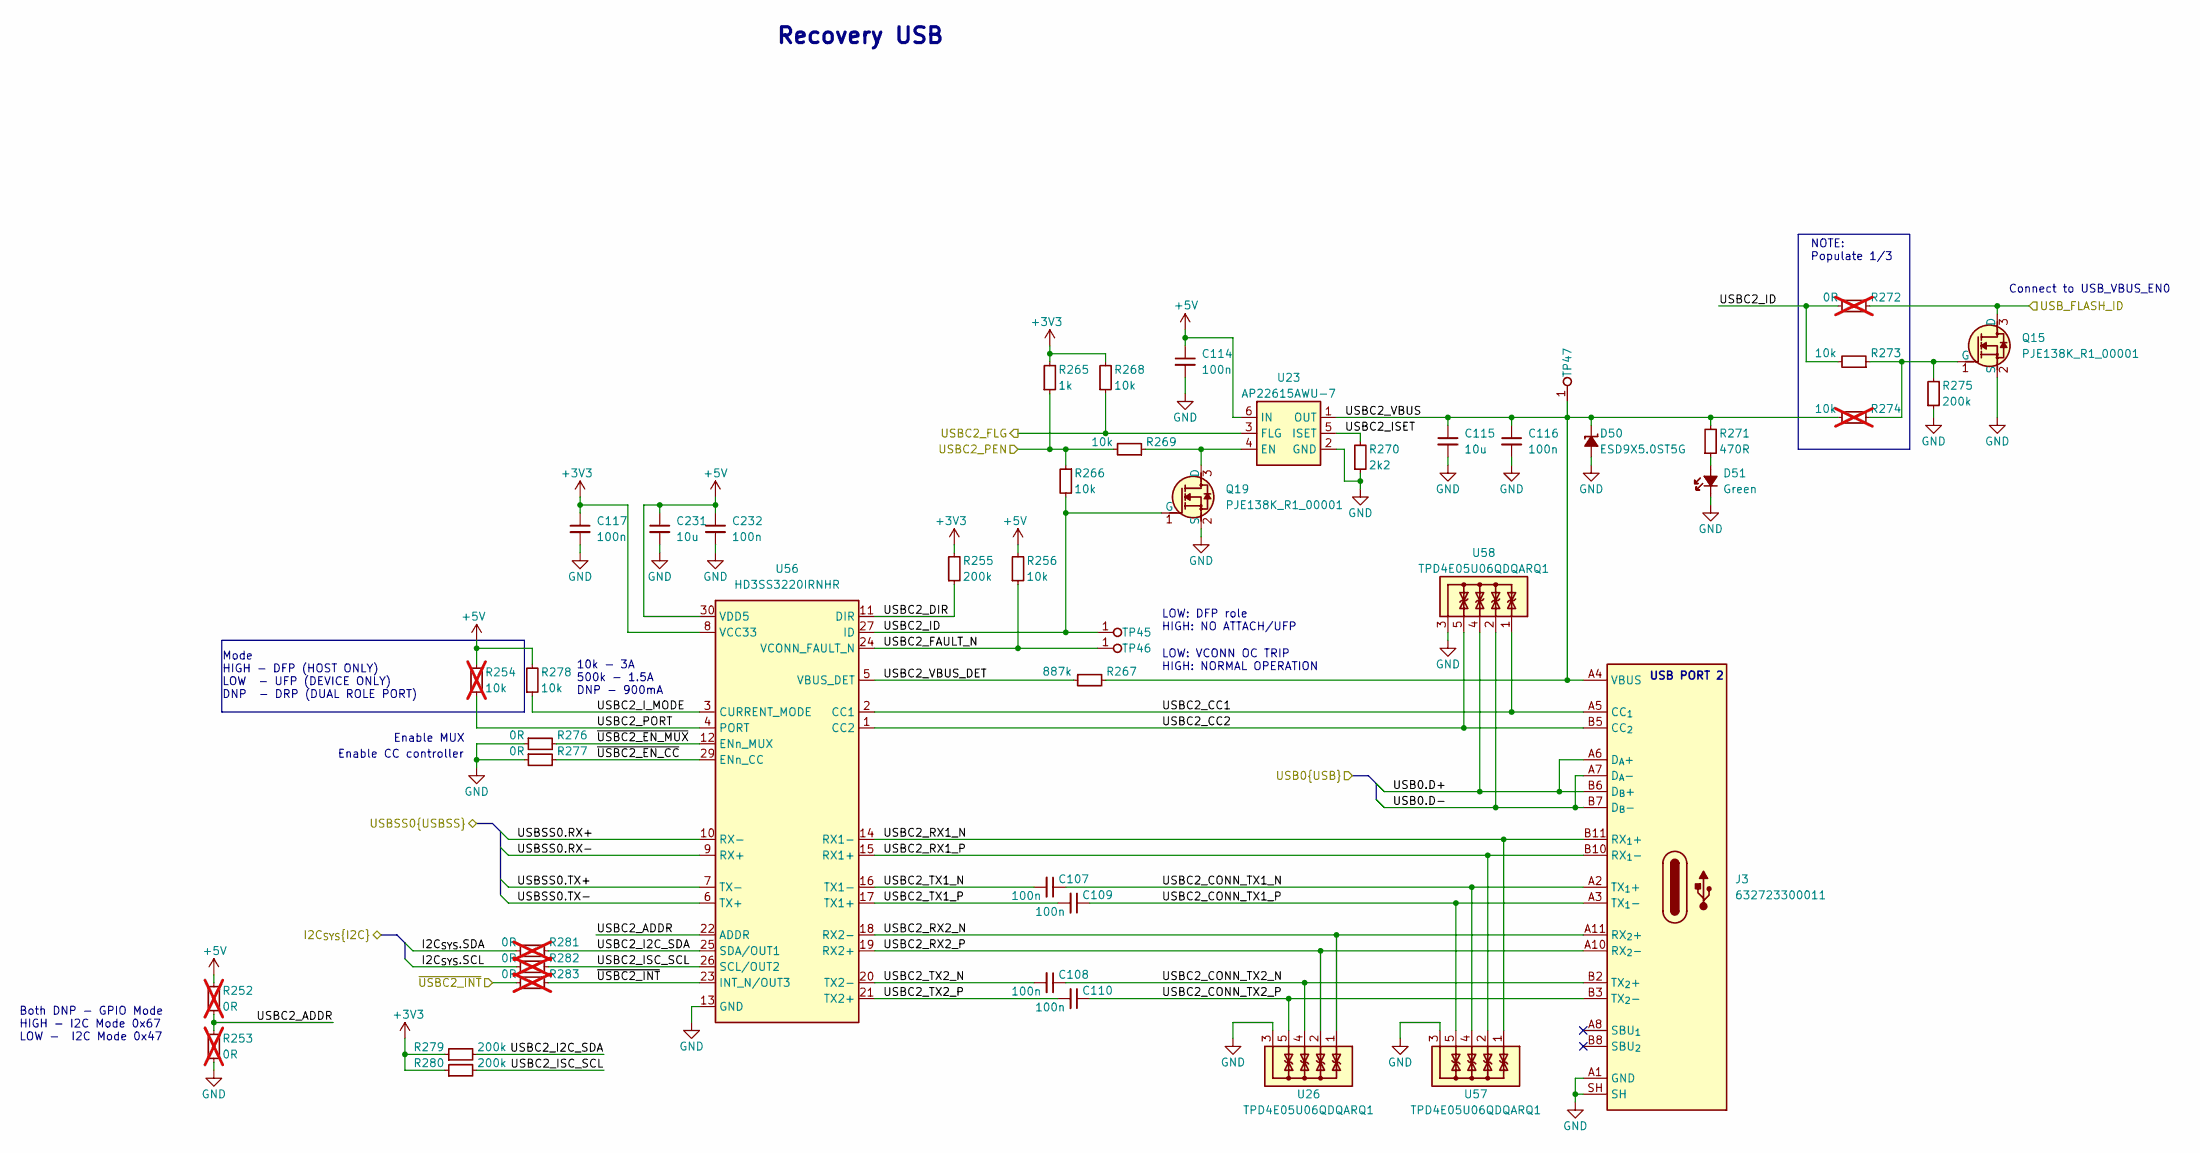
[picture p10: schematic recovery_usb.kicad_sch]

Parts:
C107, C108, C109, C110, C114, C116, C117, C232: C_100n_0402; C_0402_1005Metric; Voltage 50V; MPN GRM155R61H104KE14D
C115, C231: C_10u_0603; C_0603_1608Metric; MPN GRM188R61A106KE69D
D50: ESD9X5.0ST5G; SOD-923; MPN ESD9X5.0ST5G
D51: LED_G_0603_LTST-C190GKT; LED_0603_1608Metric_G; MPN LTST-C190GKT
J3: USB-C_WE_632723300011; USB-C_Receptacle_WE_632723300011; MPN 632723300011
Q15, Q19: PJE138K; SOT-523; MPN PJE138K_R1_00001
R252, R253, R272, R281, R282, R283: R_0R_0402; R_0402_1005Metric; MPN ERJ2GE0R00X; not fitted
R254, R274: R_10k_0402; R_0402_1005Metric; Tolerance 1%; MPN CR0402-FX-1002GLF; not fitted
R255, R275, R279, R280: R_200k_0402; R_0402_1005Metric; Tolerance 1%; MPN CR0402-FX-2003GLF
R256, R266, R268, R269, R273, R278: R_10k_0402; R_0402_1005Metric; Tolerance 1%; MPN CR0402-FX-1002GLF
R265: R_1k_0402; R_0402_1005Metric; Tolerance 1%; MPN CR0402-FX-1001GLF
R267: R_887k_0402; R_0402_1005Metric; Tolerance 1%; MPN ERJ-2RKF8873X
R270: R_2k2_0402; R_0402_1005Metric; Tolerance 1%; MPN CR0402-FX-2201GLF
R271: R_470R_0402; R_0402_1005Metric; Tolerance 1%; MPN CR0402-FX-4700GLF
R276, R277: R_0R_0402; R_0402_1005Metric; MPN ERJ2GE0R00X
TP45, TP46, TP47: TP_0.75mm_SMD; TP_SMD_0.75mm
U23: AP22615A_TSOT26; TSOT23-6; MPN AP22615AWU-7
U26, U57, U58: TPD4E05U06QDQARQ1; USON-10_2.5x1mm_P0.5mm; MPN TPD4E05U06QDQARQ1
U56: HD3SS3220IRNHR; WQFN-30-1EP_4.6x2.6mm_P0.4mm; MPN HD3SS3220IRNHR

Connections:
+3V3: C117.1, R255.2, R265.2, R268.2, R279.1, R280.1, U56.8 (VCC33)
+5V: C114.1, C231.1, C232.1, R252.2, R254.1, R256.2, R278.2, U23.6 (IN), U56.30 (VDD5)
GND: C114.2, C115.2, C116.2, C117.2, C231.2, C232.2, D50.2 (A), D51.1 (C), J3.A1 (GND), J3.A12 (GND), J3.B1 (GND), J3.B12 (GND), J3.SH, Q15.2 (S), Q19.2 (S), R253.1, R270.1, R275.1, R276.1, R277.1, U23.2 (GND), U26.3, U26.8, U56.13 (GND), U56.28 (GND), U56.31 (GND), U57.3, U57.8, U58.3, U58.8
I2C_{SYS}.SCL: R282.1
I2C_{SYS}.SDA: R281.1
unnamed: D51.2 (A), R271.1
unnamed: Q15.1 (G), R273.1, R274.1, R275.2
unnamed: Q19.3 (D), R269.1, U23.4 (EN)
USB0.D+: J3.A6 (D_{A}+), J3.B6 (D_{B}+), U58.4, U58.7
USB0.D-: J3.A7 (D_{A}-), J3.B7 (D_{B}-), U58.2, U58.9
USBC2_ADDR: R252.1, R253.2, U56.22 (ADDR)
USBC2_CC1: J3.A5 (CC_{1}), U56.2 (CC1), U58.1, U58.10
USBC2_CC2: J3.B5 (CC_{2}), U56.1 (CC2), U58.5, U58.6
USBC2_CONN_TX1_N: C107.1, J3.A2 (TX_{1}+), U57.4, U57.7
USBC2_CONN_TX1_P: C109.1, J3.A3 (TX_{1}-), U57.5, U57.6
USBC2_CONN_TX2_N: C108.1, J3.B2 (TX_{2}+), U26.4, U26.7
USBC2_CONN_TX2_P: C110.1, J3.B3 (TX_{2}-), U26.5, U26.6
USBC2_DIR: R255.1, U56.11 (DIR)
USBC2_FAULT_N: R256.1, TP46.1, U56.24 (VCONN_FAULT_N)
USBC2_FLG: R268.1, U23.3 (FLG)
USBC2_I2C_SDA: R279.2, R281.2, U56.25 (SDA/OUT1)
USBC2_ID: Q19.1 (G), R266.2, R272.1, R273.2, TP45.1, U56.27 (ID)
USBC2_ISC_SCL: R280.2, R282.2, U56.26 (SCL/OUT2)
USBC2_ISET: R270.2, U23.5 (ISET)
USBC2_I_MODE: R278.1, U56.3 (CURRENT_MODE)
USBC2_PEN: R265.1, R266.1, R269.2
USBC2_PORT: R254.2, U56.4 (PORT)
USBC2_RX1_N: J3.B11 (RX_{1}+), U56.14 (RX1-), U57.1, U57.10
USBC2_RX1_P: J3.B10 (RX_{1}-), U56.15 (RX1+), U57.2, U57.9
USBC2_RX2_N: J3.A11 (RX_{2}+), U26.1, U26.10, U56.18 (RX2-)
USBC2_RX2_P: J3.A10 (RX_{2}-), U26.2, U26.9, U56.19 (RX2+)
USBC2_TX1_N: C107.2, U56.16 (TX1-)
USBC2_TX1_P: C109.2, U56.17 (TX1+)
USBC2_TX2_N: C108.2, U56.20 (TX2-)
USBC2_TX2_P: C110.2, U56.21 (TX2+)
USBC2_VBUS: C115.1, C116.1, D50.1 (C), J3.A4 (VBUS), J3.A9 (VBUS), J3.B4 (VBUS), J3.B9 (VBUS), R267.2, R271.2, R274.2, TP47.1, U23.1 (OUT)
USBC2_VBUS_DET: R267.1, U56.5 (VBUS_DET)
USBSS0.RX+: U56.10 (RX-)
USBSS0.RX-: U56.9 (RX+)
USBSS0.TX+: U56.7 (TX-)
USBSS0.TX-: U56.6 (TX+)
USB_FLASH_ID: Q15.3 (D), R272.2
~USBC2_EN_CC: R277.2, U56.29 (ENn_CC)
~USBC2_EN_MUX: R276.2, U56.12 (ENn_MUX)
~USBC2_INT: R283.1, R283.2, U56.23 (INT_N/OUT3)

Notes on the sheet:
NOTE: Populate 1/3
Connect to USB_VBUS_EN0
Enable MUX
LOW: DFP role HIGH: NO ATTACH/UFP
10k - 3A 500k - 1.5A DNP - 900mA
LOW: VCONN OC TRIP HIGH: NORMAL OPERATION
Both DNP - GPIO Mode HIGH - I2C Mode 0x67 LOW - I2C Mode 0x47
USB PORT 2
Recovery USB
Mode HIGH - DFP (HOST ONLY) LOW - UFP (DEVICE ONLY) DNP - DRP (DUAL ROLE PORT)
Enable CC controller
