antmicro/jetson-agx-thor-baseboard/sfp.kicad_sch

## KiCad design sfp.kicad_sch (2026-02-19, an earlier design)

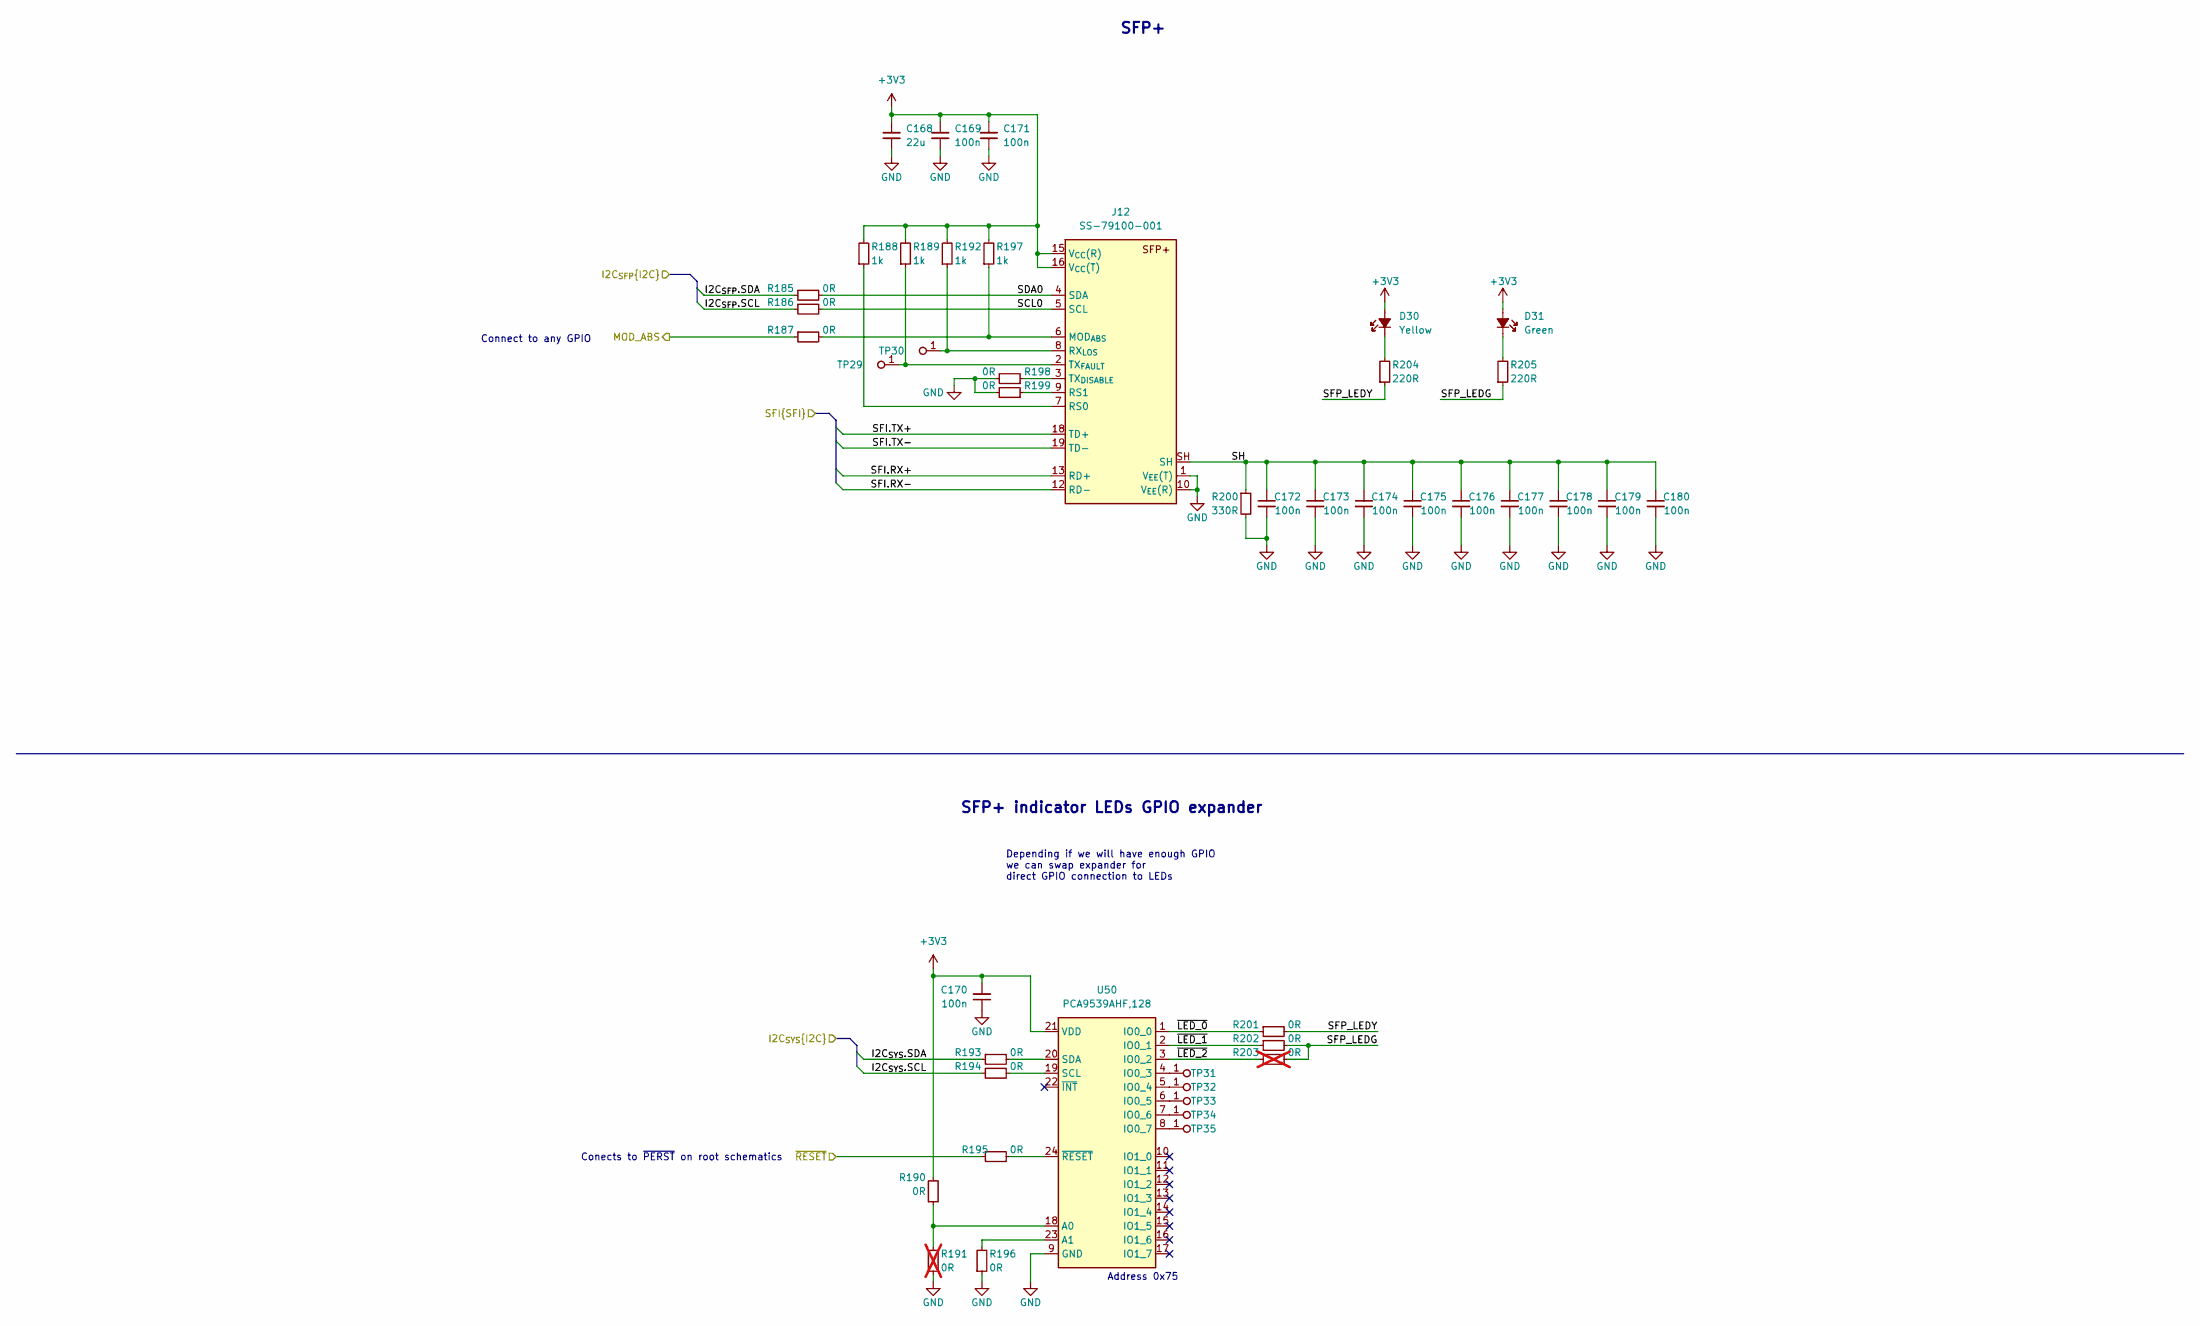
[picture p11: schematic sfp.kicad_sch]

Parts:
C168: C_22u_16V_0603; C_0603_1608Metric; Voltage 16V; MPN CL10A226MO7JZNC
C169, C170, C171, C172, C173, C174, C175, C176, C177, C178, C179, C180: C_100n_0402; C_0402_1005Metric; Voltage 50V; MPN GRM155R61H104KE14D
D30: LED_Y_0603_LTST-C191KSKT; LED_0603_1608Metric_Y; MPN LTST-C191KSKT
D31: LED_G_0603_LTST-C190GKT; LED_0603_1608Metric_G; MPN LTST-C190GKT
J12: Bel-Fuse_SFP+_1x20_SS-79100-001; Conn_Bel-Fuse_SFP+_1x20_SS-79100-001; MPN SS-79100-001
R185, R186, R187, R190, R193, R194, R195, R196, R198, R199, R201, R202: R_0R_0402; R_0402_1005Metric; MPN ERJ2GE0R00X
R188, R189, R192, R197: R_1k_0402; R_0402_1005Metric; Tolerance 1%; MPN CR0402-FX-1001GLF
R191, R203: R_0R_0402; R_0402_1005Metric; MPN ERJ2GE0R00X; not fitted
R200: R_330R_0402; R_0402_1005Metric; Tolerance 1%; MPN CR0402-FX-3300GLF
R204, R205: R_220R_0402; R_0402_1005Metric; Tolerance 1%; MPN CR0402-FX-2200GLF
TP29, TP30, TP31, TP32, TP33, TP34, TP35: TP_0.75mm_SMD; TP_SMD_0.75mm
U50: PCA9539AHF; QFN-24-1EP_4x4mm_P0.5_EP2.1x2.1mm; MPN PCA9539AHF,128

Connections:
+3V3: C168.2, C169.2, C170.2, C171.2, D30.2 (A), D31.2 (A), J12.15 (V_{CC}(R)), J12.16 (V_{CC}(T)), R188.2, R189.2, R190.2, R192.2, R197.2, U50.21 (VDD)
GND: C168.1, C169.1, C170.1, C171.1, C172.2, C173.2, C174.2, C175.2, C176.2, C177.2, C178.2, C179.2, C180.2, J12.1 (V_{EE}(T)), J12.10 (V_{EE}(R)), J12.11 (V_{EE}(R)), J12.14 (V_{EE}(R)), J12.17 (V_{EE}(T)), J12.20 (V_{EE}(T)), R191.1, R196.1, R198.2, R199.2, R200.2, U50.9 (GND), U50.25 (GND)
I2C_{SFP}.SCL: R186.1
I2C_{SFP}.SDA: R185.1
I2C_{SYS}.SCL: R194.1
I2C_{SYS}.SDA: R193.1
MOD_ABS: R187.1
unnamed: D30.1 (C), R204.2
unnamed: D31.1 (C), R205.2
unnamed: J12.2 (TX_{FAULT}), R189.1, TP29.1
unnamed: J12.3 (TX_{DISABLE}), R198.1
unnamed: J12.6 (MOD_{ABS}), R187.2, R197.1
unnamed: J12.7 (RS0), R188.1
unnamed: J12.8 (RX_{LOS}), R192.1, TP30.1
unnamed: J12.9 (RS1), R199.1
unnamed: R190.1, R191.2, U50.18 (A0)
unnamed: R193.2, U50.20 (SDA)
unnamed: R194.2, U50.19 (SCL)
unnamed: R195.2, U50.24 (~RESET)
unnamed: R196.2, U50.23 (A1)
unnamed: TP31.1, U50.4 (IO0_3)
unnamed: TP32.1, U50.5 (IO0_4)
unnamed: TP33.1, U50.6 (IO0_5)
unnamed: TP34.1, U50.7 (IO0_6)
unnamed: TP35.1, U50.8 (IO0_7)
SCL0: J12.5 (SCL), R186.2
SDA0: J12.4 (SDA), R185.2
SFI.RX+: J12.13 (RD+)
SFI.RX-: J12.12 (RD-)
SFI.TX+: J12.18 (TD+)
SFI.TX-: J12.19 (TD-)
SFP_LEDG: R202.2, R203.2, R205.1
SFP_LEDY: R201.2, R204.1
SH: C172.1, C173.1, C174.1, C175.1, C176.1, C177.1, C178.1, C179.1, C180.1, J12.SH, R200.1
~LED_0: R201.1, U50.1 (IO0_0)
~LED_1: R202.1, U50.2 (IO0_1)
~LED_2: R203.1, U50.3 (IO0_2)
~RESET: R195.1

Notes on the sheet:
SFP+
SFP+ indicator LEDs GPIO expander
Connect to any GPIO
Conects to ~{PERST} on root schematics
Depending if we will have enough GPIO we can swap expander for direct GPIO connection to LEDs
Address 0x75
