antmicro/jetson-agx-thor-baseboard/som_io2.kicad_sch

## KiCad design som_io2.kicad_sch (2026-03-19, an earlier design)

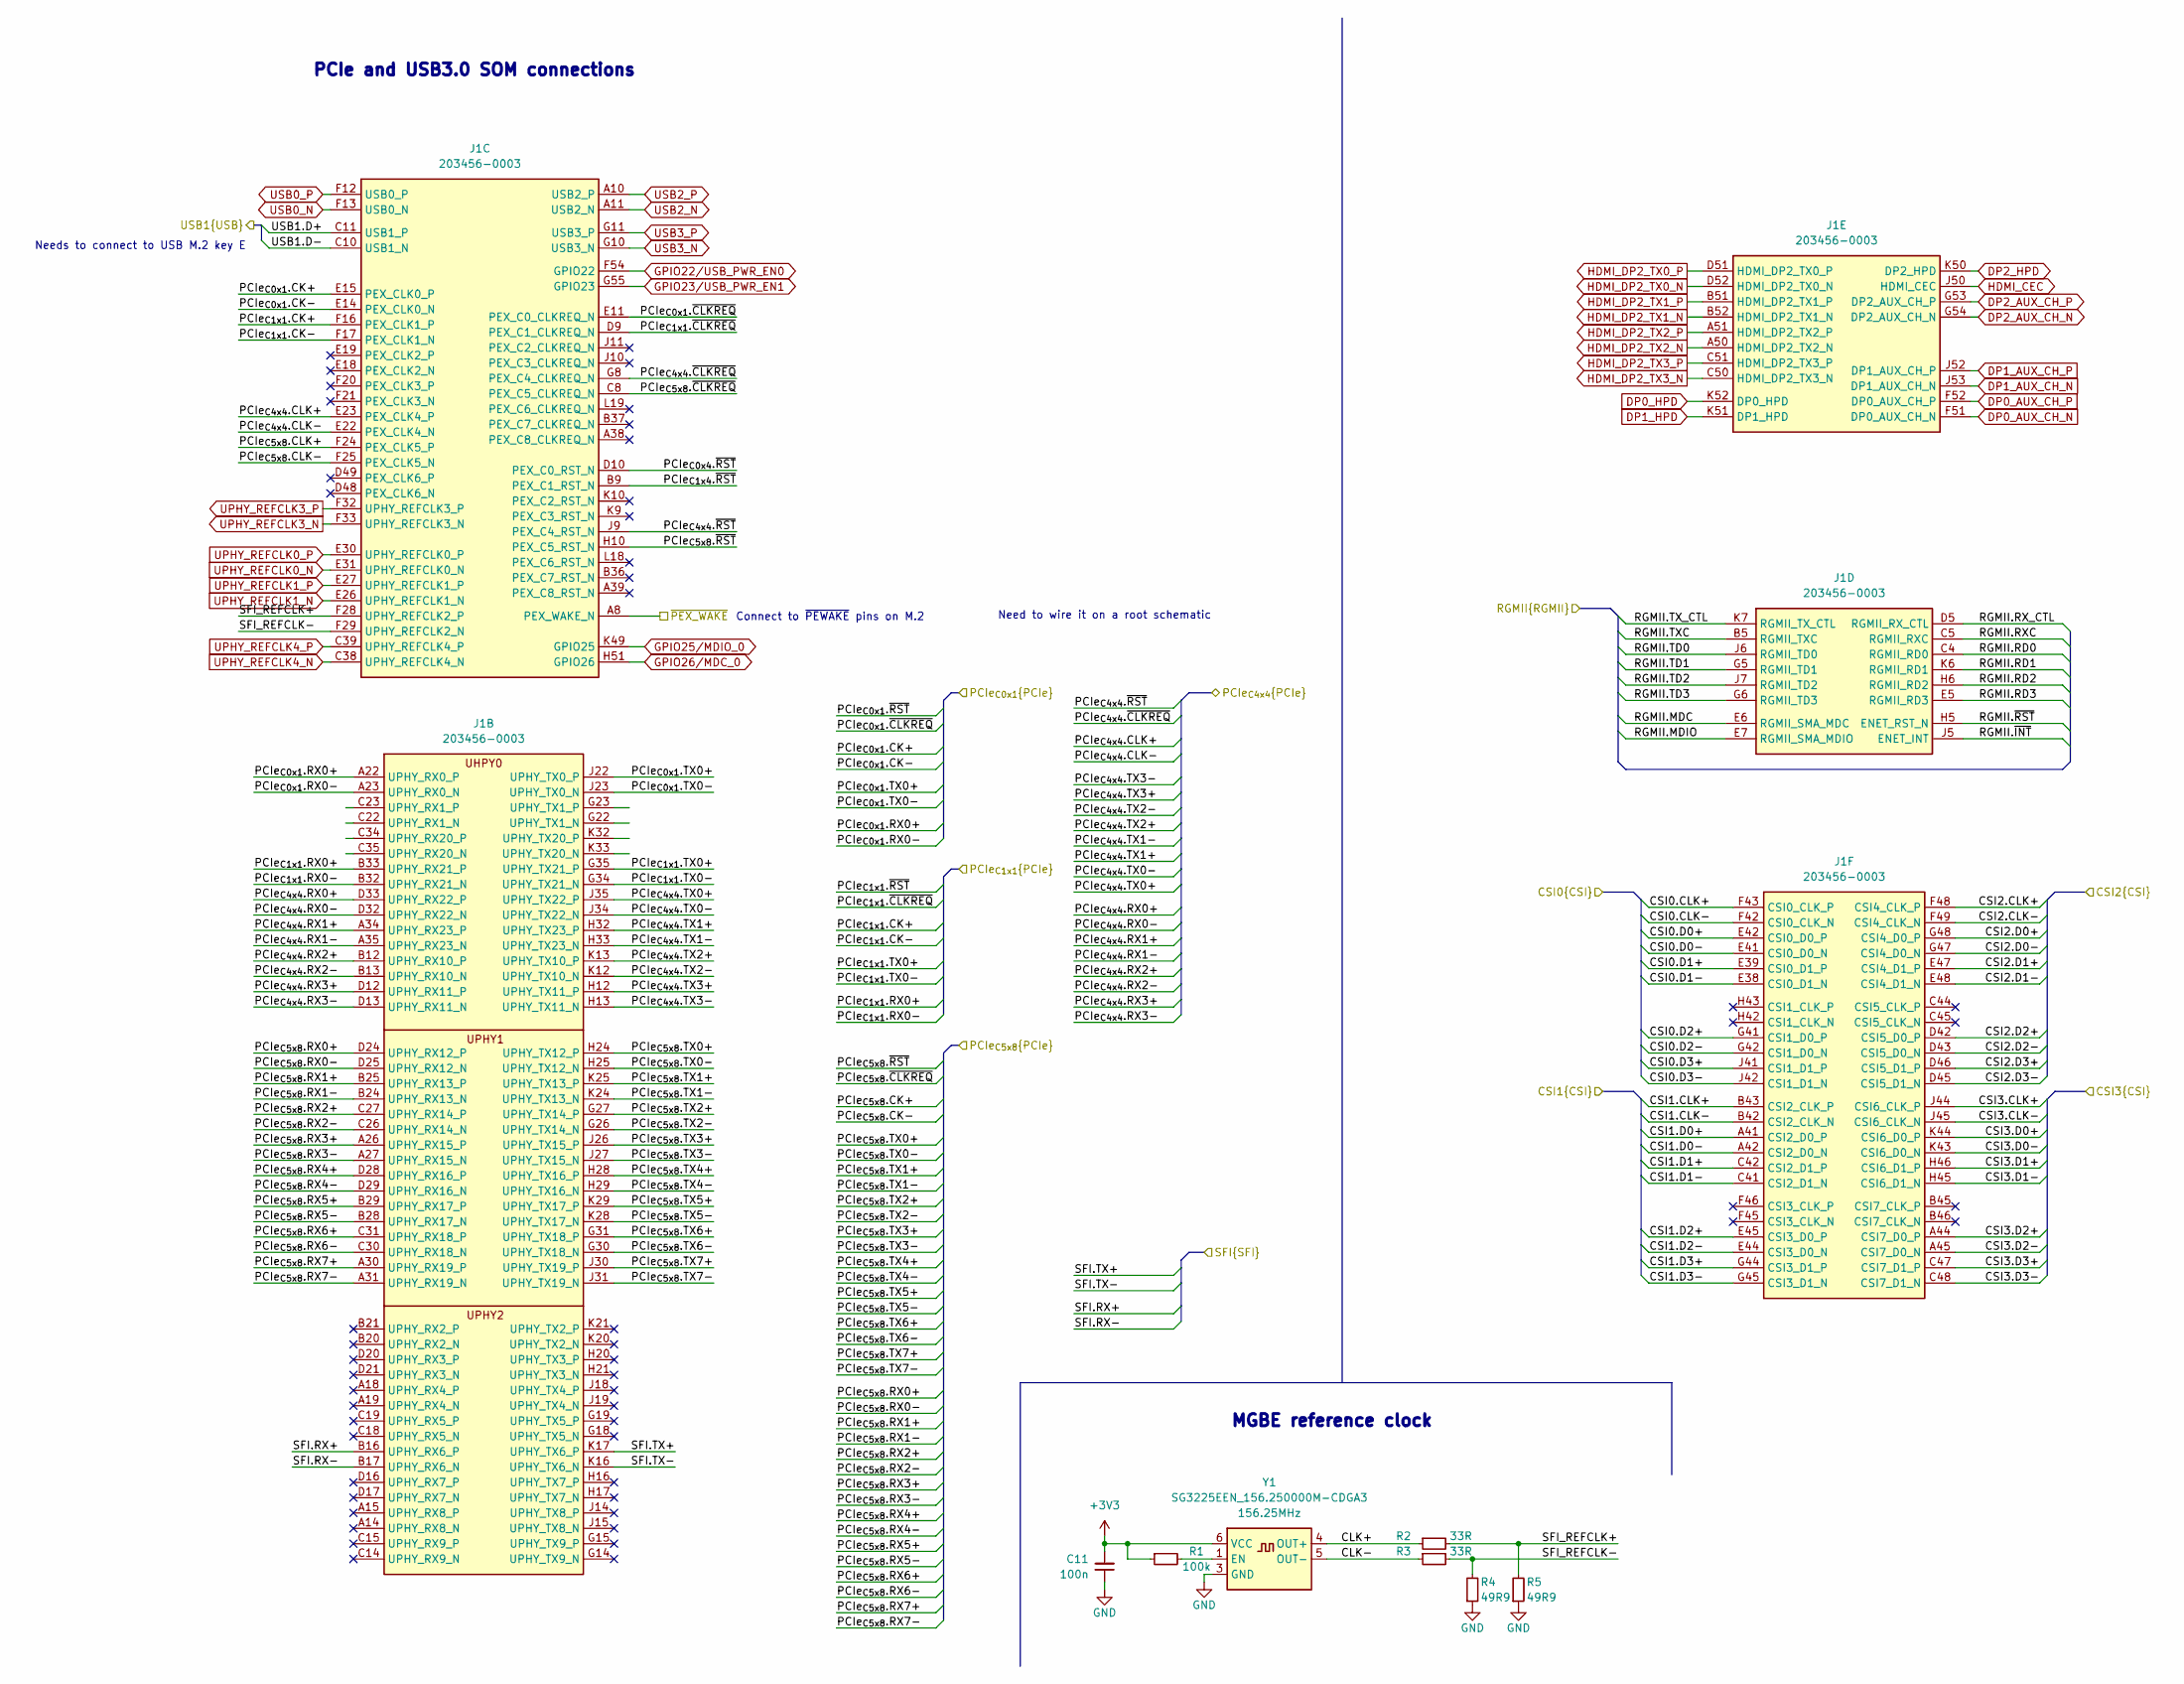
[picture p12: schematic som_io2.kicad_sch]

Parts:
C11: C_100n_0402; C_0402_1005Metric; Voltage 50V; MPN GRM155R61H104KE14D
J1: Hermaphroditic_Molex_203456-0003_CUSTOM_Jetson_Or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; Conn_Hermaphroditic_Molex_203456-0003_mirrored; MPN 203456-0003
R1: R_100k_0402; R_0402_1005Metric; Tolerance 1%; MPN CR0402-FX-1003GLF
R2, R3: R_33R_0402; R_0402_1005Metric; Tolerance 1%; MPN CR0402-FX-33R0GLF
R4, R5: R_49R9_0402; R_0402_1005Metric; Tolerance 1%; MPN CR0402-FX-49R9GLF
Y1: Oscillator_156.25MHz_SG3225EEN; Oscillator_SMD_Epson_SG3225EEN_3.2x2.5x1.2mm; MPN SG3225EEN_156.250000M-CDGA3

Connections:
+3V3: C11.2, R1.1, Y1.6 (VCC)
CLK+: R2.1, Y1.4 (OUT+)
CLK-: R3.1, Y1.5 (OUT-)
CSI0.CLK+: J1.F43 (CSI0_CLK_P)
CSI0.CLK-: J1.F42 (CSI0_CLK_N)
CSI0.D0+: J1.E42 (CSI0_D0_P)
CSI0.D0-: J1.E41 (CSI0_D0_N)
CSI0.D1+: J1.E39 (CSI0_D1_P)
CSI0.D1-: J1.E38 (CSI0_D1_N)
CSI0.D2+: J1.G41 (CSI1_D0_P)
CSI0.D2-: J1.G42 (CSI1_D0_N)
CSI0.D3+: J1.J41 (CSI1_D1_P)
CSI0.D3-: J1.J42 (CSI1_D1_N)
CSI1.CLK+: J1.B43 (CSI2_CLK_P)
CSI1.CLK-: J1.B42 (CSI2_CLK_N)
CSI1.D0+: J1.A41 (CSI2_D0_P)
CSI1.D0-: J1.A42 (CSI2_D0_N)
CSI1.D1+: J1.C42 (CSI2_D1_P)
CSI1.D1-: J1.C41 (CSI2_D1_N)
CSI1.D2+: J1.E45 (CSI3_D0_P)
CSI1.D2-: J1.E44 (CSI3_D0_N)
CSI1.D3+: J1.G44 (CSI3_D1_P)
CSI1.D3-: J1.G45 (CSI3_D1_N)
CSI2.CLK+: J1.F48 (CSI4_CLK_P)
CSI2.CLK-: J1.F49 (CSI4_CLK_N)
CSI2.D0+: J1.G48 (CSI4_D0_P)
CSI2.D0-: J1.G47 (CSI4_D0_N)
CSI2.D1+: J1.E47 (CSI4_D1_P)
CSI2.D1-: J1.E48 (CSI4_D1_N)
CSI2.D2+: J1.D42 (CSI5_D0_P)
CSI2.D2-: J1.D43 (CSI5_D0_N)
CSI2.D3+: J1.D46 (CSI5_D1_P)
CSI2.D3-: J1.D45 (CSI5_D1_N)
CSI3.CLK+: J1.J44 (CSI6_CLK_P)
CSI3.CLK-: J1.J45 (CSI6_CLK_N)
CSI3.D0+: J1.K44 (CSI6_D0_P)
CSI3.D0-: J1.K43 (CSI6_D0_N)
CSI3.D1+: J1.H46 (CSI6_D1_P)
CSI3.D1-: J1.H45 (CSI6_D1_N)
CSI3.D2+: J1.A44 (CSI7_D0_P)
CSI3.D2-: J1.A45 (CSI7_D0_N)
CSI3.D3+: J1.C47 (CSI7_D1_P)
CSI3.D3-: J1.C48 (CSI7_D1_N)
DP0_AUX_CH_N: J1.F51 (DP0_AUX_CH_N)
DP0_AUX_CH_P: J1.F52 (DP0_AUX_CH_P)
DP0_HPD: J1.K52 (DP0_HPD)
DP1_AUX_CH_N: J1.J53 (DP1_AUX_CH_N)
DP1_AUX_CH_P: J1.J52 (DP1_AUX_CH_P)
DP1_HPD: J1.K51 (DP1_HPD)
DP2_AUX_CH_N: J1.G54 (DP2_AUX_CH_N)
DP2_AUX_CH_P: J1.G53 (DP2_AUX_CH_P)
DP2_HPD: J1.K50 (DP2_HPD)
GND: C11.1, R4.1, R5.1, Y1.3 (GND)
GPIO22/USB_PWR_EN0: J1.F54 (GPIO22)
GPIO23/USB_PWR_EN1: J1.G55 (GPIO23)
GPIO25/MDIO_0: J1.K49 (GPIO25)
GPIO26/MDC_0: J1.H51 (GPIO26)
HDMI_CEC: J1.J50 (HDMI_CEC)
HDMI_DP2_TX0_N: J1.D52 (HDMI_DP2_TX0_N)
HDMI_DP2_TX0_P: J1.D51 (HDMI_DP2_TX0_P)
HDMI_DP2_TX1_N: J1.B52 (HDMI_DP2_TX1_N)
HDMI_DP2_TX1_P: J1.B51 (HDMI_DP2_TX1_P)
HDMI_DP2_TX2_N: J1.A50 (HDMI_DP2_TX2_N)
HDMI_DP2_TX2_P: J1.A51 (HDMI_DP2_TX2_P)
HDMI_DP2_TX3_N: J1.C50 (HDMI_DP2_TX3_N)
HDMI_DP2_TX3_P: J1.C51 (HDMI_DP2_TX3_P)
unnamed: R1.2, Y1.1 (EN)
PCIe_{C0x1}.CK+: J1.E15 (PEX_CLK0_P)
PCIe_{C0x1}.CK-: J1.E14 (PEX_CLK0_N)
PCIe_{C0x1}.RX0+: J1.A22 (UPHY_RX0_P)
PCIe_{C0x1}.RX0-: J1.A23 (UPHY_RX0_N)
PCIe_{C0x1}.TX0+: J1.J22 (UPHY_TX0_P)
PCIe_{C0x1}.TX0-: J1.J23 (UPHY_TX0_N)
PCIe_{C0x1}.~CLKREQ: J1.E11 (PEX_C0_CLKREQ_N)
PCIe_{C0x4}.~RST: J1.D10 (PEX_C0_RST_N)
PCIe_{C1x1}.CK+: J1.F16 (PEX_CLK1_P)
PCIe_{C1x1}.CK-: J1.F17 (PEX_CLK1_N)
PCIe_{C1x1}.RX0+: J1.B33 (UPHY_RX21_P)
PCIe_{C1x1}.RX0-: J1.B32 (UPHY_RX21_N)
PCIe_{C1x1}.TX0+: J1.G35 (UPHY_TX21_P)
PCIe_{C1x1}.TX0-: J1.G34 (UPHY_TX21_N)
PCIe_{C1x1}.~CLKREQ: J1.D9 (PEX_C1_CLKREQ_N)
PCIe_{C1x4}.~RST: J1.B9 (PEX_C1_RST_N)
PCIe_{C4x4}.CLK+: J1.E23 (PEX_CLK4_P)
PCIe_{C4x4}.CLK-: J1.E22 (PEX_CLK4_N)
PCIe_{C4x4}.RX0+: J1.D33 (UPHY_RX22_P)
PCIe_{C4x4}.RX0-: J1.D32 (UPHY_RX22_N)
PCIe_{C4x4}.RX1+: J1.A34 (UPHY_RX23_P)
PCIe_{C4x4}.RX1-: J1.A35 (UPHY_RX23_N)
PCIe_{C4x4}.RX2+: J1.B12 (UPHY_RX10_P)
PCIe_{C4x4}.RX2-: J1.B13 (UPHY_RX10_N)
PCIe_{C4x4}.RX3+: J1.D12 (UPHY_RX11_P)
PCIe_{C4x4}.RX3-: J1.D13 (UPHY_RX11_N)
PCIe_{C4x4}.TX0+: J1.J35 (UPHY_TX22_P)
PCIe_{C4x4}.TX0-: J1.J34 (UPHY_TX22_N)
PCIe_{C4x4}.TX1+: J1.H32 (UPHY_TX23_P)
PCIe_{C4x4}.TX1-: J1.H33 (UPHY_TX23_N)
PCIe_{C4x4}.TX2+: J1.K13 (UPHY_TX10_P)
PCIe_{C4x4}.TX2-: J1.K12 (UPHY_TX10_N)
PCIe_{C4x4}.TX3+: J1.H12 (UPHY_TX11_P)
PCIe_{C4x4}.TX3-: J1.H13 (UPHY_TX11_N)
PCIe_{C4x4}.~CLKREQ: J1.G8 (PEX_C4_CLKREQ_N)
PCIe_{C4x4}.~RST: J1.J9 (PEX_C4_RST_N)
PCIe_{C5x8}.CLK+: J1.F24 (PEX_CLK5_P)
PCIe_{C5x8}.CLK-: J1.F25 (PEX_CLK5_N)
PCIe_{C5x8}.RX0+: J1.D24 (UPHY_RX12_P)
PCIe_{C5x8}.RX0-: J1.D25 (UPHY_RX12_N)
PCIe_{C5x8}.RX1+: J1.B25 (UPHY_RX13_P)
PCIe_{C5x8}.RX1-: J1.B24 (UPHY_RX13_N)
PCIe_{C5x8}.RX2+: J1.C27 (UPHY_RX14_P)
PCIe_{C5x8}.RX2-: J1.C26 (UPHY_RX14_N)
PCIe_{C5x8}.RX3+: J1.A26 (UPHY_RX15_P)
PCIe_{C5x8}.RX3-: J1.A27 (UPHY_RX15_N)
PCIe_{C5x8}.RX4+: J1.D28 (UPHY_RX16_P)
PCIe_{C5x8}.RX4-: J1.D29 (UPHY_RX16_N)
PCIe_{C5x8}.RX5+: J1.B29 (UPHY_RX17_P)
PCIe_{C5x8}.RX5-: J1.B28 (UPHY_RX17_N)
PCIe_{C5x8}.RX6+: J1.C31 (UPHY_RX18_P)
PCIe_{C5x8}.RX6-: J1.C30 (UPHY_RX18_N)
PCIe_{C5x8}.RX7+: J1.A30 (UPHY_RX19_P)
PCIe_{C5x8}.RX7-: J1.A31 (UPHY_RX19_N)
PCIe_{C5x8}.TX0+: J1.H24 (UPHY_TX12_P)
PCIe_{C5x8}.TX0-: J1.H25 (UPHY_TX12_N)
PCIe_{C5x8}.TX1+: J1.K25 (UPHY_TX13_P)
PCIe_{C5x8}.TX1-: J1.K24 (UPHY_TX13_N)
PCIe_{C5x8}.TX2+: J1.G27 (UPHY_TX14_P)
PCIe_{C5x8}.TX2-: J1.G26 (UPHY_TX14_N)
PCIe_{C5x8}.TX3+: J1.J26 (UPHY_TX15_P)
PCIe_{C5x8}.TX3-: J1.J27 (UPHY_TX15_N)
PCIe_{C5x8}.TX4+: J1.H28 (UPHY_TX16_P)
PCIe_{C5x8}.TX4-: J1.H29 (UPHY_TX16_N)
PCIe_{C5x8}.TX5+: J1.K29 (UPHY_TX17_P)
PCIe_{C5x8}.TX5-: J1.K28 (UPHY_TX17_N)
PCIe_{C5x8}.TX6+: J1.G31 (UPHY_TX18_P)
PCIe_{C5x8}.TX6-: J1.G30 (UPHY_TX18_N)
PCIe_{C5x8}.TX7+: J1.J30 (UPHY_TX19_P)
PCIe_{C5x8}.TX7-: J1.J31 (UPHY_TX19_N)
PCIe_{C5x8}.~CLKREQ: J1.C8 (PEX_C5_CLKREQ_N)
PCIe_{C5x8}.~RST: J1.H10 (PEX_C5_RST_N)
RGMII.MDC: J1.E6 (RGMII_SMA_MDC)
RGMII.MDIO: J1.E7 (RGMII_SMA_MDIO)
RGMII.RD0: J1.C4 (RGMII_RD0)
RGMII.RD1: J1.K6 (RGMII_RD1)
RGMII.RD2: J1.H6 (RGMII_RD2)
RGMII.RD3: J1.E5 (RGMII_RD3)
RGMII.RXC: J1.C5 (RGMII_RXC)
RGMII.RX_CTL: J1.D5 (RGMII_RX_CTL)
RGMII.TD0: J1.J6 (RGMII_TD0)
RGMII.TD1: J1.G5 (RGMII_TD1)
RGMII.TD2: J1.J7 (RGMII_TD2)
RGMII.TD3: J1.G6 (RGMII_TD3)
RGMII.TXC: J1.B5 (RGMII_TXC)
RGMII.TX_CTL: J1.K7 (RGMII_TX_CTL)
RGMII.~INT: J1.J5 (ENET_INT)
RGMII.~RST: J1.H5 (ENET_RST_N)
SFI.RX+: J1.B16 (UPHY_RX6_P)
SFI.RX-: J1.B17 (UPHY_RX6_N)
SFI.TX+: J1.K17 (UPHY_TX6_P)
SFI.TX-: J1.K16 (UPHY_TX6_N)
SFI_REFCLK+: J1.F28 (UPHY_REFCLK2_P), R2.2, R5.2
SFI_REFCLK-: J1.F29 (UPHY_REFCLK2_N), R3.2, R4.2
UPHY_REFCLK0_N: J1.E31 (UPHY_REFCLK0_N)
UPHY_REFCLK0_P: J1.E30 (UPHY_REFCLK0_P)
UPHY_REFCLK1_N: J1.E26 (UPHY_REFCLK1_N)
UPHY_REFCLK1_P: J1.E27 (UPHY_REFCLK1_P)
UPHY_REFCLK3_N: J1.F33 (UPHY_REFCLK3_N)
UPHY_REFCLK3_P: J1.F32 (UPHY_REFCLK3_P)
UPHY_REFCLK4_N: J1.C38 (UPHY_REFCLK4_N)
UPHY_REFCLK4_P: J1.C39 (UPHY_REFCLK4_P)
USB0_N: J1.F13 (USB0_N)
USB0_P: J1.F12 (USB0_P)
USB1.D+: J1.C11 (USB1_P)
USB1.D-: J1.C10 (USB1_N)
USB2_N: J1.A11 (USB2_N)
USB2_P: J1.A10 (USB2_P)
USB3_N: J1.G10 (USB3_N)
USB3_P: J1.G11 (USB3_P)
~PEX_WAKE: J1.A8 (PEX_WAKE_N)

Notes on the sheet:
Need to wire it on a root schematic
Needs to connect to USB M.2 key E
Connect to ~{PEWAKE} pins on M.2
MGBE reference clock
PCIe and USB3.0 SOM connections
