antmicro/jetson-agx-thor-baseboard/som_io.kicad_sch

## KiCad design som_io.kicad_sch (2026-02-19, an earlier design)

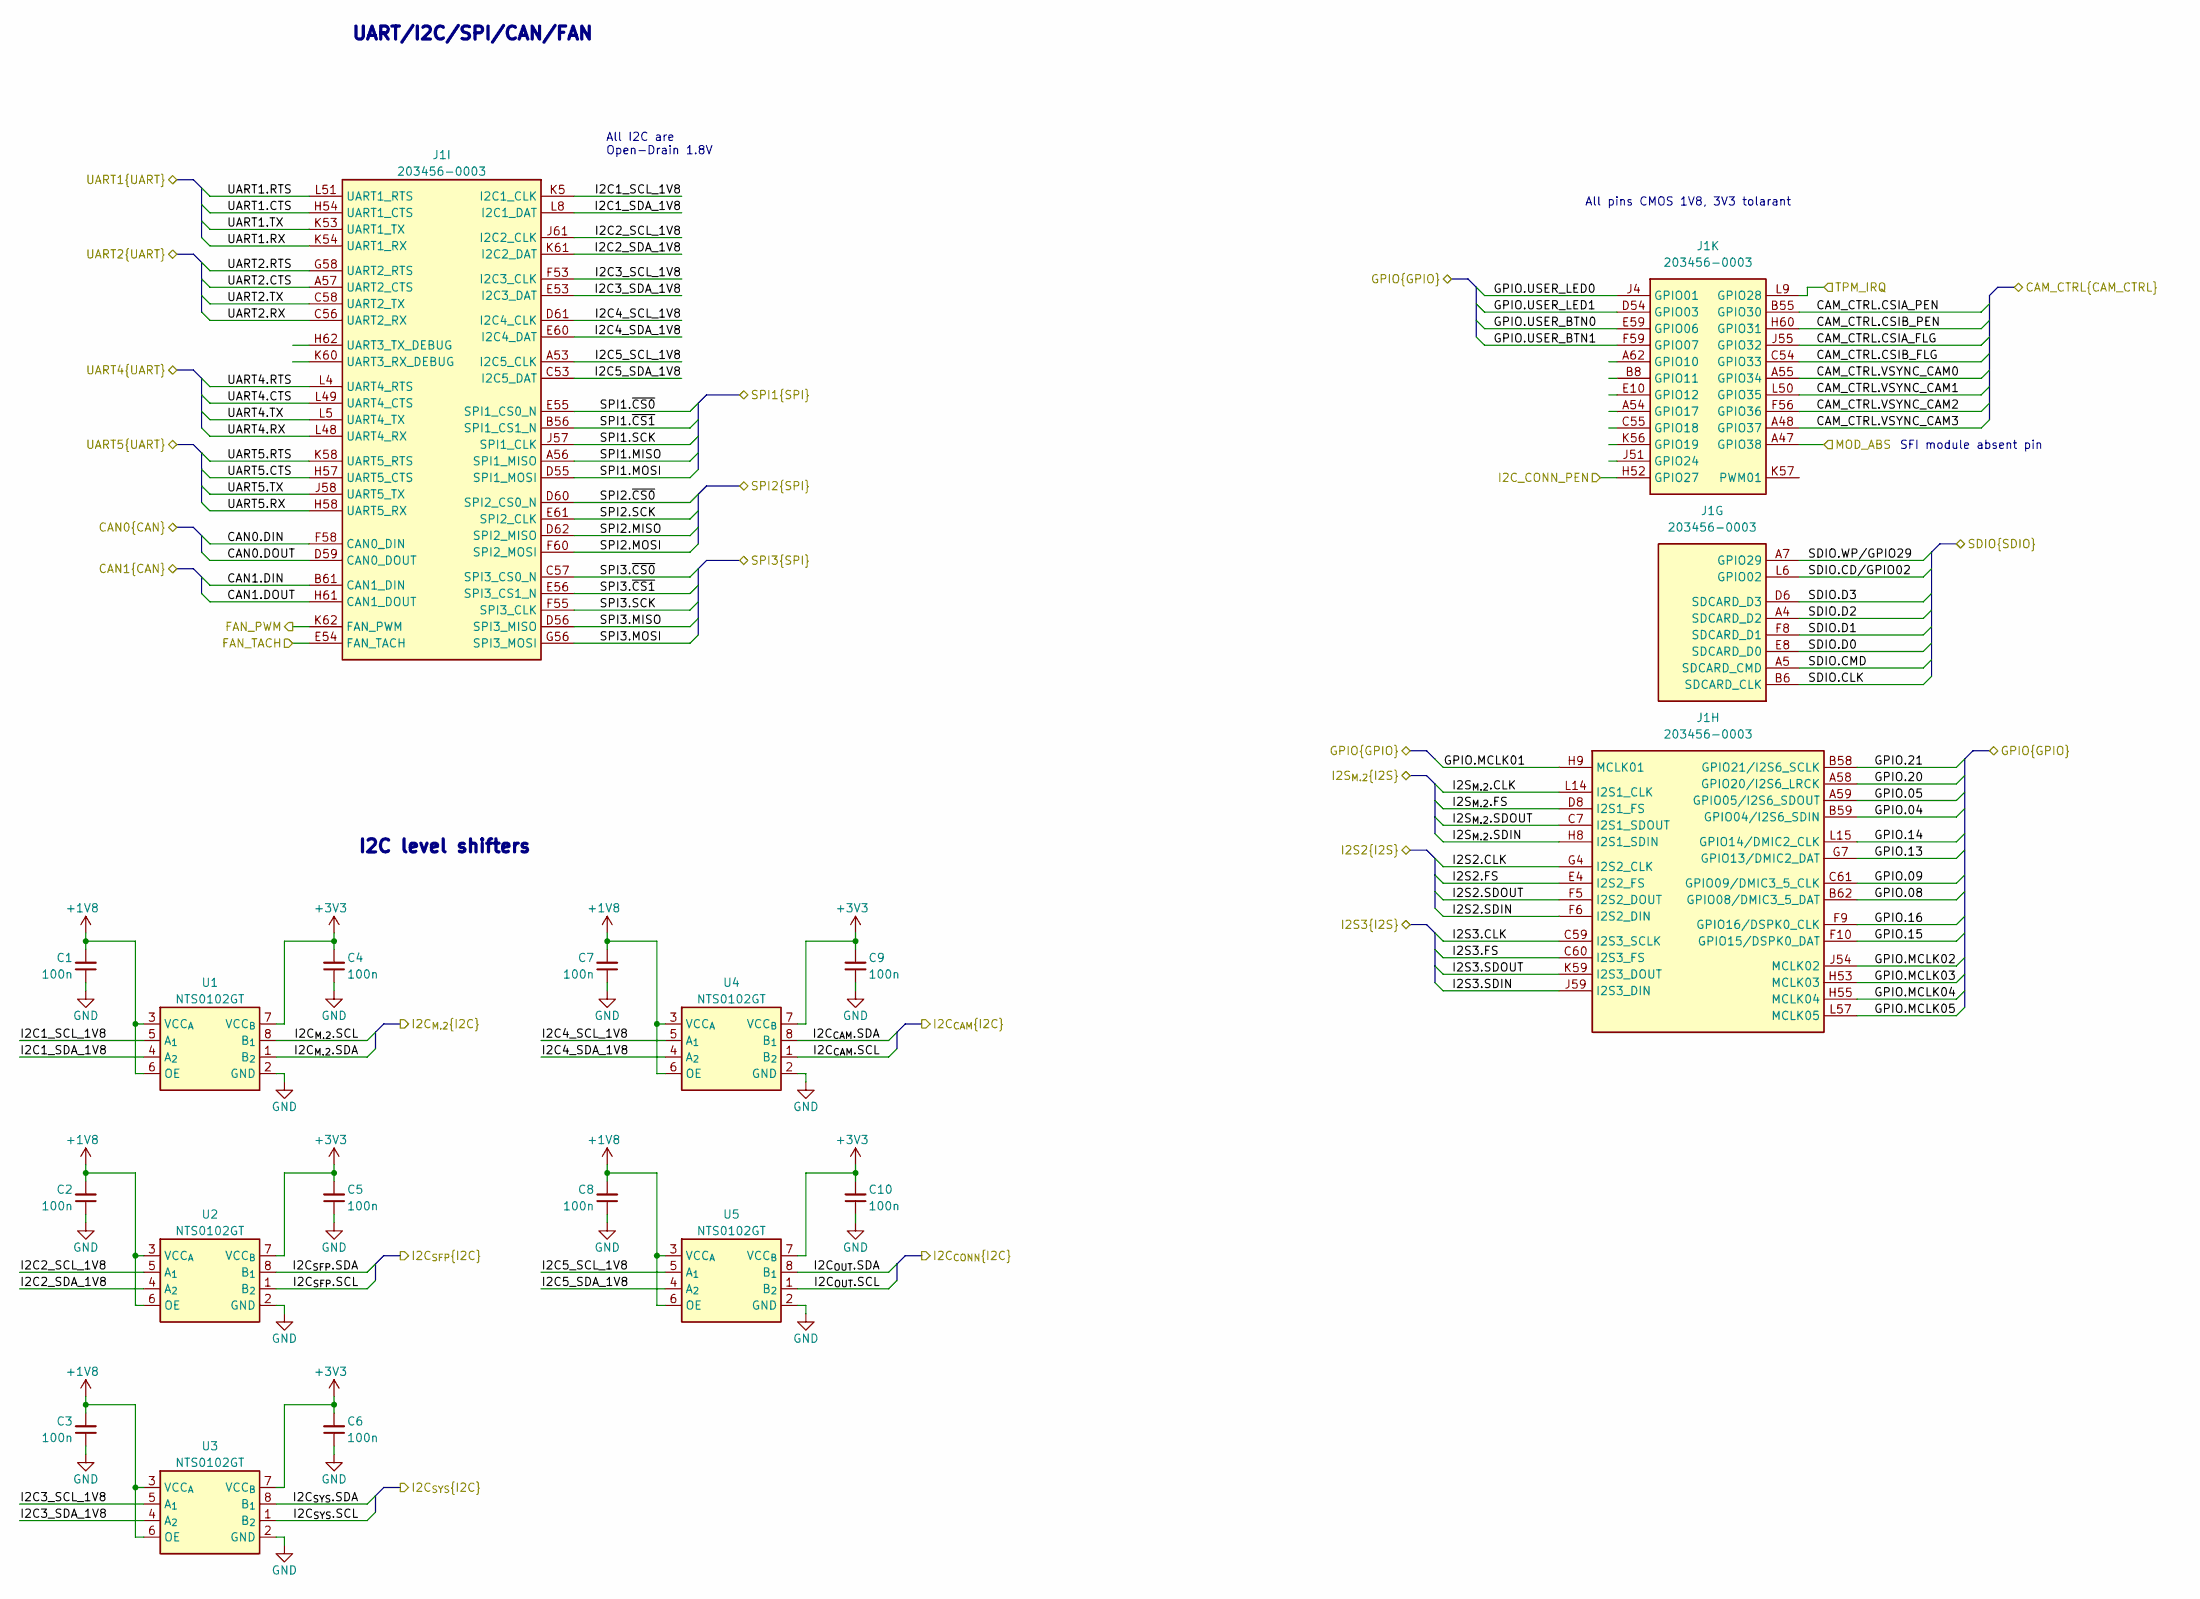
[picture p13: schematic som_io.kicad_sch]

Parts:
C1, C2, C3, C4, C5, C6, C7, C8, C9, C10: C_100n_0402; C_0402_1005Metric; Voltage 50V; MPN GRM155R61H104KE14D
J1: Hermaphroditic_Molex_203456-0003_CUSTOM_Jetson_Or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; Conn_Hermaphroditic_Molex_203456-0003_mirrored; MPN 203456-0003
U1, U2, U3, U4, U5: NTS0102_XSON; XSON-8_1x1.95mm_P0.5mm; MPN NTS0102GT

Connections:
+1V8: C1.2, C2.2, C3.2, C7.2, C8.2, U1.3 (VCC_{A}), U1.6 (OE), U2.3 (VCC_{A}), U2.6 (OE), U3.3 (VCC_{A}), U3.6 (OE), U4.3 (VCC_{A}), U4.6 (OE), U5.3 (VCC_{A}), U5.6 (OE)
+3V3: C4.2, C5.2, C6.2, C9.2, C10.2, U1.7 (VCC_{B}), U2.7 (VCC_{B}), U3.7 (VCC_{B}), U4.7 (VCC_{B}), U5.7 (VCC_{B})
CAM_CTRL.CSIA_FLG: J1.J55 (GPIO32)
CAM_CTRL.CSIA_PEN: J1.B55 (GPIO30)
CAM_CTRL.CSIB_FLG: J1.C54 (GPIO33)
CAM_CTRL.CSIB_PEN: J1.H60 (GPIO31)
CAM_CTRL.VSYNC_CAM0: J1.A55 (GPIO34)
CAM_CTRL.VSYNC_CAM1: J1.L50 (GPIO35)
CAM_CTRL.VSYNC_CAM2: J1.F56 (GPIO36)
CAM_CTRL.VSYNC_CAM3: J1.A48 (GPIO37)
CAN0.DIN: J1.F58 (CAN0_DIN)
CAN0.DOUT: J1.D59 (CAN0_DOUT)
CAN1.DIN: J1.B61 (CAN1_DIN)
CAN1.DOUT: J1.H61 (CAN1_DOUT)
FAN_PWM: J1.K62 (FAN_PWM)
FAN_TACH: J1.E54 (FAN_TACH)
GND: C1.1, C2.1, C3.1, C4.1, C5.1, C6.1, C7.1, C8.1, C9.1, C10.1, U1.2 (GND), U2.2 (GND), U3.2 (GND), U4.2 (GND), U5.2 (GND)
GPIO.04: J1.B59 (GPIO04/I2S6_SDIN)
GPIO.05: J1.A59 (GPIO05/I2S6_SDOUT)
GPIO.08: J1.B62 (GPIO08/DMIC3_5_DAT)
GPIO.09: J1.C61 (GPIO09/DMIC3_5_CLK)
GPIO.13: J1.G7 (GPIO13/DMIC2_DAT)
GPIO.14: J1.L15 (GPIO14/DMIC2_CLK)
GPIO.15: J1.F10 (GPIO15/DSPK0_DAT)
GPIO.16: J1.F9 (GPIO16/DSPK0_CLK)
GPIO.20: J1.A58 (GPIO20/I2S6_LRCK)
GPIO.21: J1.B58 (GPIO21/I2S6_SCLK)
GPIO.MCLK01: J1.H9 (MCLK01)
GPIO.MCLK02: J1.J54 (MCLK02)
GPIO.MCLK03: J1.H53 (MCLK03)
GPIO.MCLK04: J1.H55 (MCLK04)
GPIO.MCLK05: J1.L57 (MCLK05)
GPIO.USER_BTN0: J1.E59 (GPIO06)
GPIO.USER_BTN1: J1.F59 (GPIO07)
GPIO.USER_LED0: J1.J4 (GPIO01)
GPIO.USER_LED1: J1.D54 (GPIO03)
I2C1_SCL_1V8: J1.K5 (I2C1_CLK), U1.5 (A_{1})
I2C1_SDA_1V8: J1.L8 (I2C1_DAT), U1.4 (A_{2})
I2C2_SCL_1V8: J1.J61 (I2C2_CLK), U2.5 (A_{1})
I2C2_SDA_1V8: J1.K61 (I2C2_DAT), U2.4 (A_{2})
I2C3_SCL_1V8: J1.F53 (I2C3_CLK), U3.5 (A_{1})
I2C3_SDA_1V8: J1.E53 (I2C3_DAT), U3.4 (A_{2})
I2C4_SCL_1V8: J1.D61 (I2C4_CLK), U4.5 (A_{1})
I2C4_SDA_1V8: J1.E60 (I2C4_DAT), U4.4 (A_{2})
I2C5_SCL_1V8: J1.A53 (I2C5_CLK), U5.5 (A_{1})
I2C5_SDA_1V8: J1.C53 (I2C5_DAT), U5.4 (A_{2})
I2C_CONN_PEN: J1.H52 (GPIO27)
I2C_{CAM}.SCL: U4.1 (B_{2})
I2C_{CAM}.SDA: U4.8 (B_{1})
I2C_{M.2}.SCL: U1.8 (B_{1})
I2C_{M.2}.SDA: U1.1 (B_{2})
I2C_{OUT}.SCL: U5.1 (B_{2})
I2C_{OUT}.SDA: U5.8 (B_{1})
I2C_{SFP}.SCL: U2.1 (B_{2})
I2C_{SFP}.SDA: U2.8 (B_{1})
I2C_{SYS}.SCL: U3.1 (B_{2})
I2C_{SYS}.SDA: U3.8 (B_{1})
I2S2.CLK: J1.G4 (I2S2_CLK)
I2S2.FS: J1.E4 (I2S2_FS)
I2S2.SDIN: J1.F6 (I2S2_DIN)
I2S2.SDOUT: J1.F5 (I2S2_DOUT)
I2S3.CLK: J1.C59 (I2S3_SCLK)
I2S3.FS: J1.C60 (I2S3_FS)
I2S3.SDIN: J1.J59 (I2S3_DIN)
I2S3.SDOUT: J1.K59 (I2S3_DOUT)
I2S_{M.2}.CLK: J1.L14 (I2S1_CLK)
I2S_{M.2}.FS: J1.D8 (I2S1_FS)
I2S_{M.2}.SDIN: J1.H8 (I2S1_SDIN)
I2S_{M.2}.SDOUT: J1.C7 (I2S1_SDOUT)
MOD_ABS: J1.A47 (GPIO38)
SDIO.CD/GPIO02: J1.L6 (GPIO02)
SDIO.CLK: J1.B6 (SDCARD_CLK)
SDIO.CMD: J1.A5 (SDCARD_CMD)
SDIO.D0: J1.E8 (SDCARD_D0)
SDIO.D1: J1.F8 (SDCARD_D1)
SDIO.D2: J1.A4 (SDCARD_D2)
SDIO.D3: J1.D6 (SDCARD_D3)
SDIO.WP/GPIO29: J1.A7 (GPIO29)
SPI1.MISO: J1.A56 (SPI1_MISO)
SPI1.MOSI: J1.D55 (SPI1_MOSI)
SPI1.SCK: J1.J57 (SPI1_CLK)
SPI1.~CS0: J1.E55 (SPI1_CS0_N)
SPI1.~CS1: J1.B56 (SPI1_CS1_N)
SPI2.MISO: J1.D62 (SPI2_MISO)
SPI2.MOSI: J1.F60 (SPI2_MOSI)
SPI2.SCK: J1.E61 (SPI2_CLK)
SPI2.~CS0: J1.D60 (SPI2_CS0_N)
SPI3.MISO: J1.D56 (SPI3_MISO)
SPI3.MOSI: J1.G56 (SPI3_MOSI)
SPI3.SCK: J1.F55 (SPI3_CLK)
SPI3.~CS0: J1.C57 (SPI3_CS0_N)
SPI3.~CS1: J1.E56 (SPI3_CS1_N)
TPM_IRQ: J1.L9 (GPIO28)
UART1.CTS: J1.H54 (UART1_CTS)
UART1.RTS: J1.L51 (UART1_RTS)
UART1.RX: J1.K54 (UART1_RX)
UART1.TX: J1.K53 (UART1_TX)
UART2.CTS: J1.A57 (UART2_CTS)
UART2.RTS: J1.G58 (UART2_RTS)
UART2.RX: J1.C56 (UART2_RX)
UART2.TX: J1.C58 (UART2_TX)
UART4.CTS: J1.L49 (UART4_CTS)
UART4.RTS: J1.L4 (UART4_RTS)
UART4.RX: J1.L48 (UART4_RX)
UART4.TX: J1.L5 (UART4_TX)
UART5.CTS: J1.H57 (UART5_CTS)
UART5.RTS: J1.K58 (UART5_RTS)
UART5.RX: J1.H58 (UART5_RX)
UART5.TX: J1.J58 (UART5_TX)

Notes on the sheet:
All I2C are Open-Drain 1.8V
SFI module absent pin
I2C level shifters
All pins CMOS 1V8, 3V3 tolarant
UART/I2C/SPI/CAN/FAN
