antmicro/jetson-agx-thor-baseboard/usb_debug_pd.kicad_sch

## KiCad design usb_debug_pd.kicad_sch (2026-03-19, an earlier design)

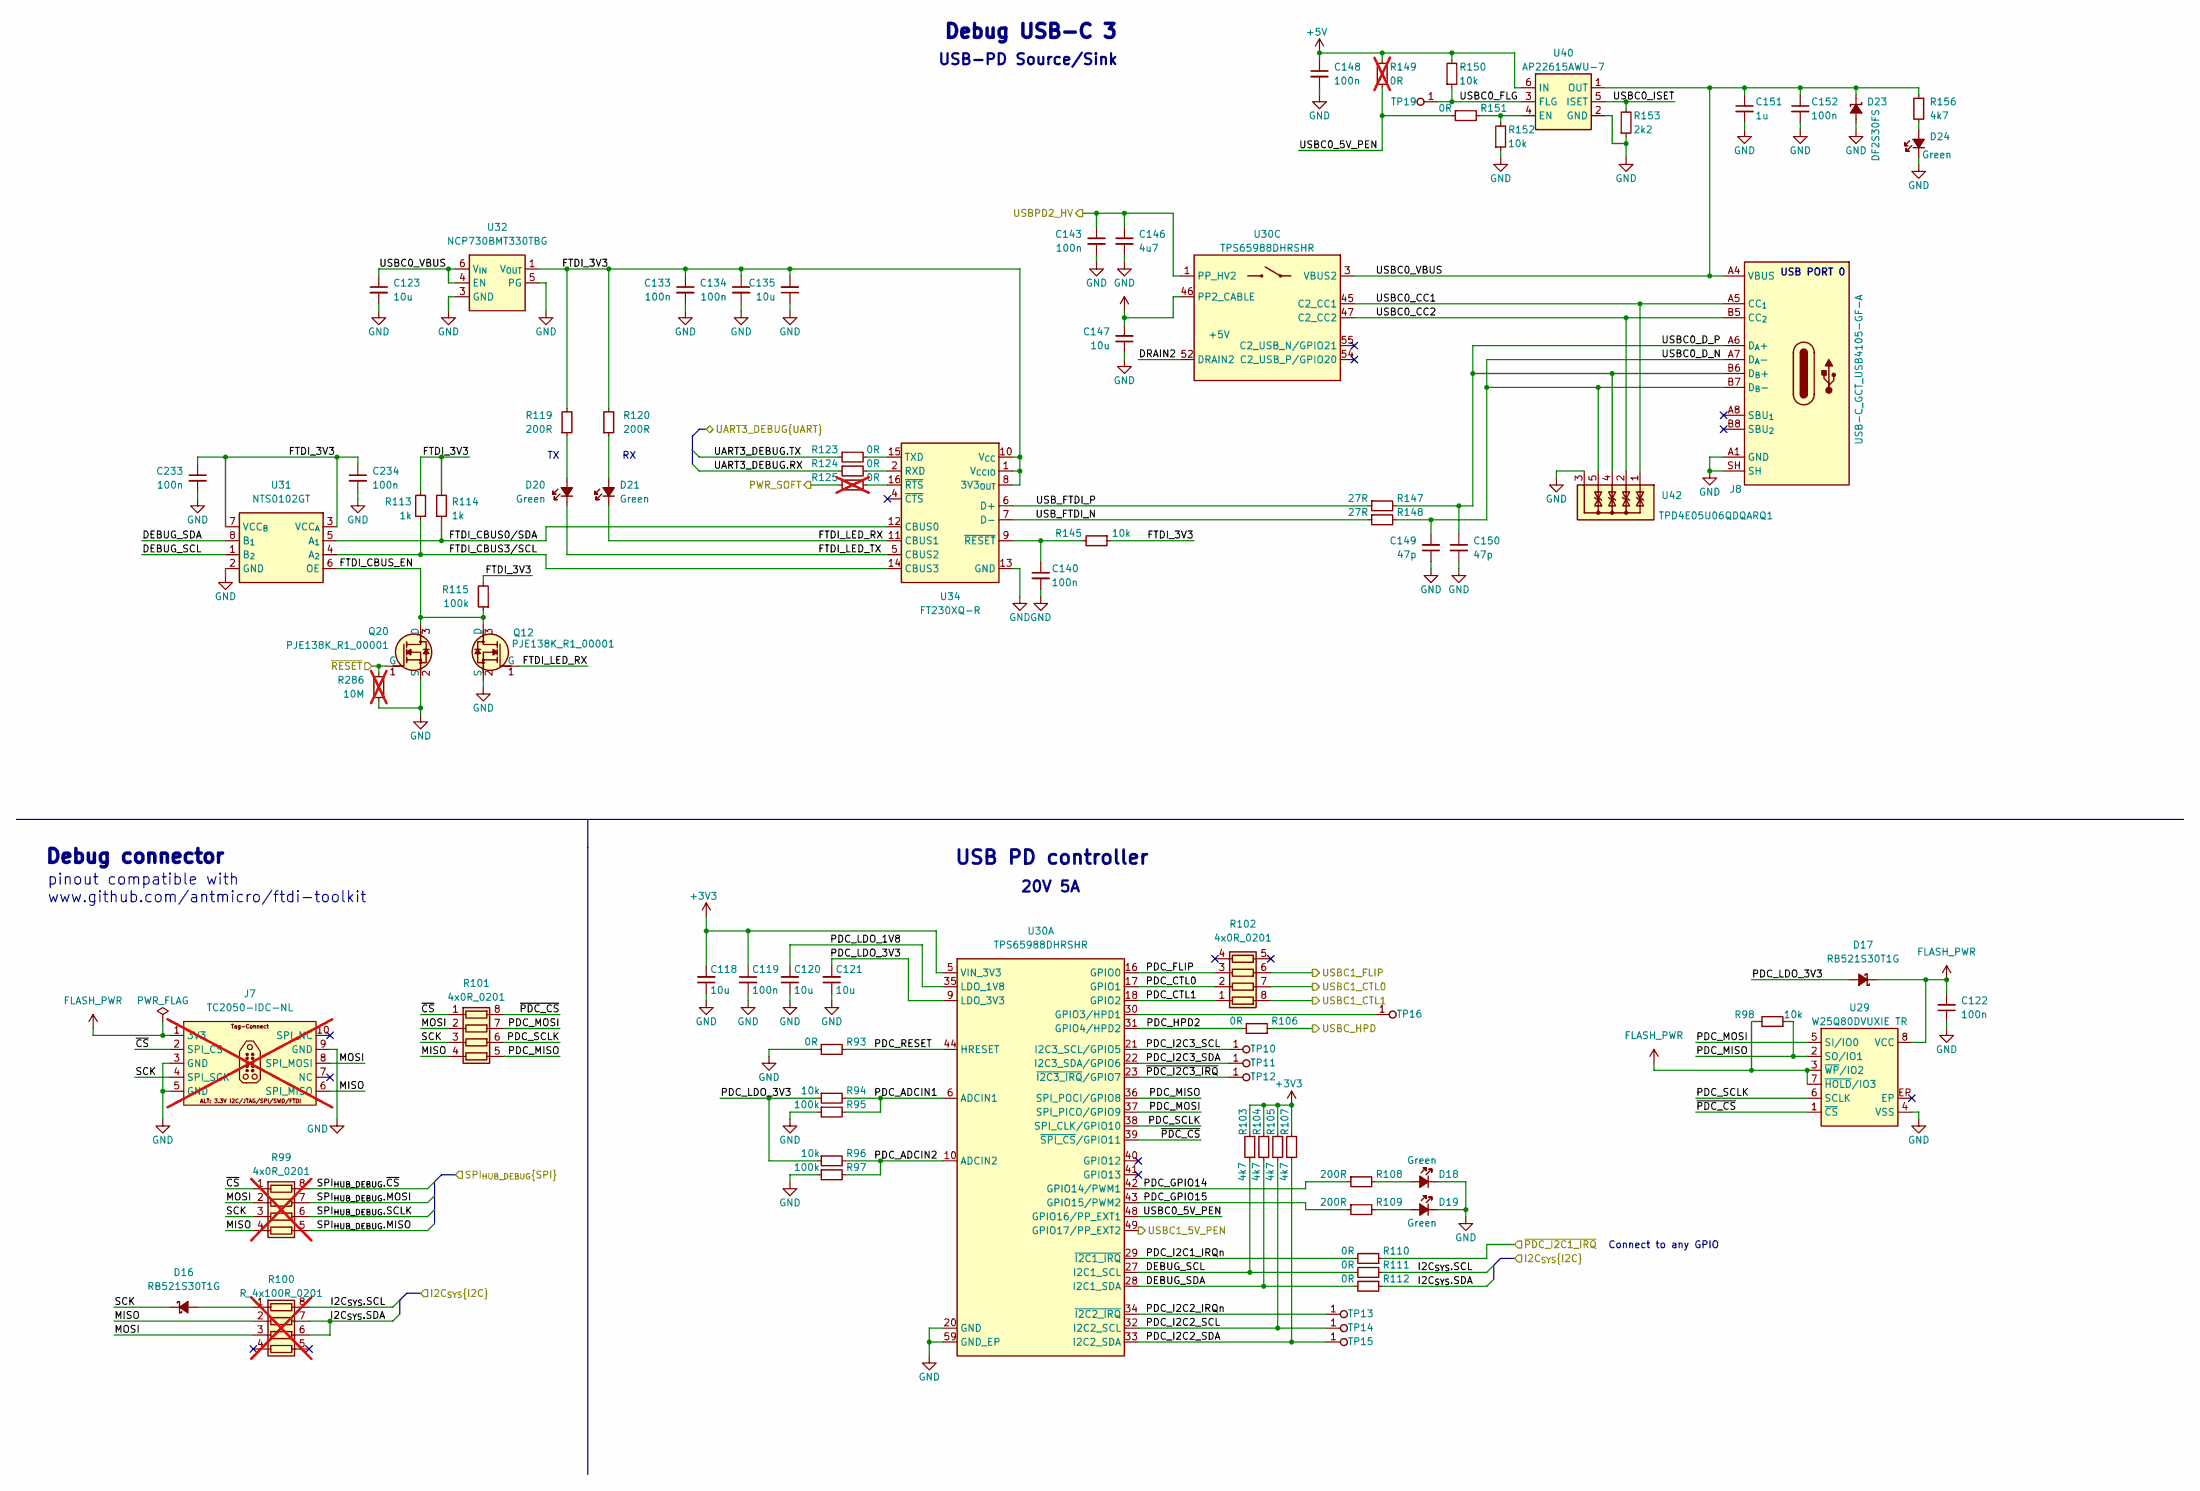
[picture p15: schematic usb_debug_pd.kicad_sch]

Parts:
C118, C120, C121, C135, C147: C_10u_0402; C_0402_1005Metric; MPN CC0402MRX5R5BB106
C119, C122, C133, C134, C140, C143, C148, C152, C233, C234: C_100n_0402; C_0402_1005Metric; Voltage 50V; MPN GRM155R61H104KE14D
C123: C_10u_25V_0603; C_0603_1608Metric; Voltage 25V; MPN C1608X5R1E106M080AC
C146: C_4u7_25V_0402; C_0402_1005Metric; Voltage 25V; MPN GRM155C61E475ME15J
C149, C150: C_47p_0402; C_0402_1005Metric; MPN C0402C470J5GACTU
C151: C_1u_25V_0402; C_0402_1005Metric; Voltage 25V; MPN GRM155R61E105KE11J
D16, D17: RB521S30T1G; SOD-523; MPN RB521S30T1G
D18, D19, D20, D21, D24: LED_G_0603_LTST-C190GKT; LED_0603_1608Metric_G; MPN LTST-C190GKT
D23: DF2S30FS_SOD; SOD-923; MPN DF2S30FS
J7: Tag-Connect_TC2050-IDC-NL_2x5_P1.27mm; MPN TC2050-IDC-NL; not fitted
J8: USB-C_GCT_USB4105-GF-A; USB-C_Receptacle_GCT_USB4105-GF-A; MPN USB4105-GF-A
Q12, Q20: PJE138K; SOT-523; MPN PJE138K_R1_00001
R93, R106, R110, R111, R112, R123, R124, R151: R_0R_0402; R_0402_1005Metric; MPN ERJ2GE0R00X
R94, R96, R98, R145, R150, R152: R_10k_0402; R_0402_1005Metric; Tolerance 1%; MPN CR0402-FX-1002GLF
R95, R97, R115: R_100k_0402; R_0402_1005Metric; Tolerance 1%; MPN CR0402-FX-1003GLF
R99: R_4x0R_0201_array; R_Array_4x0201_Panasonic_EXB18V; MPN EXB-18VR000X; not fitted
R100: R_4x100R_0201_array; R_Array_4x0201_Panasonic_EXB18V; MPN EXB-18V101JX; not fitted
R101, R102: R_4x0R_0201_array; R_Array_4x0201_Panasonic_EXB18V; MPN EXB-18VR000X
R103, R104, R105, R107, R156: R_4k7_0402; R_0402_1005Metric; Tolerance 1%; MPN CR0402-FX-4701GLF
R108, R109, R119, R120: R_200R_0402; R_0402_1005Metric; Tolerance 1%; MPN CR0402-FX-2000GLF
R113, R114: R_1k_0402; R_0402_1005Metric; Tolerance 1%; MPN CR0402-FX-1001GLF
R125, R149: R_0R_0402; R_0402_1005Metric; MPN ERJ2GE0R00X; not fitted
R147, R148: R_27R_0402; R_0402_1005Metric; Tolerance 1%; MPN CR0402-FX-27R0GLF
R153: R_2k2_0402; R_0402_1005Metric; Tolerance 1%; MPN CR0402-FX-2201GLF
R286: R_10M_0402; R_0402_1005Metric; Tolerance 1%; MPN CR0402-FX-1005GLF; not fitted
TP10, TP11, TP12, TP13, TP14, TP15, TP16, TP19: TP_0.75mm_SMD; TP_SMD_0.75mm
U29: W25Q80DV_USON; USON-8_2x3mm_P0.5mm; MPN W25Q80DVUXIE TR
U30: TPS65988DHRSHR; IC_TPS65987DDHRSHR; MPN TPS65988DHRSHR
U31: NTS0102_XSON; XSON-8_1x1.95mm_P0.5mm; MPN NTS0102GT
U32: NCP730BMT330_WSON; WSON-6-1EP_2x2mm_P0.65mm; MPN NCP730BMT330TBG
U34: FT230X_QFN; QFN-16-1EP_4x4mm_P0.65mm; MPN FT230XQ-R
U40: AP22615A_TSOT26; TSOT23-6; MPN AP22615AWU-7
U42: TPD4E05U06QDQARQ1; USON-10_2.5x1mm_P0.5mm; MPN TPD4E05U06QDQARQ1

Connections:
+3V3: C118.2, C119.1, R103.1, R104.1, R105.1, R107.1, U30.5 (VIN_3V3)
+5V: C147.2, C148.1, R149.2, R150.2, U30.46 (PP2_CABLE), U40.6 (IN)
DEBUG_SCL: R103.2, R111.2, U30.27 (I2C1_SCL), U31.1 (B_{2})
DEBUG_SDA: R104.2, R112.2, U30.28 (I2C1_SDA), U31.8 (B_{1})
DRAIN2: U30.7 (DRAIN2), U30.52 (DRAIN2), U30.56 (DRAIN2), U30.57 (DRAIN2)
FLASH_PWR: C122.2, D17.1 (C), J7.1, R98.2, U29.3 (~WP/IO2), U29.7 (~HOLD/IO3), U29.8 (VCC)
FTDI_3V3: C133.1, C134.1, C135.2, C233.1, C234.1, R113.2, R114.2, R115.2, R119.2, R120.2, R145.1, U31.3 (VCC_{A}), U31.7 (VCC_{B}), U32.1 (V_{OUT}), U34.1 (V_{CCIO}), U34.8 (3V3_{OUT}), U34.10 (V_{CC})
FTDI_CBUS0/SDA: R114.1, U31.5 (A_{1}), U34.12 (CBUS0)
FTDI_CBUS3/SCL: R113.1, U31.4 (A_{2}), U34.14 (CBUS3)
FTDI_CBUS_EN: Q12.3 (D), Q20.3 (D), R115.1, U31.6 (OE)
FTDI_LED_RX: D21.1 (C), Q12.1 (G), U34.11 (CBUS1)
FTDI_LED_TX: D20.1 (C), U34.5 (CBUS2)
GND: C118.1, C119.2, C120.1, C121.1, C122.1, C123.2, C133.2, C134.2, C135.1, C140.2, C143.2, C146.2, C147.1, C148.2, C149.1, C150.2, C151.2, C152.2, C233.2, C234.2, D18.1 (C), D19.1 (C), D23.2 (A), D24.1 (C), J7.3, J7.5, J7.9, J8.A1 (GND), J8.A12 (GND), J8.B1 (GND), J8.B12 (GND), J8.SH, Q12.2 (S), Q20.2 (S), R93.1, R95.1, R97.1, R152.1, R153.1, R286.1, U29.4 (VSS), U30.20 (GND), U30.51 (GND), U30.59 (GND_EP), U31.2 (GND), U32.3 (GND), U32.5 (PG), U32.7 (GND), U34.3 (GND), U34.13 (GND), U34.17 (GND), U40.2 (GND), U42.3, U42.8
I2C_{SYS}.SCL: R100.8 (R1.2), R111.1
I2C_{SYS}.SDA: R100.6 (R3.2), R100.7 (R2.2), R112.1
MISO: J7.6, R99.4 (R4.1), R100.2 (R2.1), R101.4 (R4.1)
MOSI: J7.8, R99.2 (R2.1), R100.3 (R3.1), R101.2 (R2.1)
unnamed: C140.1, R145.2, U34.9 (~RESET)
unnamed: D16.2 (A), R100.1 (R1.1)
unnamed: D18.2 (A), R108.2
unnamed: D19.2 (A), R109.2
unnamed: D20.2 (A), R119.1
unnamed: D21.2 (A), R120.1
unnamed: D24.2 (A), R156.2
unnamed: R123.2, U34.15 (TXD)
unnamed: R124.2, U34.2 (RXD)
unnamed: R125.2, U34.16 (~RTS)
unnamed: R151.2, R152.2, U40.4 (EN)
unnamed: TP16.1, U30.30 (GPIO3/HPD1)
PDC_ADCIN1: R94.2, R95.2, U30.6 (ADCIN1)
PDC_ADCIN2: R96.2, R97.2, U30.10 (ADCIN2)
PDC_CTL0: R102.2 (R2.1), U30.17 (GPIO1)
PDC_CTL1: R102.1 (R1.1), U30.18 (GPIO2)
PDC_FLIP: R102.3 (R3.1), U30.16 (GPIO0)
PDC_GPIO14: R108.1, U30.42 (GPIO14/PWM1)
PDC_GPIO15: R109.1, U30.43 (GPIO15/PWM2)
PDC_HPD2: R106.2, U30.31 (GPIO4/HPD2)
PDC_I2C1_IRQn: R110.2, U30.29 (~I2C1_IRQ)
PDC_I2C2_IRQn: TP13.1, U30.34 (~I2C2_IRQ)
PDC_I2C2_SCL: R105.2, TP14.1, U30.32 (I2C2_SCL)
PDC_I2C2_SDA: R107.2, TP15.1, U30.33 (I2C2_SDA)
PDC_I2C3_SCL: TP10.1, U30.21 (I2C3_SCL/GPIO5)
PDC_I2C3_SDA: TP11.1, U30.22 (I2C3_SDA/GPIO6)
PDC_LDO_1V8: C120.2, U30.35 (LDO_1V8)
PDC_LDO_3V3: C121.2, D17.2 (A), R94.1, R96.1, U30.9 (LDO_3V3)
PDC_MISO: R98.1, R101.5 (R4.2), U29.2 (SO/IO1), U30.36 (SPI_POCI/GPIO8)
PDC_MOSI: R101.7 (R2.2), U29.5 (SI/IO0), U30.37 (SPI_PICO/GPIO9)
PDC_RESET: R93.2, U30.44 (HRESET)
PDC_SCLK: R101.6 (R3.2), U29.6 (SCLK), U30.38 (SPI_CLK/GPIO10)
PWR_SOFT: R125.1
SCK: D16.1 (C), J7.4, R99.3 (R3.1), R101.3 (R3.1)
SPI_{HUB_DEBUG}.MISO: R99.5 (R4.2)
SPI_{HUB_DEBUG}.MOSI: R99.7 (R2.2)
SPI_{HUB_DEBUG}.SCLK: R99.6 (R3.2)
SPI_{HUB_DEBUG}.~CS: R99.8 (R1.2)
UART3_DEBUG.RX: R124.1
UART3_DEBUG.TX: R123.1
USBC0_5V_PEN: R149.1, R151.1, U30.48 (GPIO16/PP_EXT1)
USBC0_CC1: J8.A5 (CC_{1}), U30.45 (C2_CC1), U42.1, U42.10
USBC0_CC2: J8.B5 (CC_{2}), U30.47 (C2_CC2), U42.2, U42.9
USBC0_D_N: C149.2, J8.A7 (D_{A}-), J8.B7 (D_{B}-), R148.2, U42.5, U42.6
USBC0_D_P: C150.1, J8.A6 (D_{A}+), J8.B6 (D_{B}+), R147.2, U42.4, U42.7
USBC0_FLG: R150.1, TP19.1, U40.3 (FLG)
USBC0_ISET: R153.2, U40.5 (ISET)
USBC0_VBUS: C123.1, C151.1, C152.1, D23.1 (C), J8.A4 (VBUS), J8.A9 (VBUS), J8.B4 (VBUS), J8.B9 (VBUS), R156.1, U30.3 (VBUS2), U32.4 (EN), U32.6 (V_{IN}), U40.1 (OUT)
USBC1_5V_PEN: U30.49 (GPIO17/PP_EXT2)
USBC1_CTL0: R102.7 (R2.2)
USBC1_CTL1: R102.8 (R1.2)
USBC1_FLIP: R102.6 (R3.2)
USBC_HPD: R106.1
USBPD2_HV: C143.1, C146.1, U30.1 (PP_HV2)
USB_FTDI_N: R148.1, U34.7 (D-)
USB_FTDI_P: R147.1, U34.6 (D+)
~CS: J7.2, R99.1 (R1.1), R101.1 (R1.1)
~PDC_CS: R101.8 (R1.2), U29.1 (~CS), U30.39 (~SPI_CS/GPIO11)
~PDC_I2C1_IRQ: R110.1
~PDC_I2C3_IRQ: TP12.1, U30.23 (~I2C3_IRQ/GPIO7)
~RESET: Q20.1 (G), R286.2

Notes on the sheet:
Debug USB-C 3
USB PORT 0
pinout compatible with www.github.com/antmicro/ftdi-toolkit
USB PD controller
Debug connector
Connect to any GPIO
USB-PD Source/Sink
20V 5A
