antmicro/jetson-agx-thor-baseboard/usb_dp.kicad_sch

## KiCad design usb_dp.kicad_sch (2026-03-19, an earlier design)

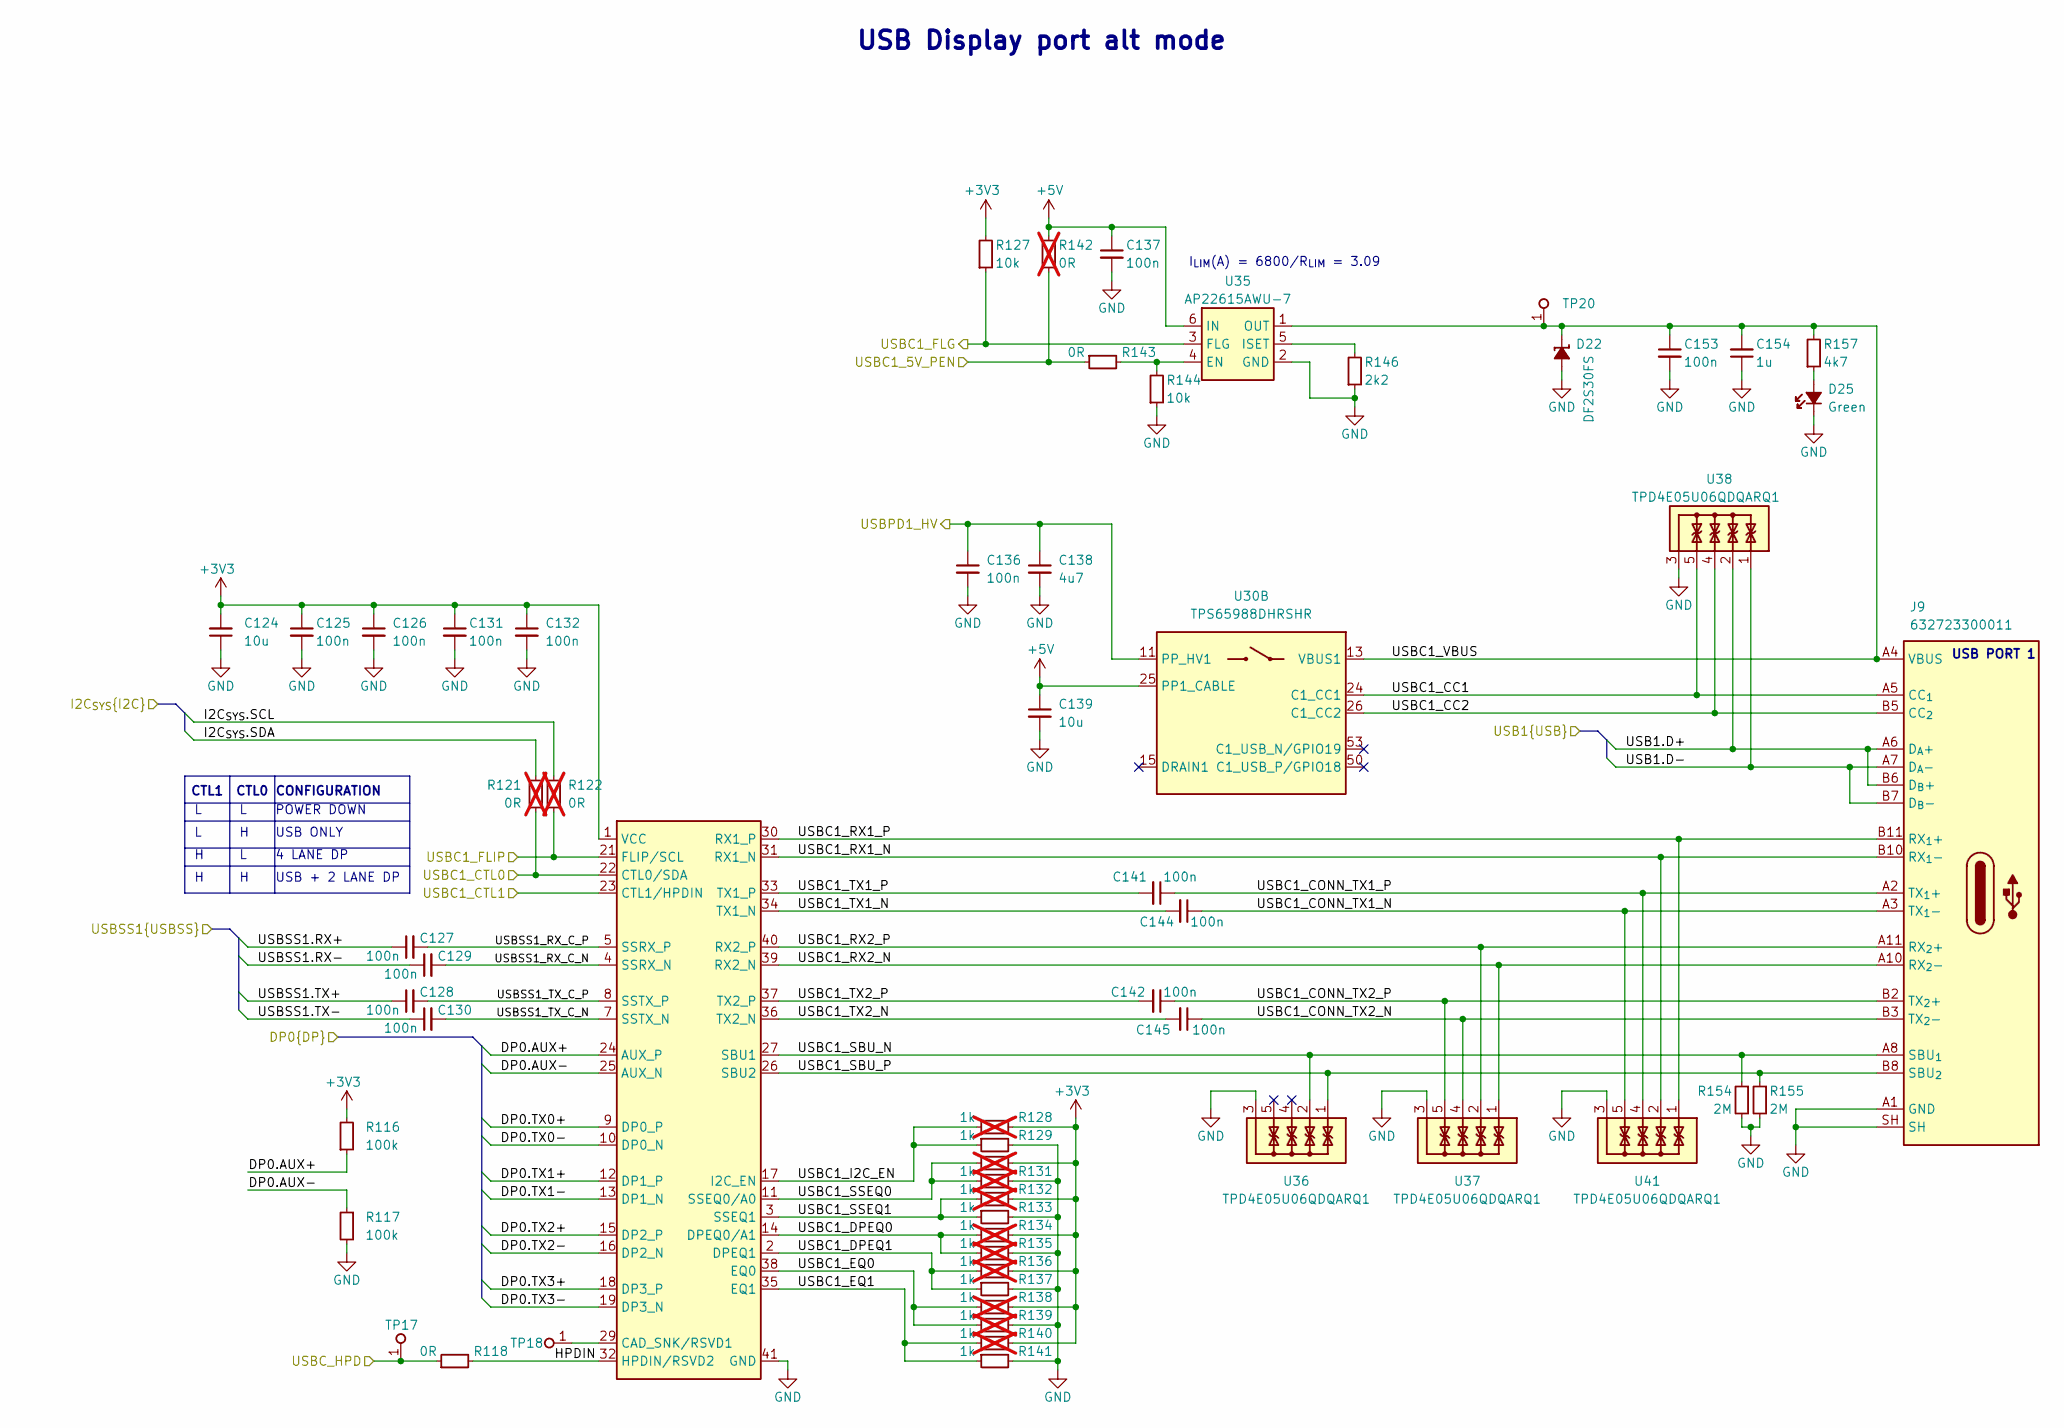
[picture p16: schematic usb_dp.kicad_sch]

Parts:
C124, C139: C_10u_0402; C_0402_1005Metric; MPN CC0402MRX5R5BB106
C125, C126, C127, C128, C129, C130, C131, C132, C136, C137, C153: C_100n_0402; C_0402_1005Metric; Voltage 50V; MPN GRM155R61H104KE14D
C138: C_4u7_25V_0402; C_0402_1005Metric; Voltage 25V; MPN GRM155C61E475ME15J
C141, C142, C144, C145: C_100n_0201; C_0201; MPN CC0201KRX6S5BB104
C154: C_1u_25V_0402; C_0402_1005Metric; Voltage 25V; MPN GRM155R61E105KE11J
D22: DF2S30FS_SOD; SOD-923; MPN DF2S30FS
D25: LED_G_0603_LTST-C190GKT; LED_0603_1608Metric_G; MPN LTST-C190GKT
J9: USB-C_WE_632723300011; USB-C_Receptacle_WE_632723300011; MPN 632723300011
R116, R117: R_100k_0402; R_0402_1005Metric; Tolerance 1%; MPN CR0402-FX-1003GLF
R118, R143: R_0R_0402; R_0402_1005Metric; MPN ERJ2GE0R00X
R121, R122, R142: R_0R_0402; R_0402_1005Metric; MPN ERJ2GE0R00X; not fitted
R127, R144: R_10k_0402; R_0402_1005Metric; Tolerance 1%; MPN CR0402-FX-1002GLF
R128, R130, R131, R132, R134, R135, R136, R138, R139, R140: R_1k_0402; R_0402_1005Metric; Tolerance 1%; MPN CR0402-FX-1001GLF; not fitted
R129, R133, R137, R141: R_1k_0402; R_0402_1005Metric; Tolerance 1%; MPN CR0402-FX-1001GLF
R146: R_2k2_0402; R_0402_1005Metric; Tolerance 1%; MPN CR0402-FX-2201GLF
R154, R155: R_2M_0402; R_0402_1005Metric; Tolerance 1%; MPN RC0402FR-072ML
R157: R_4k7_0402; R_0402_1005Metric; Tolerance 1%; MPN CR0402-FX-4701GLF
TP17, TP18, TP20: TP_0.75mm_SMD; TP_SMD_0.75mm
U30: TPS65988DHRSHR; IC_TPS65987DDHRSHR; MPN TPS65988DHRSHR
U33: TUSB1046-DCIRNQ; WQFN-40_1EP_6x3mm_Pitch0.4mm_EP4.7x2.7mm; MPN TUSB1046-DCIRNQT
U35: AP22615A_TSOT26; TSOT23-6; MPN AP22615AWU-7
U36, U37, U38, U41: TPD4E05U06QDQARQ1; USON-10_2.5x1mm_P0.5mm; MPN TPD4E05U06QDQARQ1

Connections:
+3V3: C124.2, C125.1, C126.1, C131.1, C132.1, R116.2, R127.2, R128.2, R130.2, R132.2, R134.2, R136.2, R138.2, R140.2, U33.1 (VCC), U33.6 (VCC), U33.20 (VCC), U33.28 (VCC)
+5V: C137.1, C139.1, R142.2, U30.25 (PP1_CABLE), U35.6 (IN)
DP0.AUX+: R116.1, U33.24 (AUX_P)
DP0.AUX-: R117.1, U33.25 (AUX_N)
DP0.TX0+: U33.9 (DP0_P)
DP0.TX0-: U33.10 (DP0_N)
DP0.TX1+: U33.12 (DP1_P)
DP0.TX1-: U33.13 (DP1_N)
DP0.TX2+: U33.15 (DP2_P)
DP0.TX2-: U33.16 (DP2_N)
DP0.TX3+: U33.18 (DP3_P)
DP0.TX3-: U33.19 (DP3_N)
GND: C124.1, C125.2, C126.2, C131.2, C132.2, C136.2, C137.2, C138.2, C139.2, C153.2, C154.1, D22.2 (A), D25.1 (C), J9.A1 (GND), J9.A12 (GND), J9.B1 (GND), J9.B12 (GND), J9.SH, R117.2, R129.2, R131.2, R133.2, R135.2, R137.2, R139.2, R141.2, R144.1, R146.1, R154.2, R155.2, U33.41 (GND), U35.2 (GND), U36.3, U36.8, U37.3, U37.8, U38.3, U38.8, U41.3, U41.8
HPDIN: R118.2, U33.32 (HPDIN/RSVD2)
I2C_{SYS}.SCL: R122.2
I2C_{SYS}.SDA: R121.2
unnamed: D25.2 (A), R157.1
unnamed: R143.2, R144.2, U35.4 (EN)
unnamed: R146.2, U35.5 (ISET)
unnamed: TP18.1, U33.29 (CAD_SNK/RSVD1)
unnamed: U30.8 (DRAIN1), U30.15 (DRAIN1), U30.19 (DRAIN1), U30.58 (DRAIN1)
unnamed: U36.4, U36.7
unnamed: U36.5, U36.6
USB1.D+: J9.A6 (D_{A}+), J9.B6 (D_{B}+), U38.2, U38.9
USB1.D-: J9.A7 (D_{A}-), J9.B7 (D_{B}-), U38.1, U38.10
USBC1_5V_PEN: R142.1, R143.1
USBC1_CC1: J9.A5 (CC_{1}), U30.24 (C1_CC1), U38.5, U38.6
USBC1_CC2: J9.B5 (CC_{2}), U30.26 (C1_CC2), U38.4, U38.7
USBC1_CONN_TX1_N: C144.1, J9.A3 (TX_{1}-), U41.5, U41.6
USBC1_CONN_TX1_P: C141.1, J9.A2 (TX_{1}+), U41.4, U41.7
USBC1_CONN_TX2_N: C145.1, J9.B3 (TX_{2}-), U37.4, U37.7
USBC1_CONN_TX2_P: C142.1, J9.B2 (TX_{2}+), U37.5, U37.6
USBC1_CTL0: R121.1, U33.22 (CTL0/SDA)
USBC1_CTL1: U33.23 (CTL1/HPDIN)
USBC1_DPEQ0: R134.1, R135.1, U33.14 (DPEQ0/A1)
USBC1_DPEQ1: R136.1, R137.1, U33.2 (DPEQ1)
USBC1_EQ0: R138.1, R139.1, U33.38 (EQ0)
USBC1_EQ1: R140.1, R141.1, U33.35 (EQ1)
USBC1_FLG: R127.1, U35.3 (FLG)
USBC1_FLIP: R122.1, U33.21 (FLIP/SCL)
USBC1_I2C_EN: R128.1, R129.1, U33.17 (I2C_EN)
USBC1_RX1_N: J9.B10 (RX_{1}-), U33.31 (RX1_N), U41.2, U41.9
USBC1_RX1_P: J9.B11 (RX_{1}+), U33.30 (RX1_P), U41.1, U41.10
USBC1_RX2_N: J9.A10 (RX_{2}-), U33.39 (RX2_N), U37.1, U37.10
USBC1_RX2_P: J9.A11 (RX_{2}+), U33.40 (RX2_P), U37.2, U37.9
USBC1_SBU_N: J9.A8 (SBU_{1}), R154.1, U33.27 (SBU1), U36.2, U36.9
USBC1_SBU_P: J9.B8 (SBU_{2}), R155.1, U33.26 (SBU2), U36.1, U36.10
USBC1_SSEQ0: R130.1, R131.1, U33.11 (SSEQ0/A0)
USBC1_SSEQ1: R132.1, R133.1, U33.3 (SSEQ1)
USBC1_TX1_N: C144.2, U33.34 (TX1_N)
USBC1_TX1_P: C141.2, U33.33 (TX1_P)
USBC1_TX2_N: C145.2, U33.36 (TX2_N)
USBC1_TX2_P: C142.2, U33.37 (TX2_P)
USBC1_VBUS: C153.1, C154.2, D22.1 (C), J9.A4 (VBUS), J9.A9 (VBUS), J9.B4 (VBUS), J9.B9 (VBUS), R157.2, TP20.1, U30.13 (VBUS1), U35.1 (OUT)
USBC_HPD: R118.1, TP17.1
USBPD1_HV: C136.1, C138.1, U30.11 (PP_HV1)
USBSS1.RX+: C127.1
USBSS1.RX-: C129.1
USBSS1.TX+: C128.1
USBSS1.TX-: C130.1
USBSS1_RX_C_N: C129.2, U33.4 (SSRX_N)
USBSS1_RX_C_P: C127.2, U33.5 (SSRX_P)
USBSS1_TX_C_N: C130.2, U33.7 (SSTX_N)
USBSS1_TX_C_P: C128.2, U33.8 (SSTX_P)

Notes on the sheet:
USB Display port alt mode
I_{LIM}(A) = 6800/R_{LIM} = 3.09
4 LANE DP
USB ONLY
USB + 2 LANE DP
CTL0
CTL1
USB PORT 1
CONFIGURATION
POWER DOWN
