antmicro/jetson-agx-thor-baseboard/usb_hub.kicad_sch

## KiCad design usb_hub.kicad_sch (2026-03-19, an earlier design)

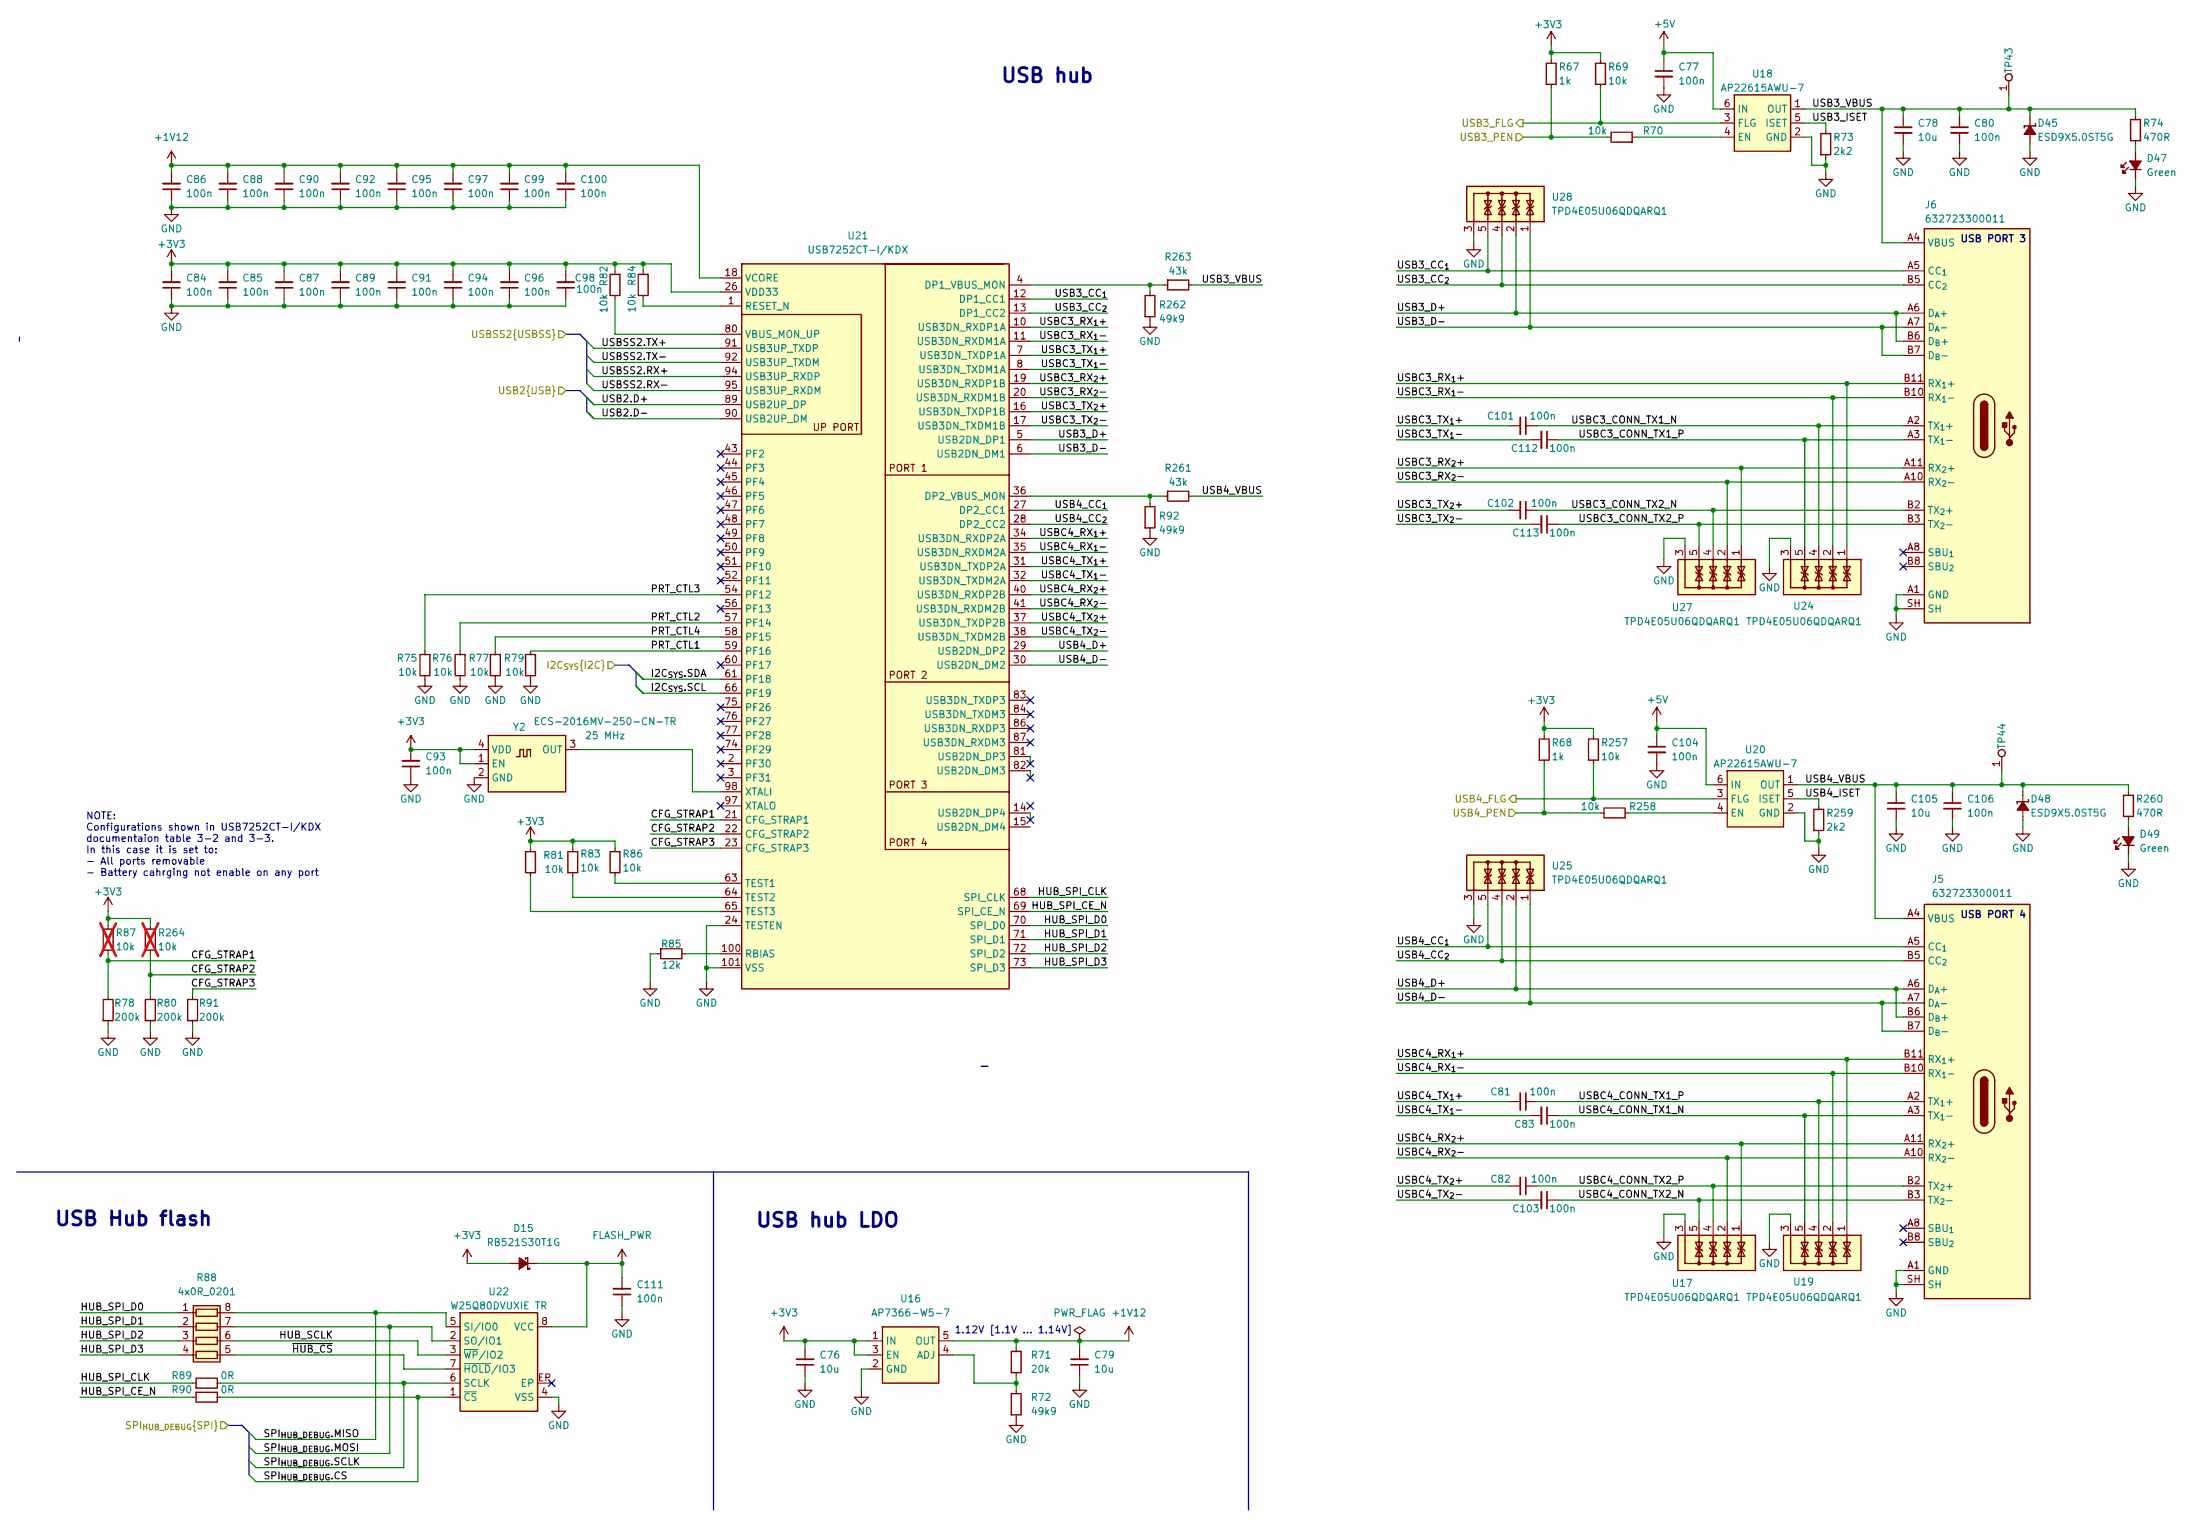
[picture p17: schematic usb_hub.kicad_sch]

Parts:
C76, C79: C_10u_0402; C_0402_1005Metric; MPN CC0402MRX5R5BB106
C77, C80, C104, C106, C111: C_100n_0402; C_0402_1005Metric; Voltage 50V; MPN GRM155R61H104KE14D
C78, C105: C_10u_0603; C_0603_1608Metric; MPN GRM188R61A106KE69D
C81, C82, C83, C101, C102, C103, C112, C113: C_100n_0201; C_0201; MPN CC0201KRX6S5BB104
C84, C85, C86, C87, C88, C89, C90, C91, C92, C94, C95, C96, C97, C98, C99, C100: C_100n_16V_X7R_0402; C_0402_1005Metric; Voltage 16V; MPN C0402C104J4RAC7411
C93: C_100n_50V_X8L_0402; C_0402_1005Metric; Voltage 50V; MPN GCM155L8EH104KE07D
D15: RB521S30T1G; SOD-523; MPN RB521S30T1G
D45, D48: ESD9X5.0ST5G; SOD-923; MPN ESD9X5.0ST5G
D47, D49: LED_G_0603_LTST-C190GKT; LED_0603_1608Metric_G; MPN LTST-C190GKT
J5, J6: USB-C_WE_632723300011; USB-C_Receptacle_WE_632723300011; MPN 632723300011
R67, R68: R_1k_0402; R_0402_1005Metric; Tolerance 1%; MPN CR0402-FX-1001GLF
R69, R70, R75, R76, R77, R79, R81, R82, R83, R84, R86, R257, R258: R_10k_0402; R_0402_1005Metric; Tolerance 1%; MPN CR0402-FX-1002GLF
R71: R_20k_0402; R_0402_1005Metric; Tolerance 1%; MPN CR0402-FX-2002GLF
R72, R92, R262: R_49k9_0402; R_0402_1005Metric; Tolerance 1%; MPN CR0402-FX-4992GLF
R73, R259: R_2k2_0402; R_0402_1005Metric; Tolerance 1%; MPN CR0402-FX-2201GLF
R74, R260: R_470R_0402; R_0402_1005Metric; Tolerance 1%; MPN CR0402-FX-4700GLF
R78, R80, R91: R_200k_0402; R_0402_1005Metric; Tolerance 1%; MPN CR0402-FX-2003GLF
R85: R_12k_0402; R_0402_1005Metric; Tolerance 1%; MPN CR0402-FX-1202GLF
R87, R264: R_10k_0402; R_0402_1005Metric; Tolerance 1%; MPN CR0402-FX-1002GLF; not fitted
R88: R_4x0R_0201_array; R_Array_4x0201_Panasonic_EXB18V; MPN EXB-18VR000X
R89, R90: R_0R_0402; R_0402_1005Metric; MPN ERJ2GE0R00X
R261, R263: R_43k_0402; R_0402_1005Metric; Tolerance 1%; MPN CR0402-FX-4302GLF
TP43, TP44: TP_0.75mm_SMD; TP_SMD_0.75mm
U16: AP7366_SOT; SOT-23-5; MPN AP7366-W5-7
U17, U19, U24, U25, U27, U28: TPD4E05U06QDQARQ1; USON-10_2.5x1mm_P0.5mm; MPN TPD4E05U06QDQARQ1
U18, U20: AP22615A_TSOT26; TSOT23-6; MPN AP22615AWU-7
U21: USB7252C; VQFN-100-1EP_12x12x0.85mm_P0.4mm; MPN USB7252CT-I/KDX
U22: W25Q80DV_USON; USON-8_2x3mm_P0.5mm; MPN W25Q80DVUXIE TR
Y2: Oscillator_25MHz_ESC_2016MV; Oscillator_SMD_ECS_2016MV_2x1.6x0.85mm; MPN ECS-2016MV-250-CN-TR

Connections:
+1V12: C79.2, C86.2, C88.2, C90.2, C92.2, C95.2, C97.2, C99.2, C100.2, R71.2, U16.5 (OUT), U21.9 (VCORE), U21.18 (VCORE), U21.25 (VCORE), U21.33 (VCORE), U21.39 (VCORE), U21.55 (VCORE), U21.78 (VCORE), U21.85 (VCORE), U21.93 (VCORE)
+3V3: C76.2, C84.2, C85.2, C87.2, C89.2, C91.2, C93.2, C94.2, C96.2, C98.2, D15.2 (A), R67.2, R68.2, R69.2, R81.1, R82.1, R83.1, R84.1, R86.1, R87.2, R257.2, R264.2, U16.1 (IN), U16.3 (EN), U21.26 (VDD33), U21.42 (VDD33), U21.53 (VDD33), U21.62 (VDD33), U21.67 (VDD33), U21.79 (VDD33), U21.88 (VDD33), U21.99 (VDD33), Y2.1 (EN), Y2.4 (VDD)
+5V: C77.1, C104.1, U18.6 (IN), U20.6 (IN)
CFG_STRAP1: R78.2, R87.1, U21.21 (CFG_STRAP1)
CFG_STRAP2: R80.2, R264.1, U21.22 (CFG_STRAP2)
CFG_STRAP3: R91.2, U21.23 (CFG_STRAP3)
FLASH_PWR: C111.2, D15.1 (C), U22.8 (VCC)
GND: C76.1, C77.2, C78.2, C79.1, C80.2, C84.1, C85.1, C86.1, C87.1, C88.1, C89.1, C90.1, C91.1, C92.1, C93.1, C94.1, C95.1, C96.1, C97.1, C98.1, C99.1, C100.1, C104.2, C105.2, C106.2, C111.1, D45.2 (A), D47.1 (C), D48.2 (A), D49.1 (C), J5.A1 (GND), J5.A12 (GND), J5.B1 (GND), J5.B12 (GND), J5.SH, J6.A1 (GND), J6.A12 (GND), J6.B1 (GND), J6.B12 (GND), J6.SH, R72.1, R73.1, R75.2, R76.2, R77.2, R78.1, R79.2, R80.1, R85.1, R91.1, R92.1, R259.1, R262.1, U16.2 (GND), U17.3, U17.8, U18.2 (GND), U19.3, U19.8, U20.2 (GND), U21.24 (TESTEN), U21.101 (VSS), U22.4 (VSS), U24.3, U24.8, U25.3, U25.8, U27.3, U27.8, U28.3, U28.8, Y2.2 (GND)
HUB_SCLK: R88.6 (R3.2), U22.3 (~WP/IO2)
HUB_SPI_CE_N: R90.1, U21.69 (SPI_CE_N)
HUB_SPI_CLK: R89.1, U21.68 (SPI_CLK)
HUB_SPI_D0: R88.1 (R1.1), U21.70 (SPI_D0)
HUB_SPI_D1: R88.2 (R2.1), U21.71 (SPI_D1)
HUB_SPI_D2: R88.3 (R3.1), U21.72 (SPI_D2)
HUB_SPI_D3: R88.4 (R4.1), U21.73 (SPI_D3)
I2C_{SYS}.SCL: U21.66 (PF19)
I2C_{SYS}.SDA: U21.61 (PF18)
unnamed: D47.2 (A), R74.1
unnamed: D49.2 (A), R260.1
unnamed: R70.1, U18.4 (EN)
unnamed: R71.1, R72.2, U16.4 (ADJ)
unnamed: R81.2, U21.65 (TEST3)
unnamed: R82.2, U21.80 (VBUS_MON_UP)
unnamed: R83.2, U21.64 (TEST2)
unnamed: R84.2, U21.1 (RESET_N)
unnamed: R85.2, U21.100 (RBIAS)
unnamed: R86.2, U21.63 (TEST1)
unnamed: R258.1, U20.4 (EN)
unnamed: R92.2, R261.1, U21.36 (DP2_VBUS_MON)
unnamed: R262.2, R263.1, U21.4 (DP1_VBUS_MON)
unnamed: U21.98 (XTALI), Y2.3 (OUT)
PRT_CTL1: R79.1, U21.59 (PF16)
PRT_CTL2: R76.1, U21.57 (PF14)
PRT_CTL3: R75.1, U21.54 (PF12)
PRT_CTL4: R77.1, U21.58 (PF15)
SPI_{HUB_DEBUG}.CS: R90.2, U22.1 (~CS)
SPI_{HUB_DEBUG}.MISO: R88.8 (R1.2), U22.5 (SI/IO0)
SPI_{HUB_DEBUG}.MOSI: R88.7 (R2.2), U22.2 (SO/IO1)
SPI_{HUB_DEBUG}.SCLK: R89.2, U22.6 (SCLK)
USB2.D+: U21.89 (USB2UP_DP)
USB2.D-: U21.90 (USB2UP_DM)
USB3_CC_{1}: J6.A5 (CC_{1}), U21.12 (DP1_CC1), U28.5, U28.6
USB3_CC_{2}: J6.B5 (CC_{2}), U21.13 (DP1_CC2), U28.4, U28.7
USB3_D+: J6.A6 (D_{A}+), J6.B6 (D_{B}+), U21.5 (USB2DN_DP1), U28.2, U28.9
USB3_D-: J6.A7 (D_{A}-), J6.B7 (D_{B}-), U21.6 (USB2DN_DM1), U28.1, U28.10
USB3_FLG: R69.1, U18.3 (FLG)
USB3_ISET: R73.2, U18.5 (ISET)
USB3_PEN: R67.1, R70.2
USB3_VBUS: C78.1, C80.1, D45.1 (C), J6.A4 (VBUS), J6.A9 (VBUS), J6.B4 (VBUS), J6.B9 (VBUS), R74.2, R263.2, TP43.1, U18.1 (OUT)
USB4_CC_{1}: J5.A5 (CC_{1}), U21.27 (DP2_CC1), U25.5, U25.6
USB4_CC_{2}: J5.B5 (CC_{2}), U21.28 (DP2_CC2), U25.4, U25.7
USB4_D+: J5.A6 (D_{A}+), J5.B6 (D_{B}+), U21.29 (USB2DN_DP2), U25.2, U25.9
USB4_D-: J5.A7 (D_{A}-), J5.B7 (D_{B}-), U21.30 (USB2DN_DM2), U25.1, U25.10
USB4_FLG: R257.1, U20.3 (FLG)
USB4_ISET: R259.2, U20.5 (ISET)
USB4_PEN: R68.1, R258.2
USB4_VBUS: C105.1, C106.1, D48.1 (C), J5.A4 (VBUS), J5.A9 (VBUS), J5.B4 (VBUS), J5.B9 (VBUS), R260.2, R261.2, TP44.1, U20.1 (OUT)
USBC3_CONN_TX1_N: C101.1, J6.A2 (TX_{1}+), U24.4, U24.7
USBC3_CONN_TX1_P: C112.1, J6.A3 (TX_{1}-), U24.5, U24.6
USBC3_CONN_TX2_N: C102.1, J6.B2 (TX_{2}+), U27.4, U27.7
USBC3_CONN_TX2_P: C113.1, J6.B3 (TX_{2}-), U27.5, U27.6
USBC3_RX_{1}+: J6.B11 (RX_{1}+), U21.10 (USB3DN_RXDP1A), U24.1, U24.10
USBC3_RX_{1}-: J6.B10 (RX_{1}-), U21.11 (USB3DN_RXDM1A), U24.2, U24.9
USBC3_RX_{2}+: J6.A11 (RX_{2}+), U21.19 (USB3DN_RXDP1B), U27.1, U27.10
USBC3_RX_{2}-: J6.A10 (RX_{2}-), U21.20 (USB3DN_RXDM1B), U27.2, U27.9
USBC3_TX_{1}+: C101.2, U21.7 (USB3DN_TXDP1A)
USBC3_TX_{1}-: C112.2, U21.8 (USB3DN_TXDM1A)
USBC3_TX_{2}+: C102.2, U21.16 (USB3DN_TXDP1B)
USBC3_TX_{2}-: C113.2, U21.17 (USB3DN_TXDM1B)
USBC4_CONN_TX1_N: C83.1, J5.A3 (TX_{1}-), U19.5, U19.6
USBC4_CONN_TX1_P: C81.1, J5.A2 (TX_{1}+), U19.4, U19.7
USBC4_CONN_TX2_N: C103.1, J5.B3 (TX_{2}-), U17.5, U17.6
USBC4_CONN_TX2_P: C82.1, J5.B2 (TX_{2}+), U17.4, U17.7
USBC4_RX_{1}+: J5.B11 (RX_{1}+), U19.1, U19.10, U21.34 (USB3DN_RXDP2A)
USBC4_RX_{1}-: J5.B10 (RX_{1}-), U19.2, U19.9, U21.35 (USB3DN_RXDM2A)
USBC4_RX_{2}+: J5.A11 (RX_{2}+), U17.1, U17.10, U21.40 (USB3DN_RXDP2B)
USBC4_RX_{2}-: J5.A10 (RX_{2}-), U17.2, U17.9, U21.41 (USB3DN_RXDM2B)
USBC4_TX_{1}+: C81.2, U21.31 (USB3DN_TXDP2A)
USBC4_TX_{1}-: C83.2, U21.32 (USB3DN_TXDM2A)
USBC4_TX_{2}+: C82.2, U21.37 (USB3DN_TXDP2B)
USBC4_TX_{2}-: C103.2, U21.38 (USB3DN_TXDM2B)
USBSS2.RX+: U21.94 (USB3UP_RXDP)
USBSS2.RX-: U21.95 (USB3UP_RXDM)
USBSS2.TX+: U21.91 (USB3UP_TXDP)
USBSS2.TX-: U21.92 (USB3UP_TXDM)
~HUB_CS: R88.5 (R4.2), U22.7 (~HOLD/IO3)

Notes on the sheet:
USB PORT 4
USB hub
1.12V [1.1V ... 1.14V]
USB PORT 3
USB hub LDO
USB Hub flash
NOTE: Configurations shown in USB7252CT-I/KDX documentaion table 3-2 and 3-3. In this case it is set to: - All ports removable - Battery cahrging not enable on any port
